Simulators/simulator-type2/docs/source/Diagrams/Norris/Originals/B&W&C.gif

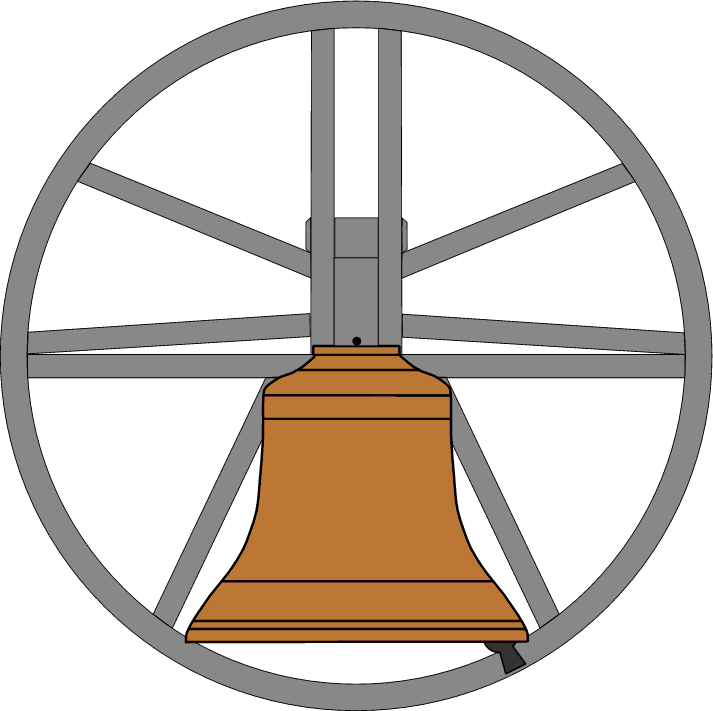
docs/source/Diagrams/Norris/Originals/B&W&C.gif
