Simulators/simulator-type2/docs/source/Diagrams/Norris/Originals/W&R.gif

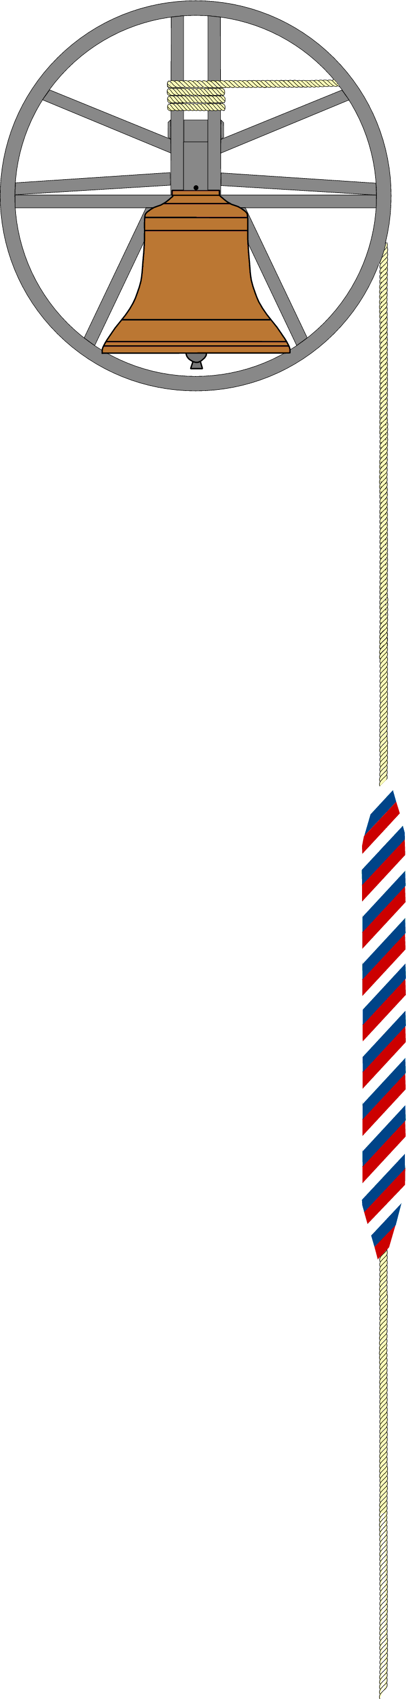
docs/source/Diagrams/Norris/Originals/W&R.gif
