Simulators/simulator-type2/docs/source/Diagrams/Norris/Originals/wheelalone_ORIGINAL.gif

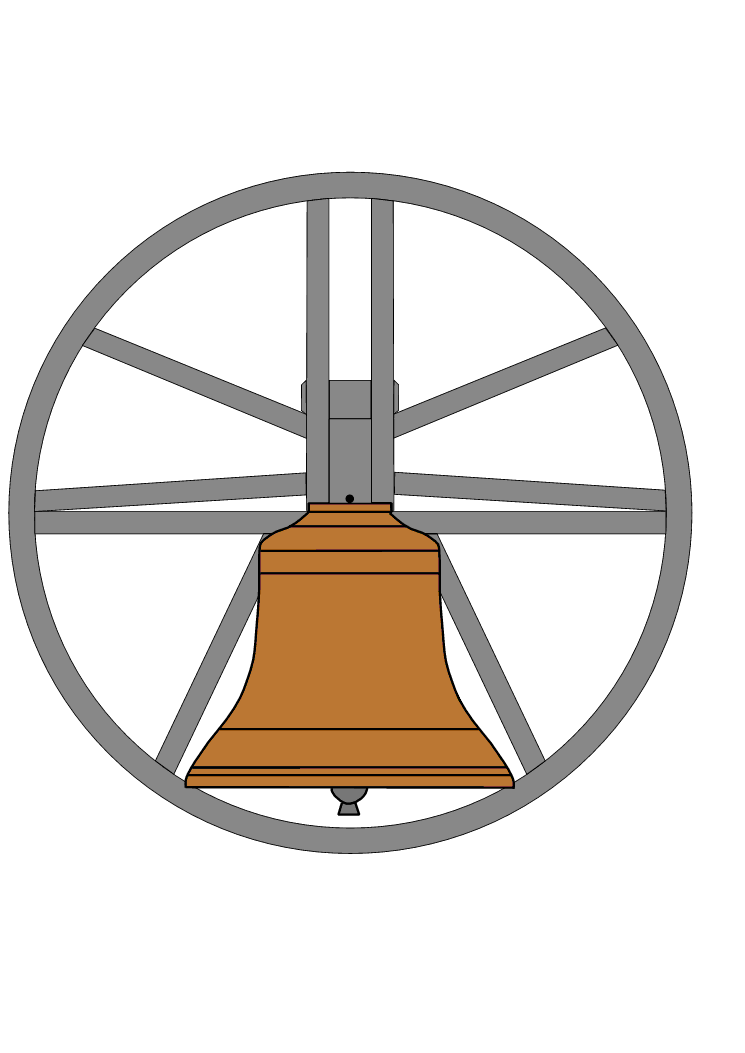
docs/source/Diagrams/Norris/Originals/wheelalone_ORIGINAL.gif
