Simulators/simulator-type2/docs/source/Diagrams/Norris/Remixed/bell_wheel_belldown.gif

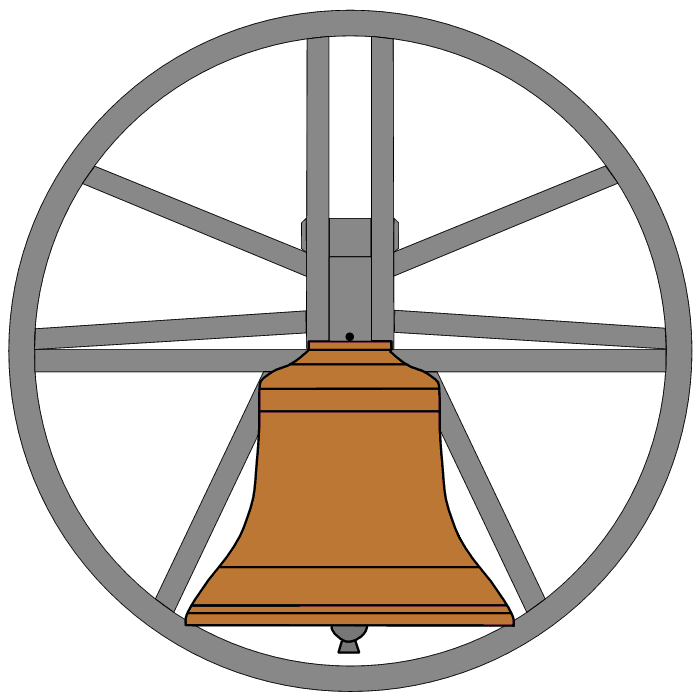
docs/source/Diagrams/Norris/Remixed/bell_wheel_belldown.gif
