Simulators/simulator-type2/docs/source/Diagrams/Norris/Remixed/bell_wheel_clappershift_down_right.gif

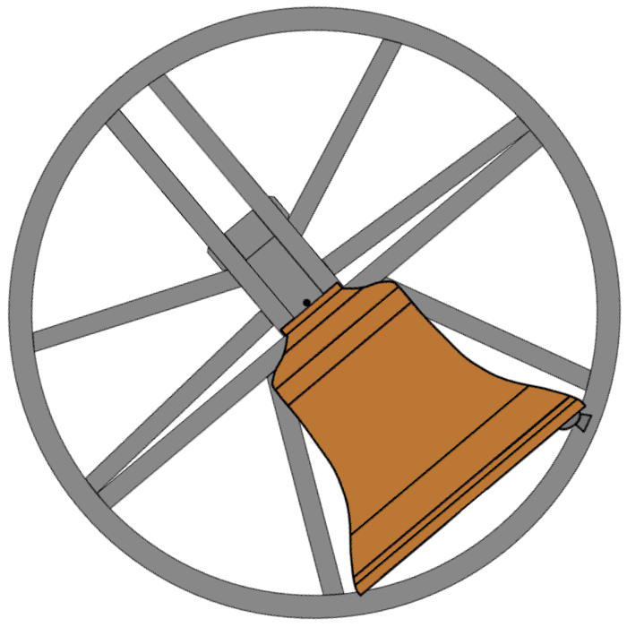
docs/source/Diagrams/Norris/Remixed/bell_wheel_clappershift_down_right.gif
