Simulators/simulator-type2/docs/source/Diagrams/Norris/Remixed/bell_wheel_clappershift_left.gif

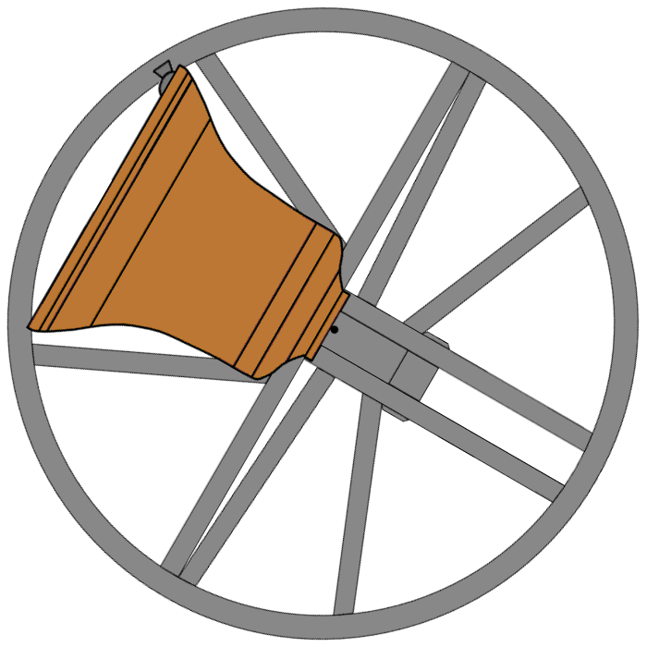
docs/source/Diagrams/Norris/Remixed/bell_wheel_clappershift_left.gif
