Simulators/simulator-type2/docs/source/Diagrams/Norris/Remixed/bell_wheel_clappershift_right.gif

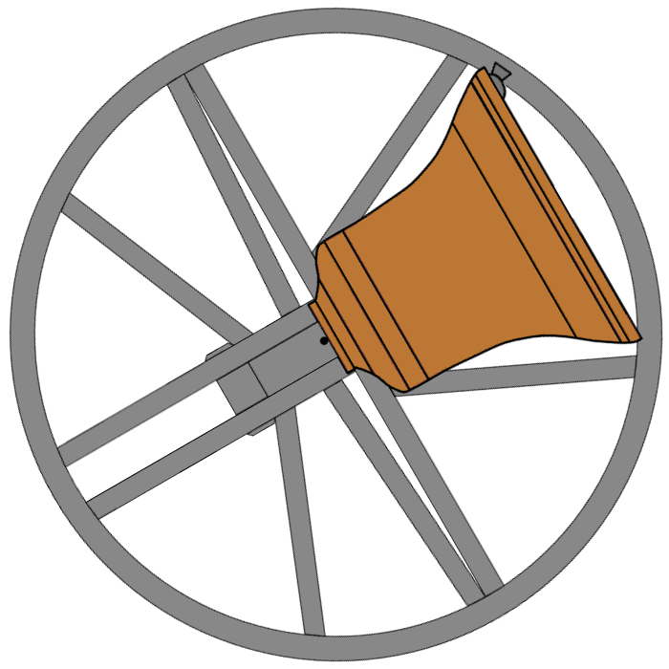
docs/source/Diagrams/Norris/Remixed/bell_wheel_clappershift_right.gif
