Simulators/simulator-type2/docs/source/Diagrams/Norris/Remixed/positions_twin_sensor_down_v0.1.png

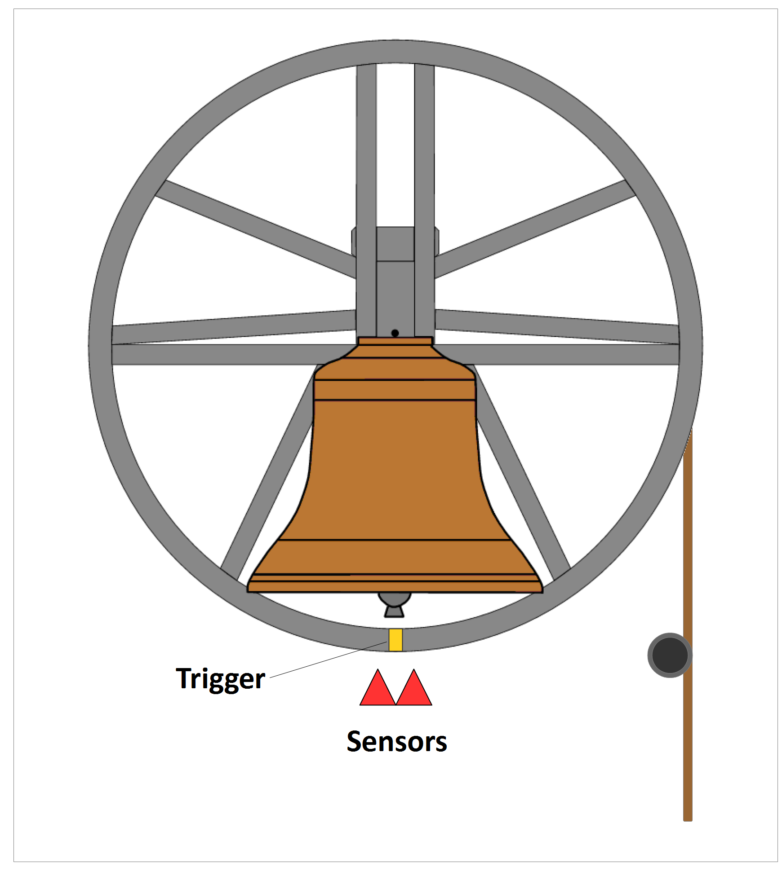
docs/source/Diagrams/Norris/Remixed/positions_twin_sensor_down_v0.1.png
