Simulators/simulator-type2/docs/source/Diagrams/Norris/Remixed/positions_twin_trigger_down_v0.1.png

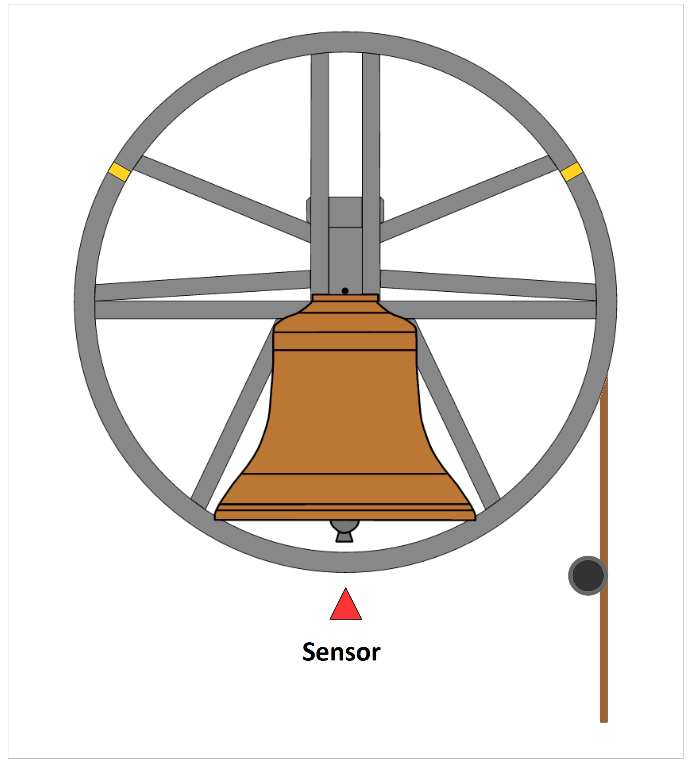
docs/source/Diagrams/Norris/Remixed/positions_twin_trigger_down_v0.1.png
