Simulators/simulator-type2/docs/source/Diagrams/PNG/06 Tech Ref/MAXIM FanOut Rx Diagram v1.0.png

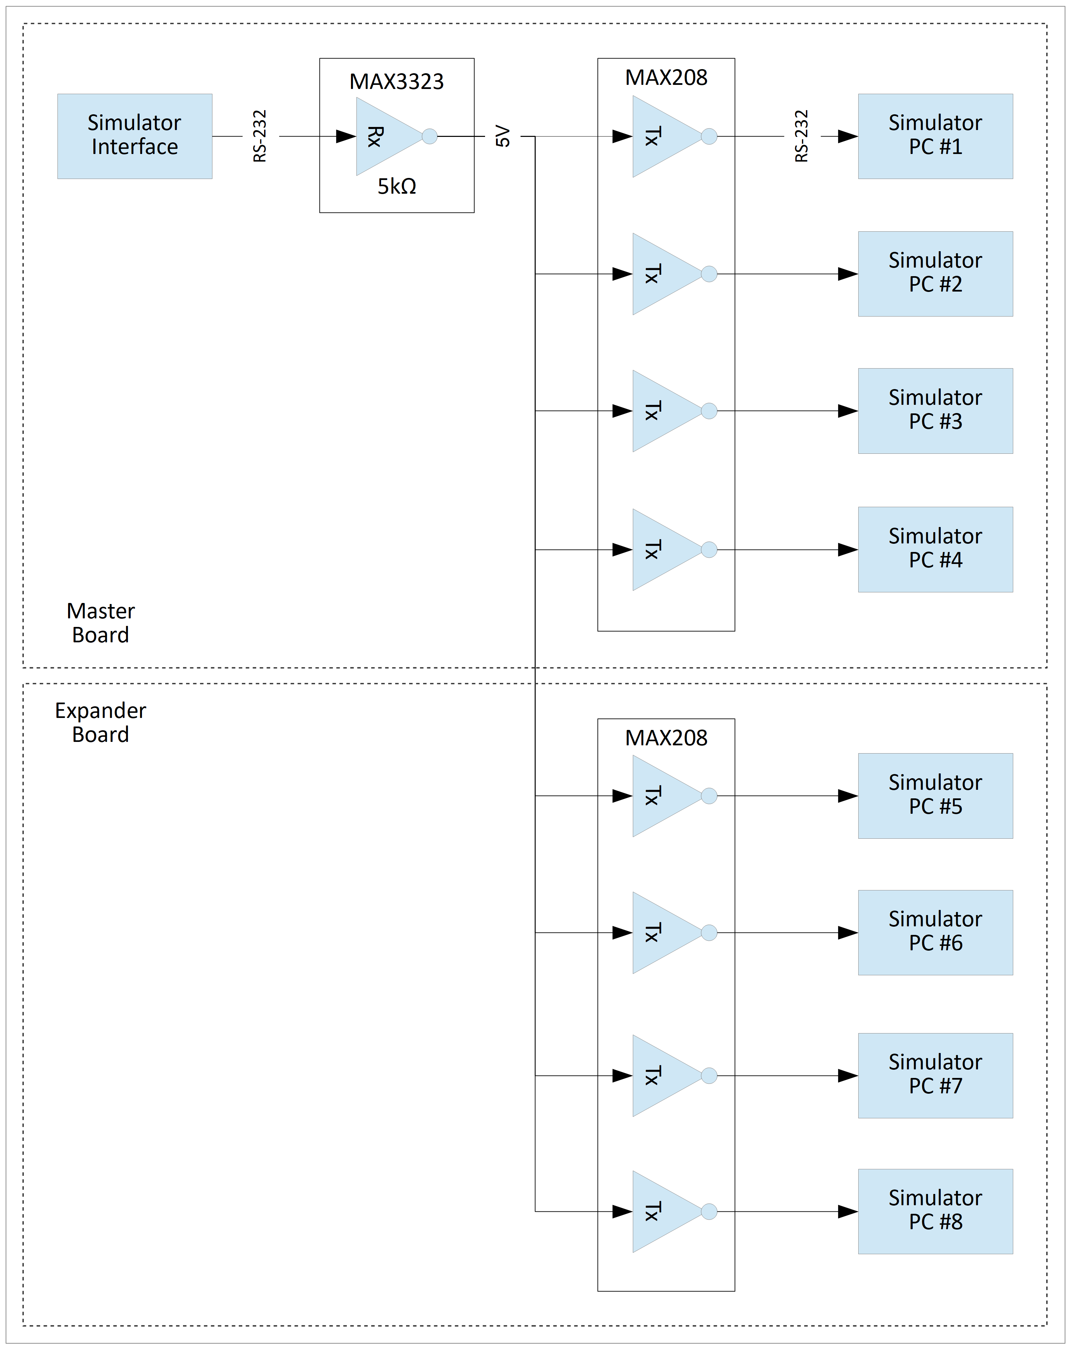
docs/source/Diagrams/PNG/06 Tech Ref/MAXIM FanOut Rx Diagram v1.0.png
