Simulators/simulator-type2/docs/source/Diagrams/PNG/06 Tech Ref/T1-T2 Adapter Cable v1.0.png

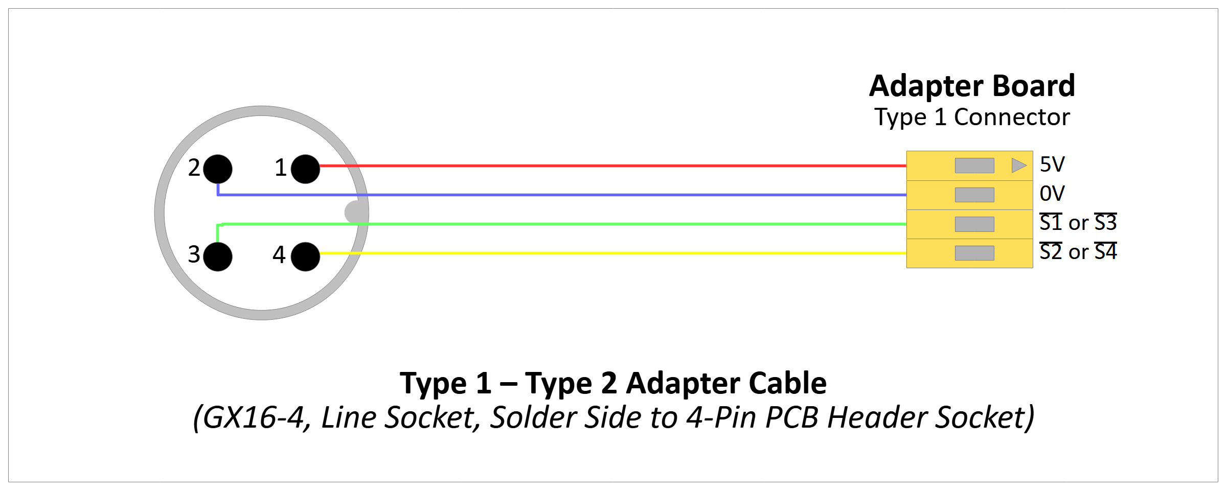
docs/source/Diagrams/PNG/06 Tech Ref/T1-T2 Adapter Cable v1.0.png
