Simulators/simulator-type2/docs/source/Diagrams/PNG/06 Tech Ref/T1-T2 Type 1 Interface Dual Connectors v1.0.png

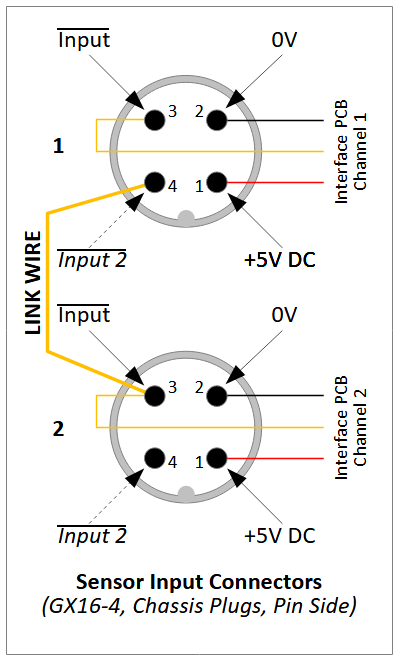
docs/source/Diagrams/PNG/06 Tech Ref/T1-T2 Type 1 Interface Dual Connectors v1.0.png
