Simulators/simulator-type2/docs/source/Diagrams/PNG/06 Tech Ref/T2 Basic Splitter RJ45 Connector v1.0.png

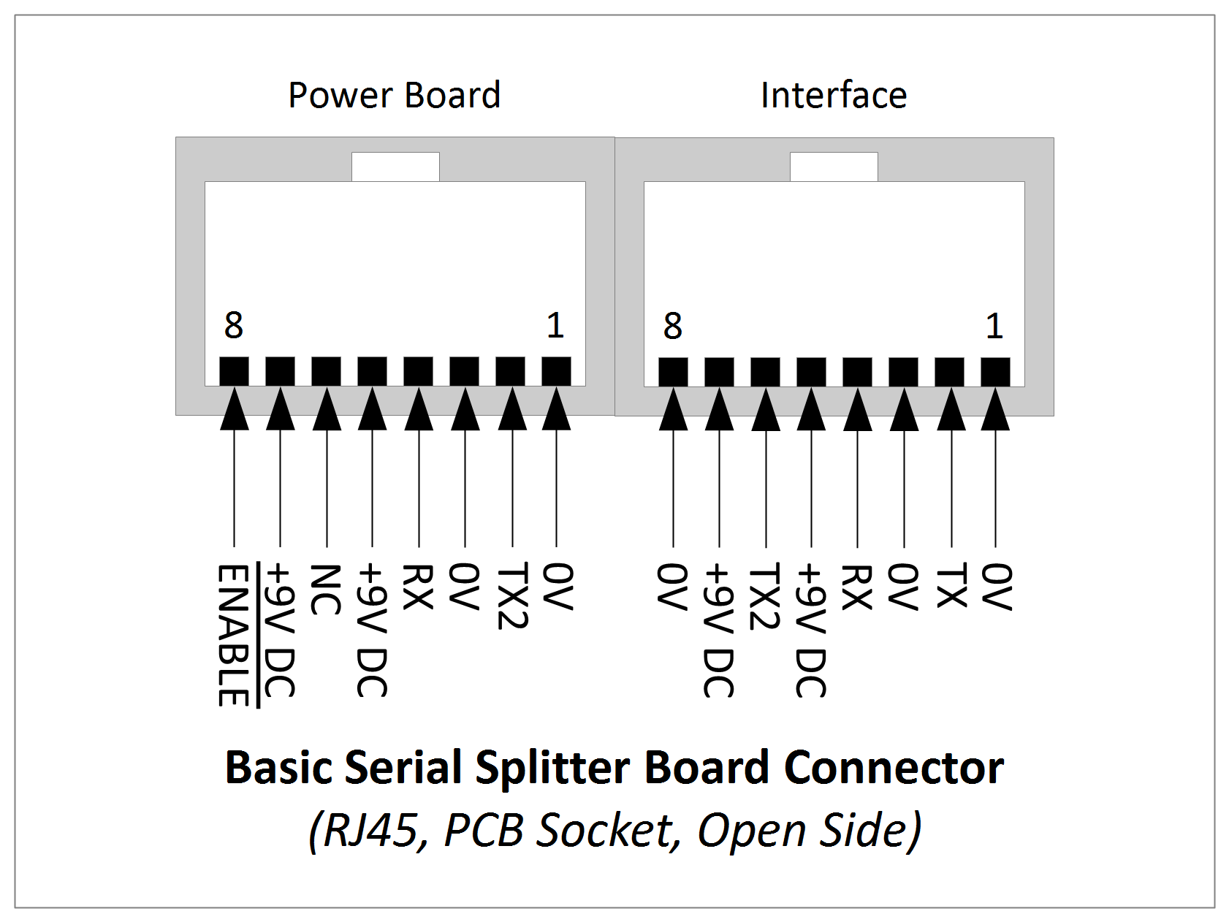
docs/source/Diagrams/PNG/06 Tech Ref/T2 Basic Splitter RJ45 Connector v1.0.png
