Simulators/simulator-type2/docs/source/Diagrams/PNG/06 Tech Ref/T2 Channel Map.png

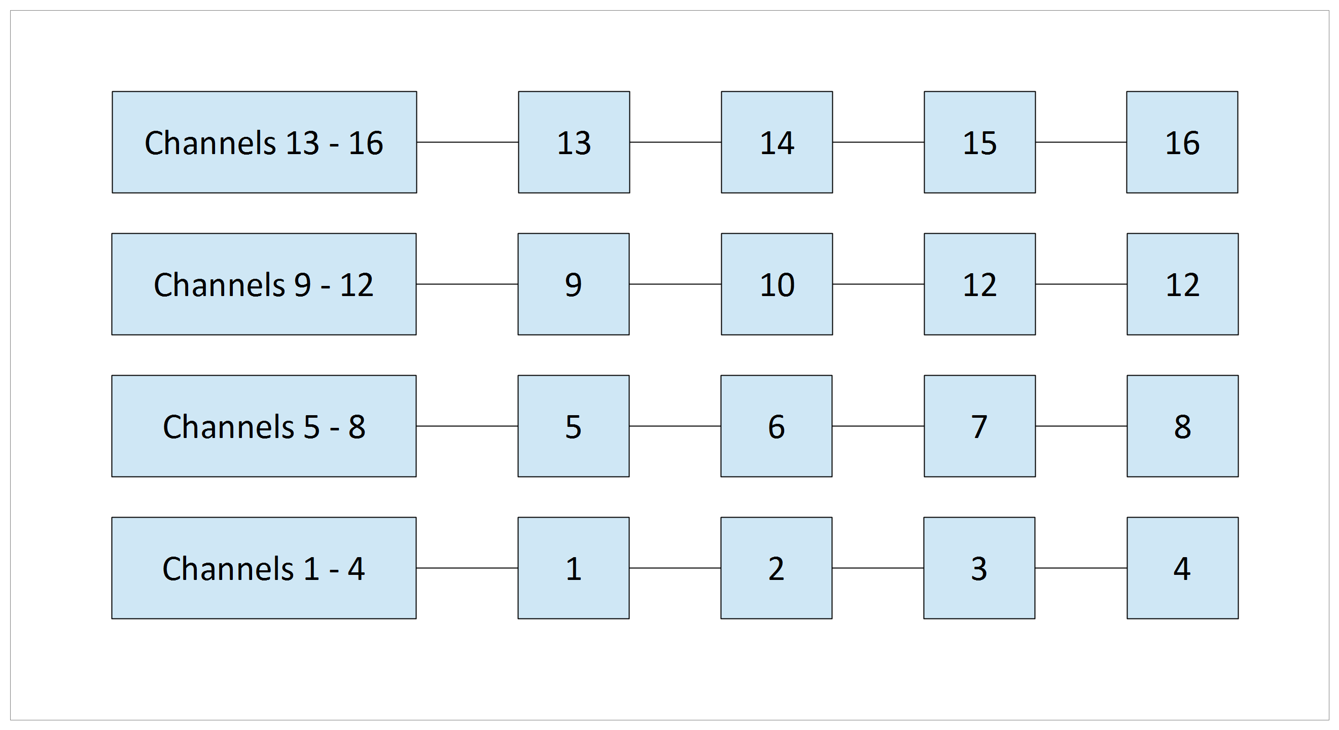
docs/source/Diagrams/PNG/06 Tech Ref/T2 Channel Map.png
