Simulators/simulator-type2/docs/source/Diagrams/PNG/06 Tech Ref/T2 DB9 2nd PC Module v1.0.png

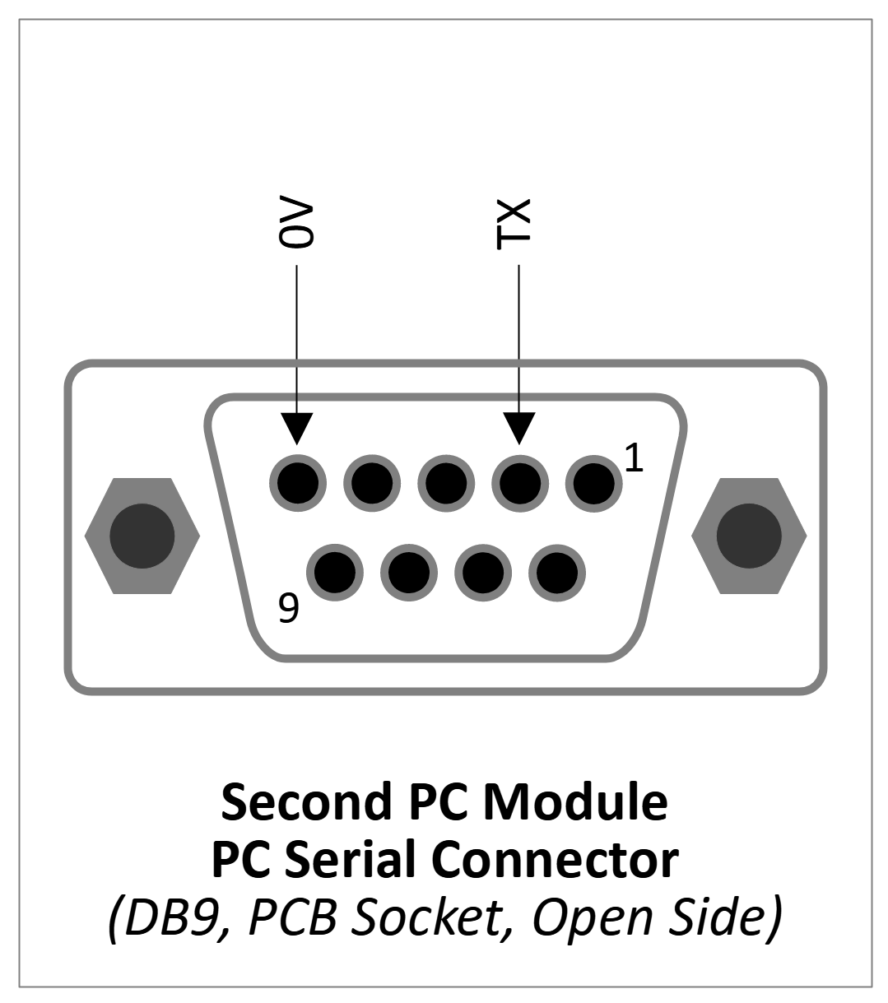
docs/source/Diagrams/PNG/06 Tech Ref/T2 DB9 2nd PC Module v1.0.png
