Simulators/simulator-type2/docs/source/Diagrams/PNG/06 Tech Ref/T2 Double Pulse Diagram v0.1.png

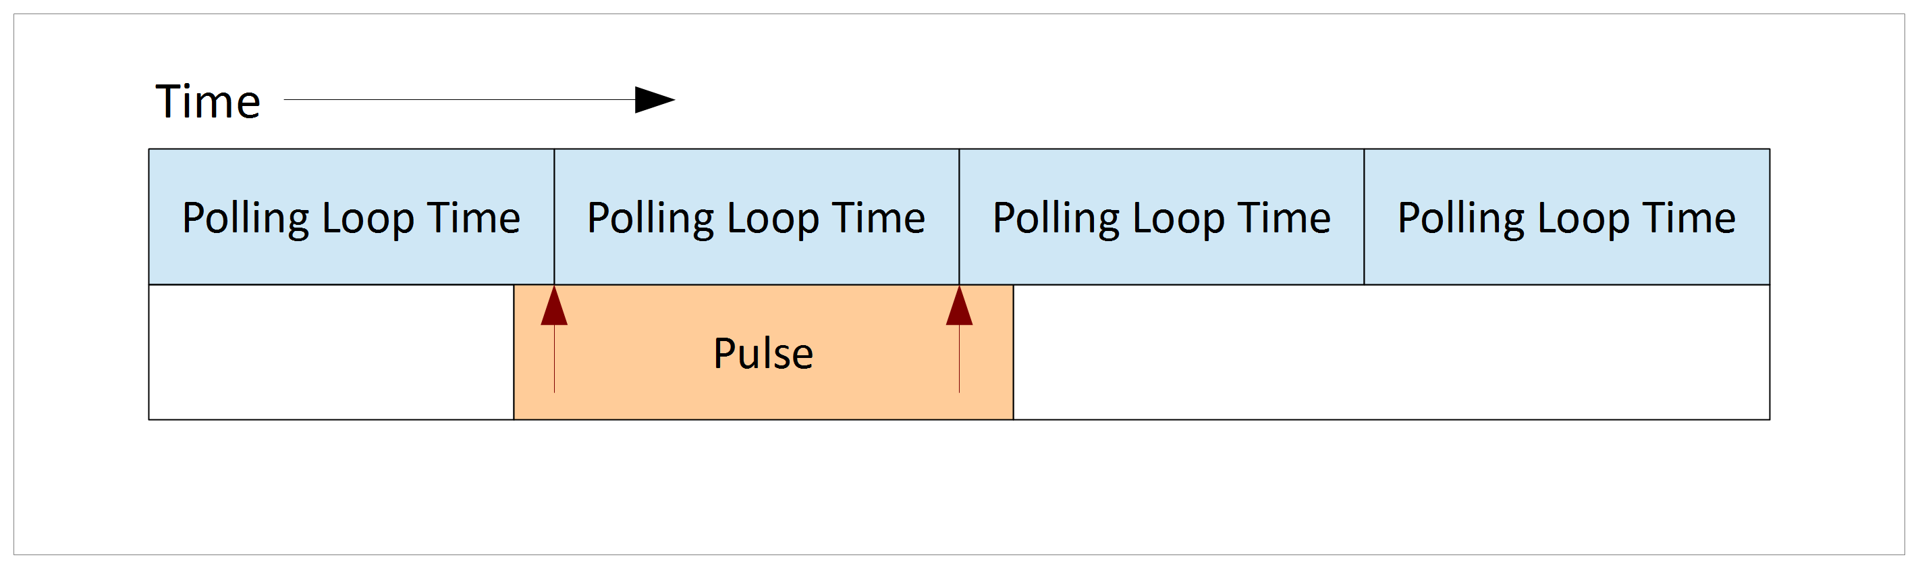
docs/source/Diagrams/PNG/06 Tech Ref/T2 Double Pulse Diagram v0.1.png
