Simulators/simulator-type2/docs/source/Diagrams/PNG/06 Tech Ref/T2 Dual Sensor Backstroke v0.1.png

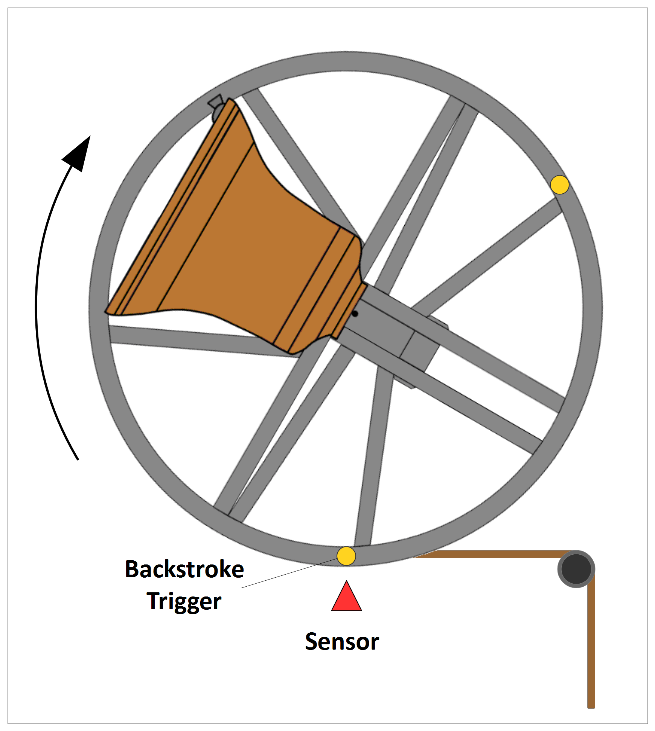
docs/source/Diagrams/PNG/06 Tech Ref/T2 Dual Sensor Backstroke v0.1.png
