Simulators/simulator-type2/docs/source/Diagrams/PNG/06 Tech Ref/T2 Dual Sensor Handstroke v0.1.png

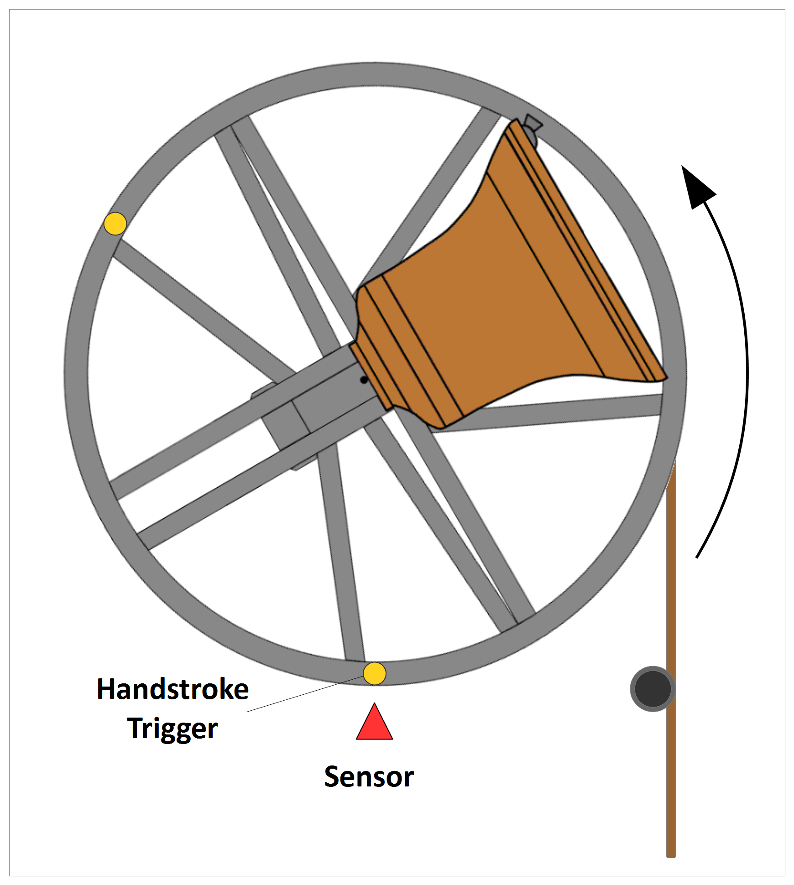
docs/source/Diagrams/PNG/06 Tech Ref/T2 Dual Sensor Handstroke v0.1.png
