Simulators/simulator-type2/docs/source/Diagrams/PNG/06 Tech Ref/T2 Polarity Diode Diagram v1.0.png

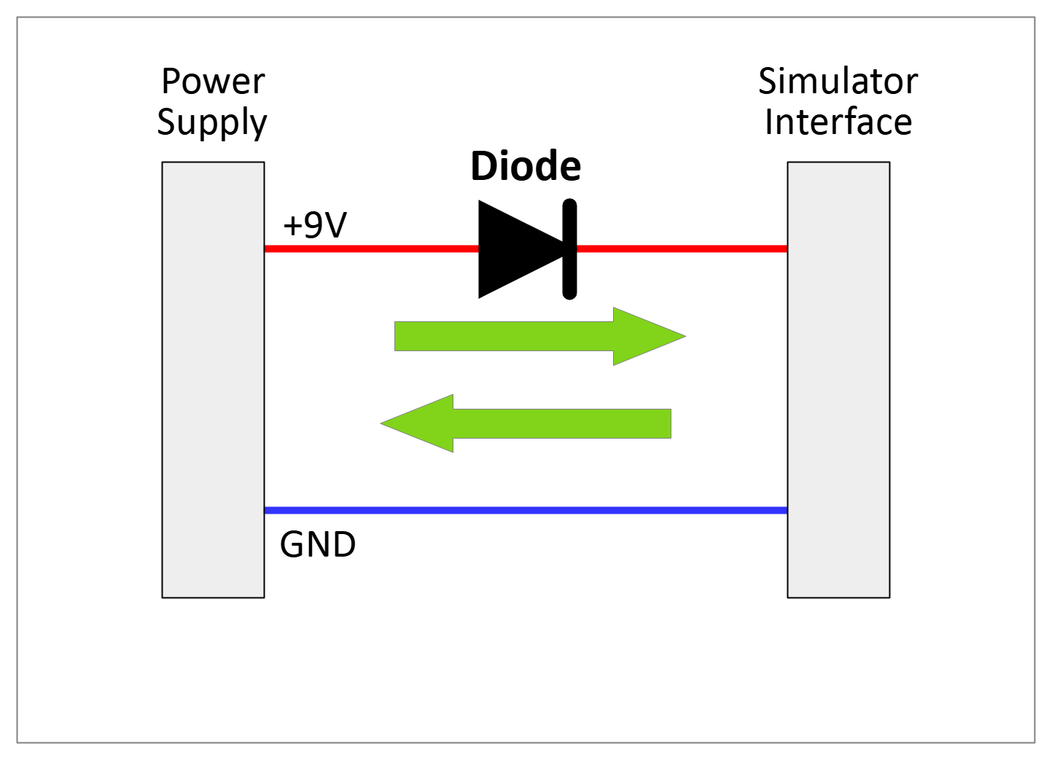
docs/source/Diagrams/PNG/06 Tech Ref/T2 Polarity Diode Diagram v1.0.png
