Simulators/simulator-type2/docs/source/Diagrams/PNG/07 Multi-PC/T2 Basic Splitter Daisy Chain v1.0.png

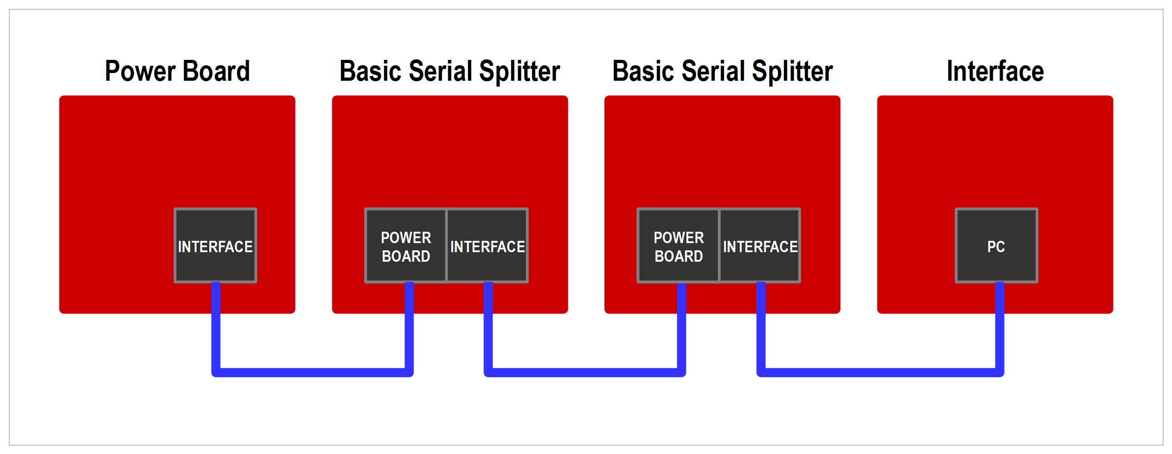
docs/source/Diagrams/PNG/07 Multi-PC/T2 Basic Splitter Daisy Chain v1.0.png
