Simulators/simulator-type2/docs/source/Diagrams/PNG/07 Multi-PC/T2 Basic Splitter Voltages.png

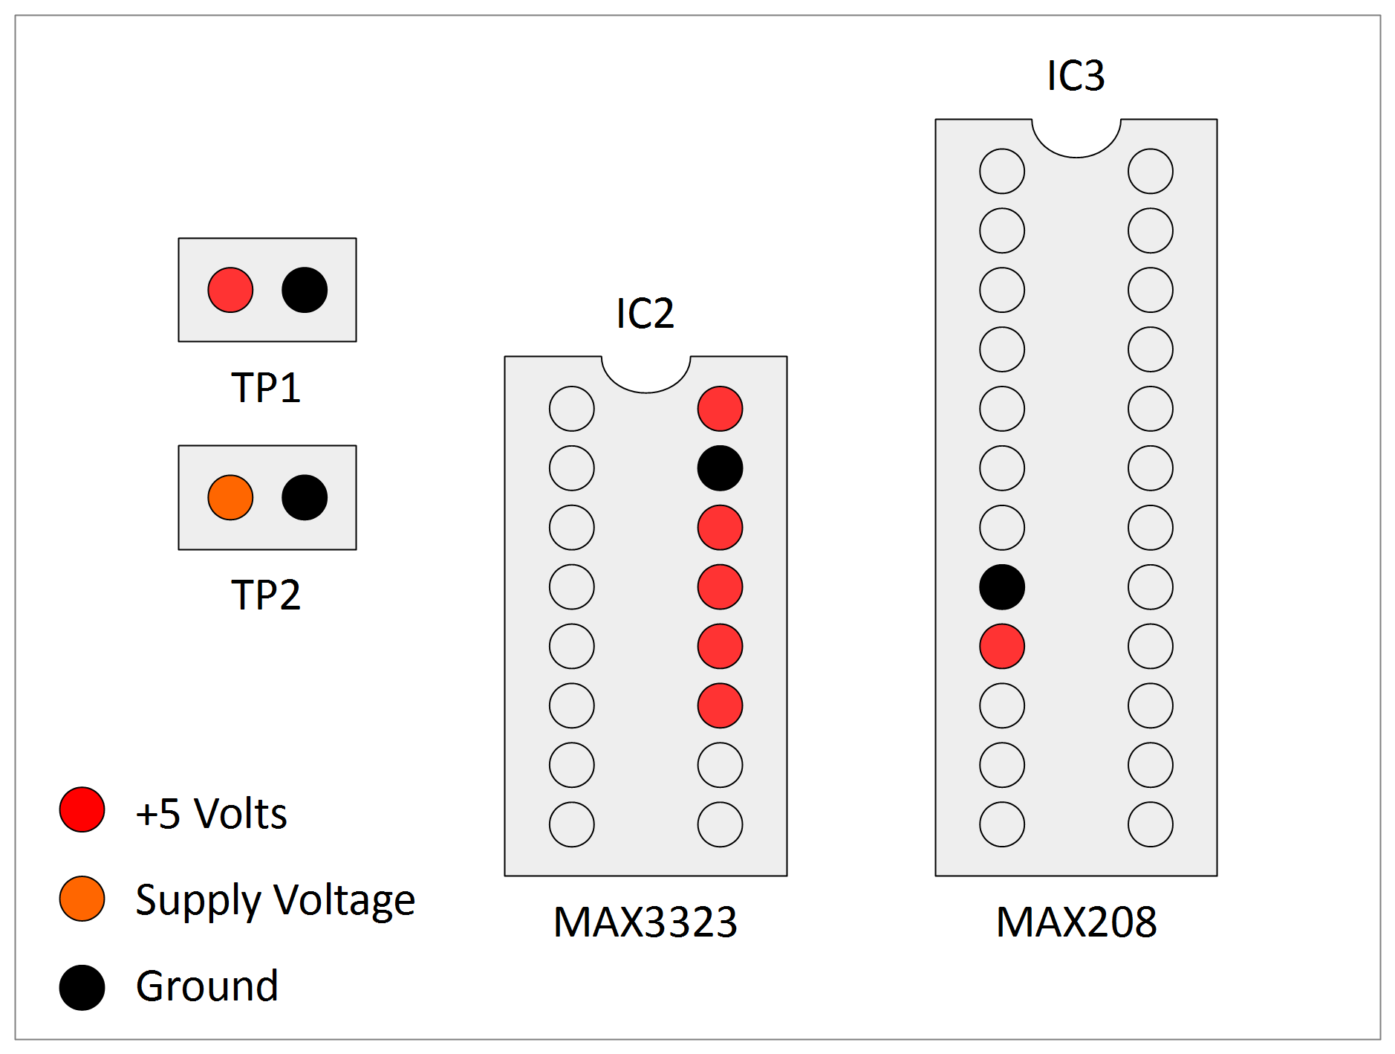
docs/source/Diagrams/PNG/07 Multi-PC/T2 Basic Splitter Voltages.png
