Simulators/simulator-type2/docs/source/Diagrams/PNG/07 Multi-PC/T2 Second PC Daisy Chain v1.0.png

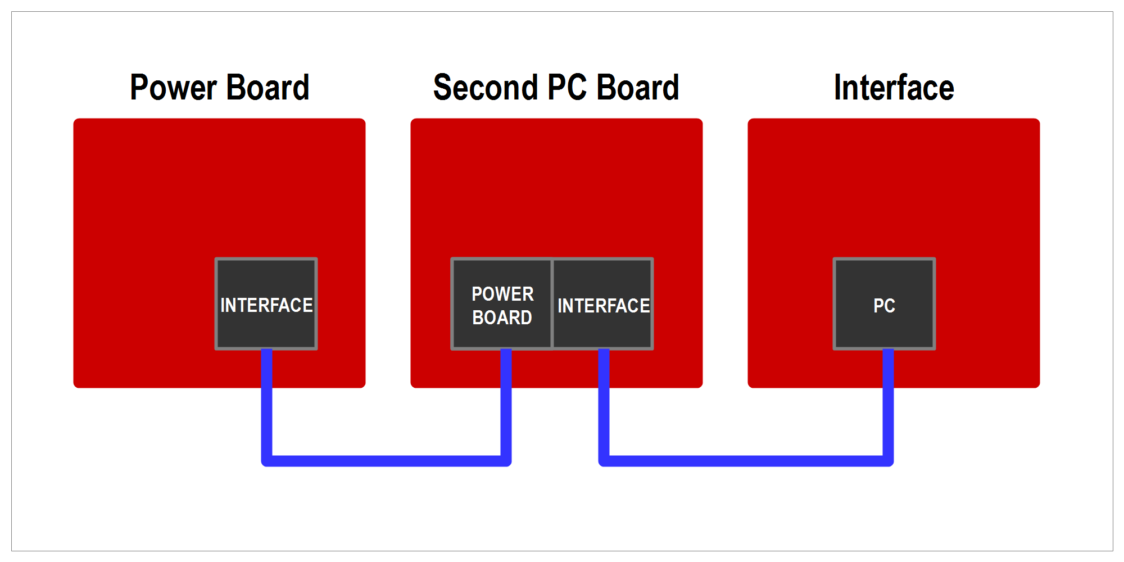
docs/source/Diagrams/PNG/07 Multi-PC/T2 Second PC Daisy Chain v1.0.png
