Simulators/simulator-type2/docs/source/Diagrams/PNG/DocMaps/T2 DocMap 3 Config Abel v2.png

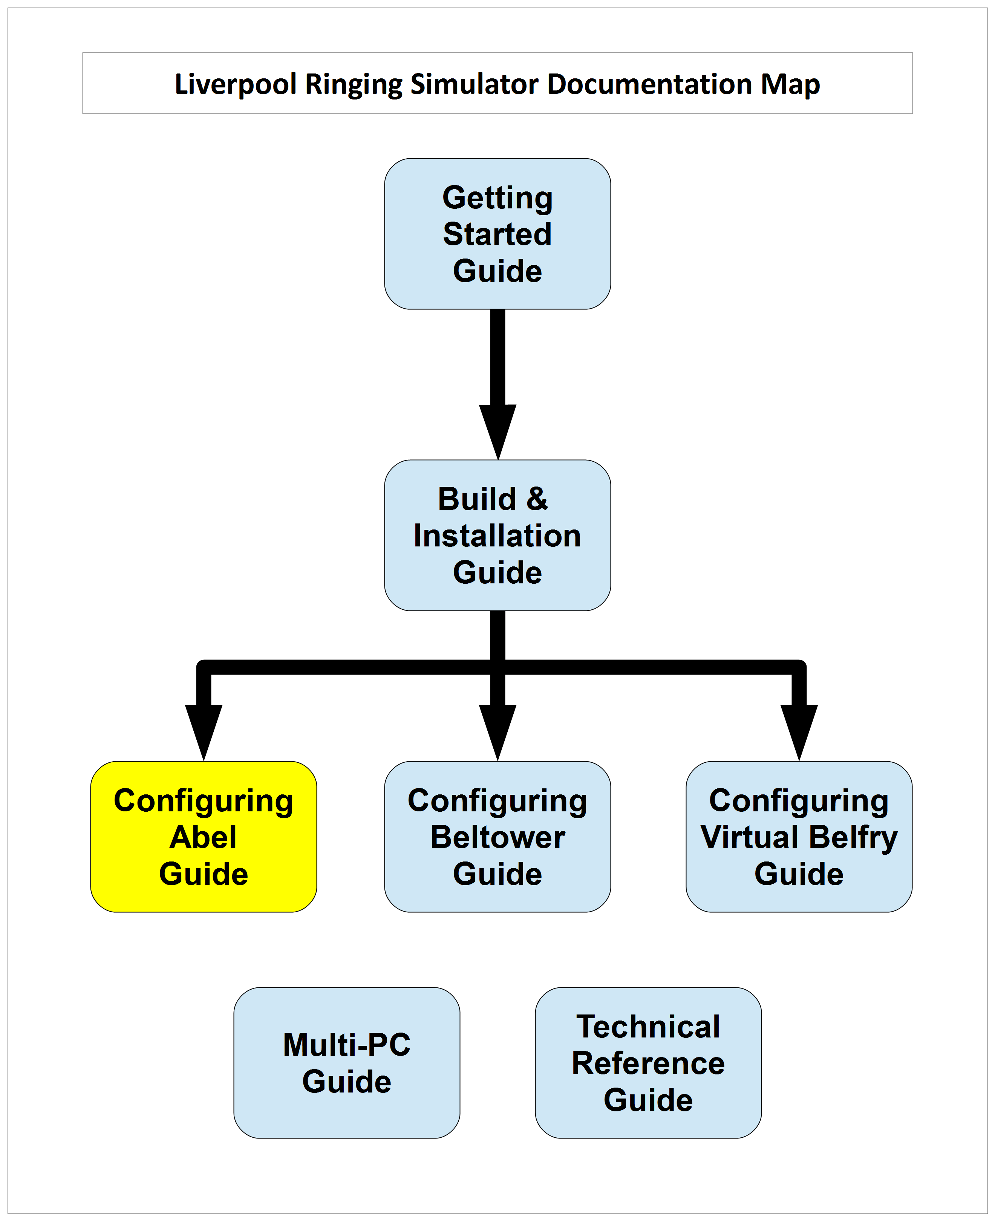
docs/source/Diagrams/PNG/DocMaps/T2 DocMap 3 Config Abel v2.png
