Simulators/simulator-type2/docs/source/Diagrams/PNG/DocMaps/T2 DocMap 4 Config Beltower v2.png

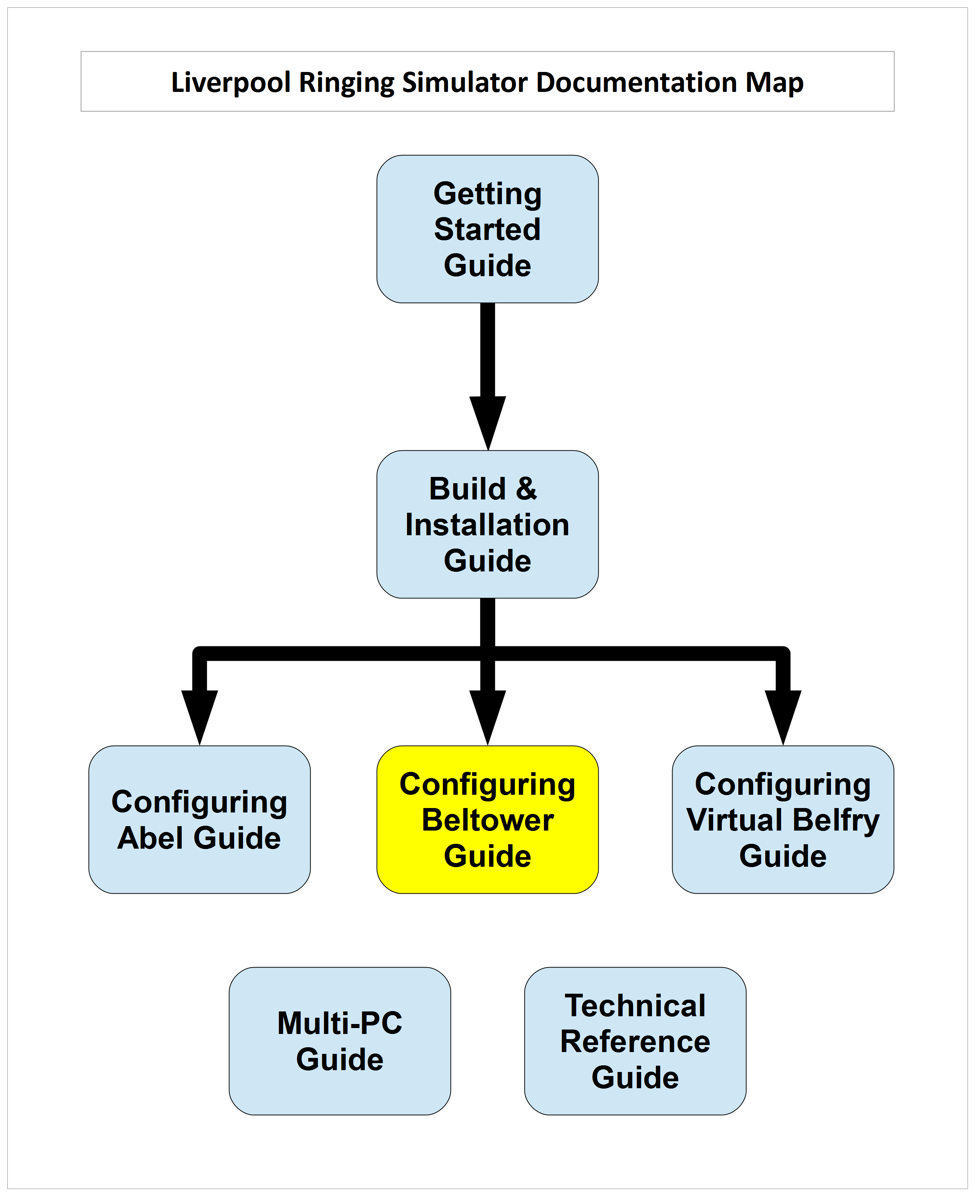
docs/source/Diagrams/PNG/DocMaps/T2 DocMap 4 Config Beltower v2.png
