Simulators/simulator-type2/docs/source/Diagrams/Vecteezy/PC Ports Vecteezy 9Pin.png

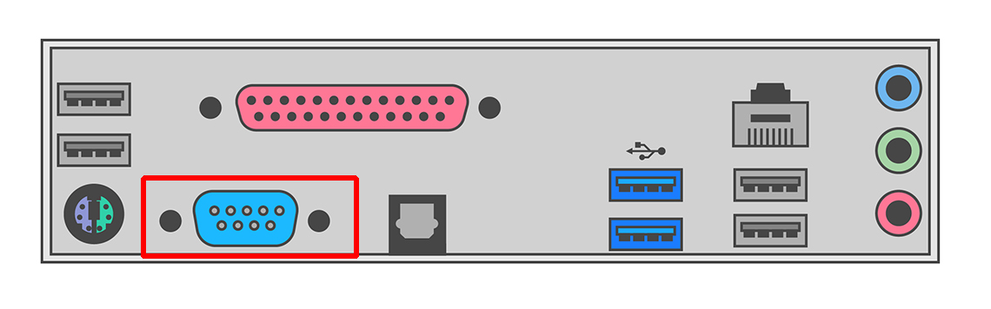
docs/source/Diagrams/Vecteezy/PC Ports Vecteezy 9Pin.png
