Simulators/simulator-type2/docs/source/Diagrams/Vecteezy/PC Ports Vecteezy USB.png

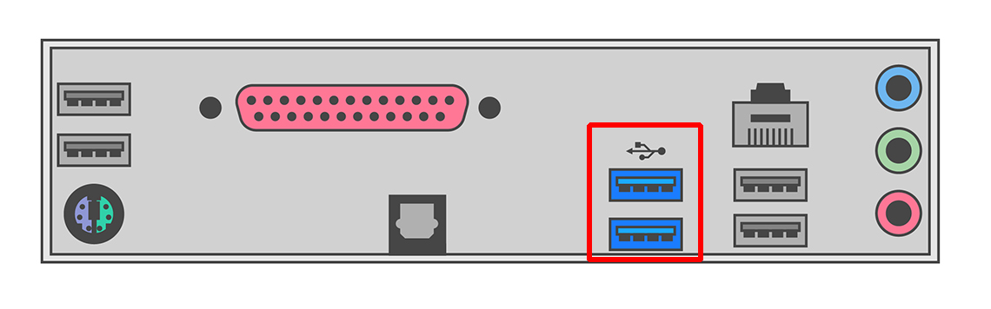
docs/source/Diagrams/Vecteezy/PC Ports Vecteezy USB.png
