Simulators/simulator-type2/docs/source/Diagrams/Vecteezy/USB Port Mother Board Free Vector.jpg

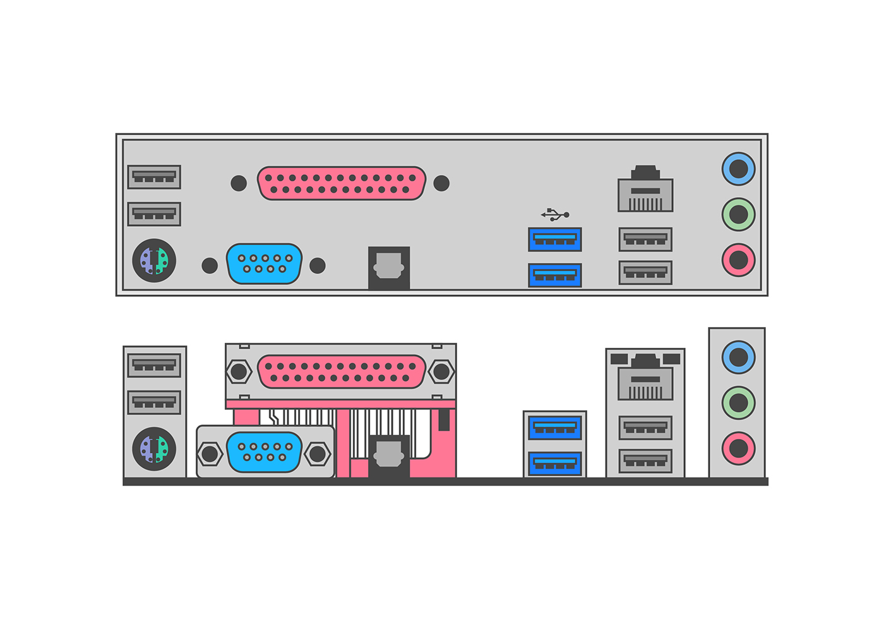
docs/source/Diagrams/Vecteezy/USB Port Mother Board Free Vector.jpg
