Simulators/simulator-type2/docs/source/Images/CRO/DS2302A_20171216-192610.png

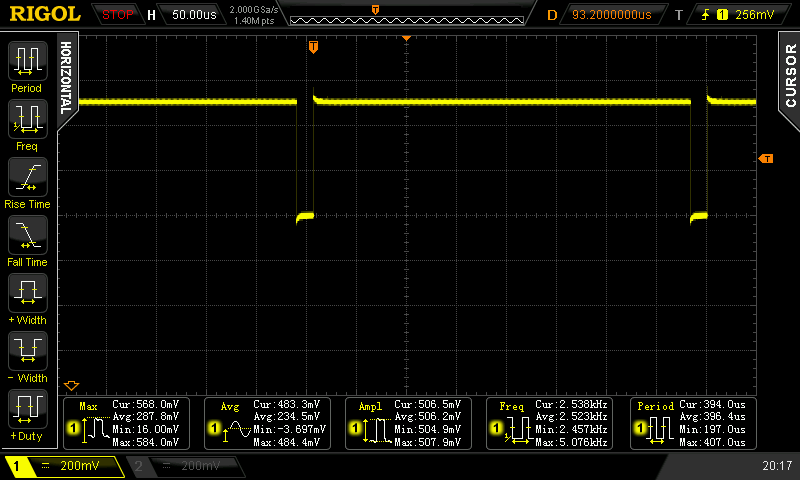
docs/source/Images/CRO/DS2302A_20171216-192610.png
