Simulators/simulator-type2/docs/source/Images/CRO/DS2302A_20180502-181701.png

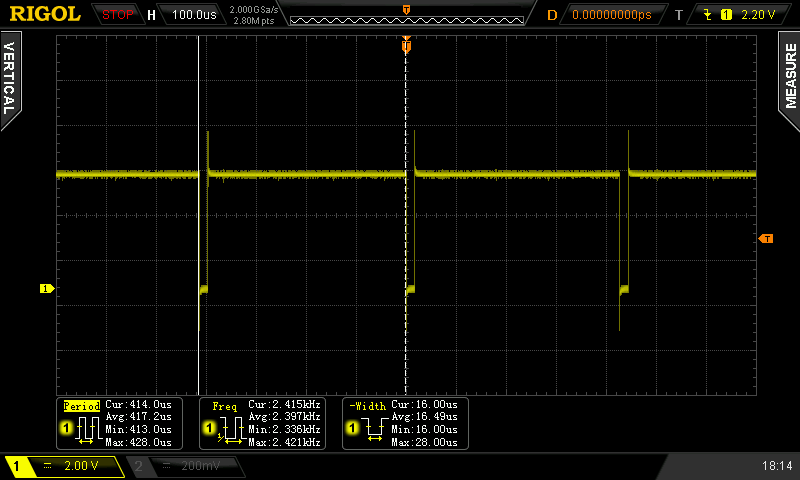
docs/source/Images/CRO/DS2302A_20180502-181701.png
