Simulators/simulator-type2/docs/source/Images/CRO/Latency Scope Annotated.png

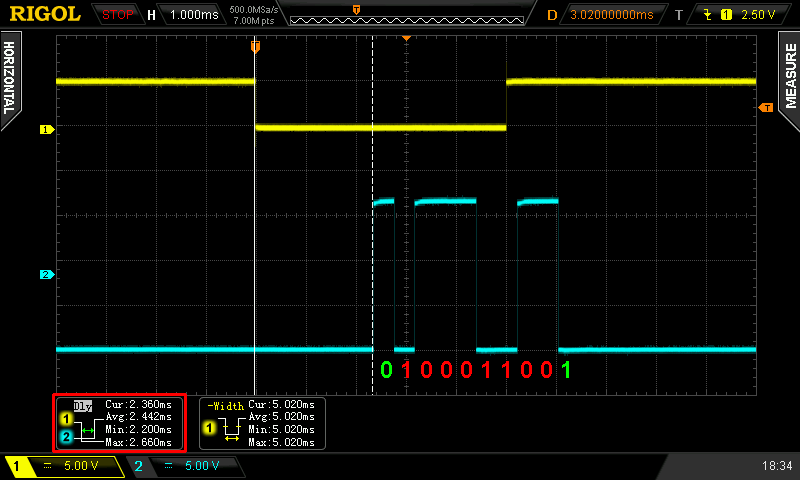
docs/source/Images/CRO/Latency Scope Annotated.png
