Simulators/simulator-type2/docs/source/Images/CRO/sigrok_debounce_timer.PNG

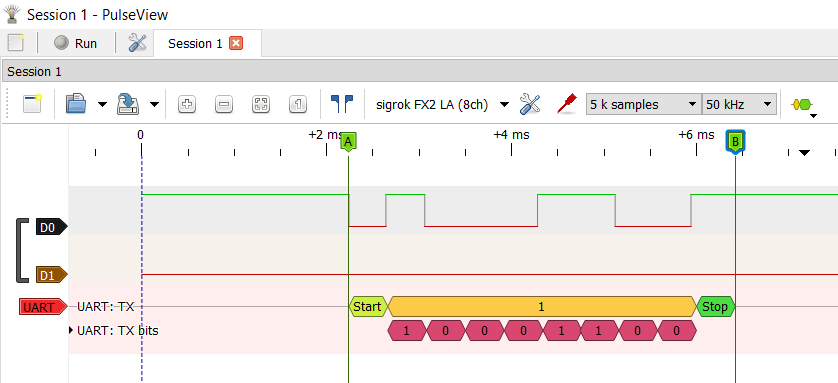
docs/source/Images/CRO/sigrok_debounce_timer.PNG
