Simulators/simulator-type2/docs/source/Images/Hardware/Basic Splitter/Img_0053.jpeg

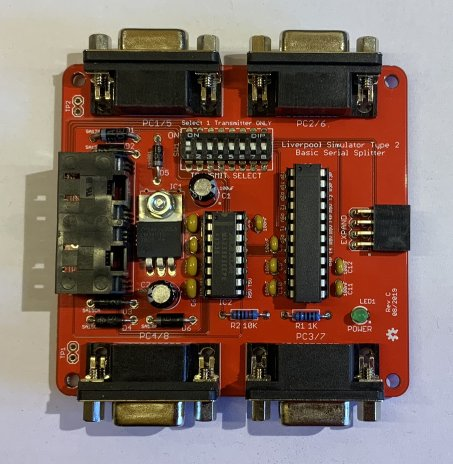
docs/source/Images/Hardware/Basic Splitter/Img_0053.jpeg
