Simulators/simulator-type2/docs/source/Images/Hardware/Basic Splitter/Img_0054.jpeg

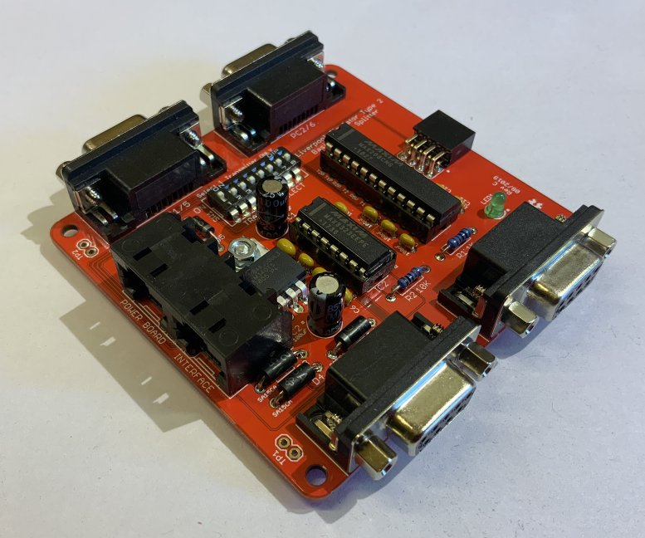
docs/source/Images/Hardware/Basic Splitter/Img_0054.jpeg
