Simulators/simulator-type2/docs/source/Images/Hardware/Basic Splitter/Img_0664.jpg

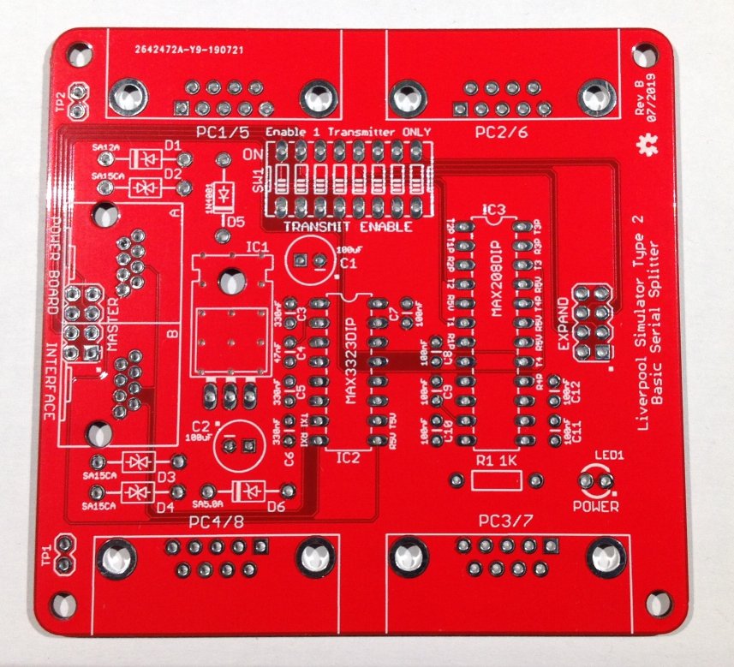
docs/source/Images/Hardware/Basic Splitter/Img_0664.jpg
