Simulators/simulator-type2/docs/source/Images/Hardware/Basic Splitter/Img_0665.jpg

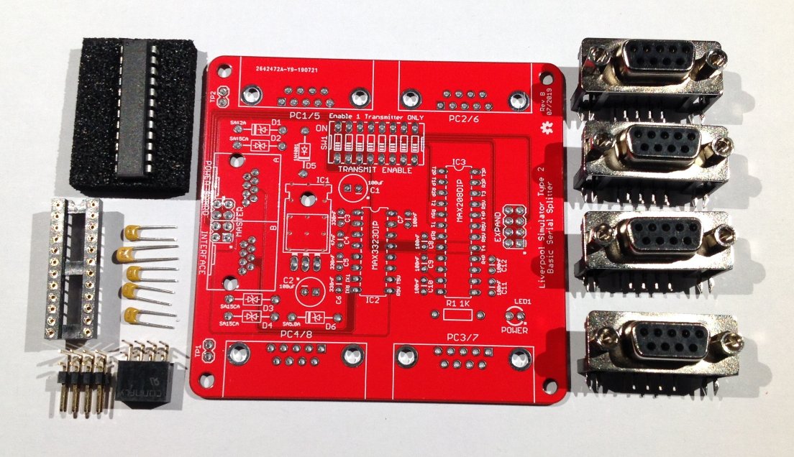
docs/source/Images/Hardware/Basic Splitter/Img_0665.jpg
