Simulators/simulator-type2/docs/source/Images/Hardware/Enclosures/Img_0061.jpeg

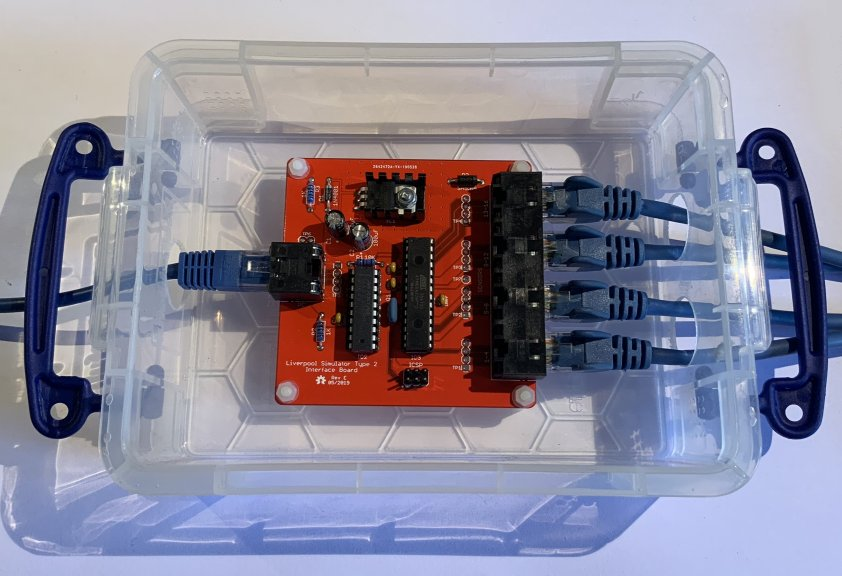
docs/source/Images/Hardware/Enclosures/Img_0061.jpeg
