Simulators/simulator-type2/docs/source/Images/Hardware/Enclosures/Img_0062.jpeg

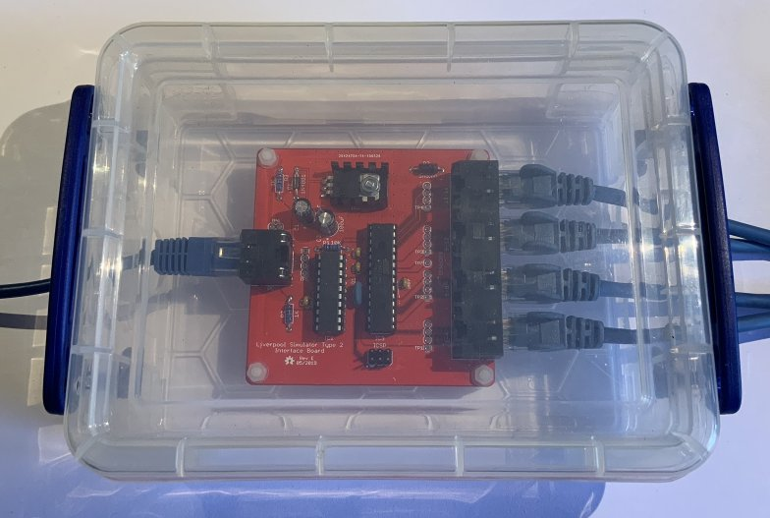
docs/source/Images/Hardware/Enclosures/Img_0062.jpeg
