Simulators/simulator-type2/docs/source/Images/Hardware/Enclosures/Img_0446.jpg

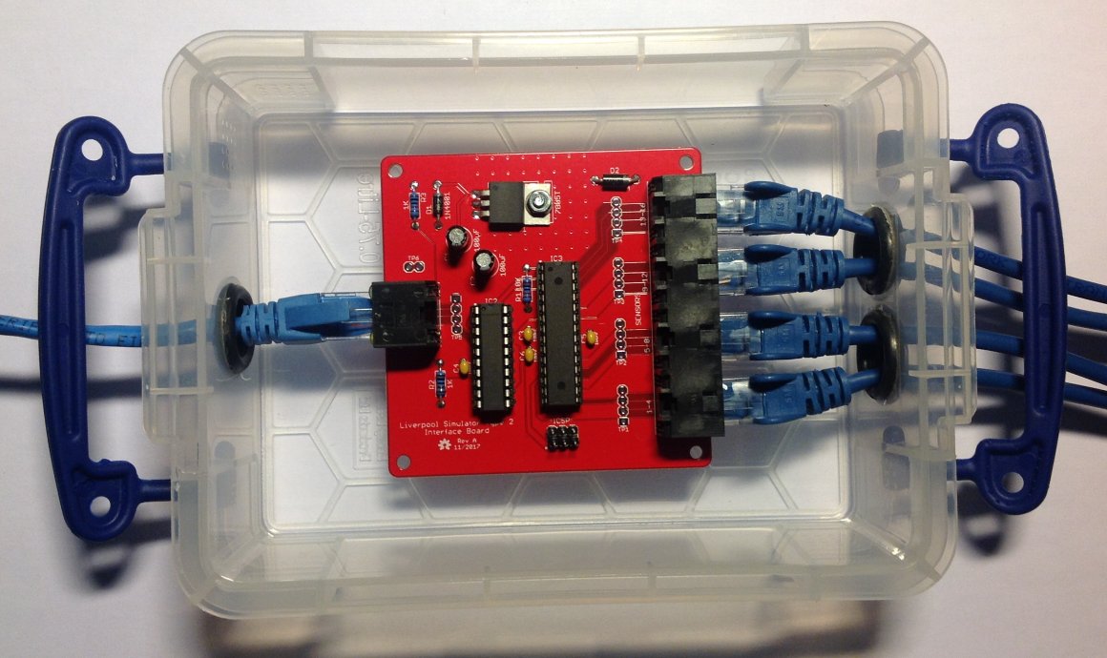
docs/source/Images/Hardware/Enclosures/Img_0446.jpg
