Simulators/simulator-type2/docs/source/Images/Hardware/Enclosures/Img_0460.jpg

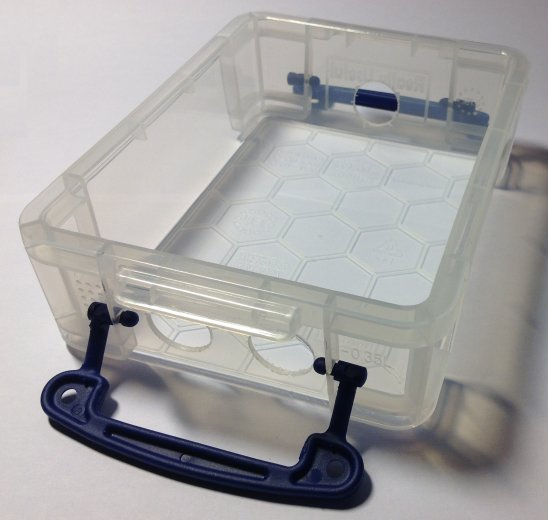
docs/source/Images/Hardware/Enclosures/Img_0460.jpg
