Simulators/simulator-type2/docs/source/Images/Hardware/Enclosures/Img_1166.jpg

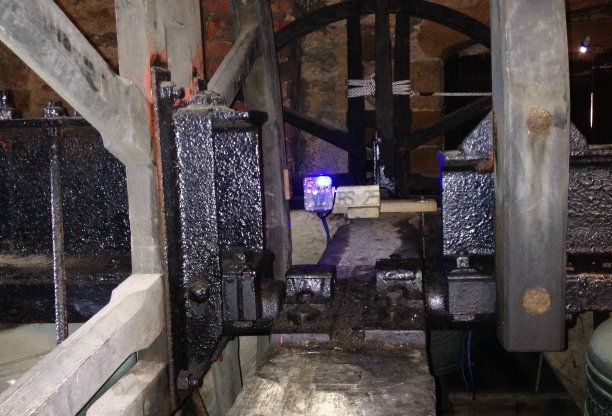
docs/source/Images/Hardware/Enclosures/Img_1166.jpg
