Simulators/simulator-type2/docs/source/Images/Hardware/Enclosures/Img_1172.jpg

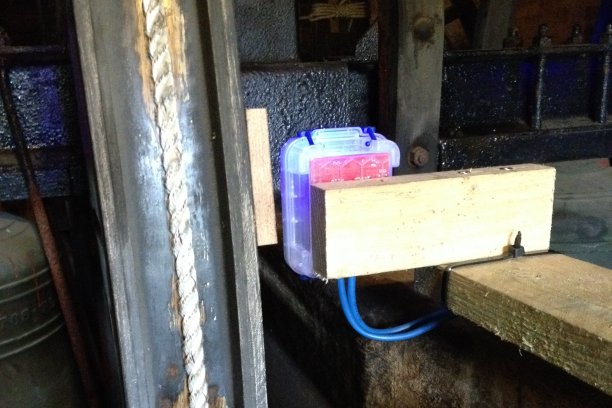
docs/source/Images/Hardware/Enclosures/Img_1172.jpg
