Simulators/simulator-type2/docs/source/Images/Hardware/Generic Sensor/Img_0442.jpg

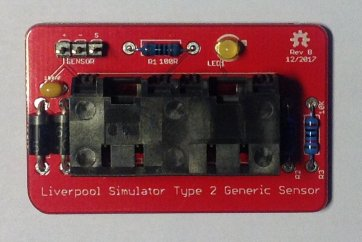
docs/source/Images/Hardware/Generic Sensor/Img_0442.jpg
