Simulators/simulator-type2/docs/source/Images/Hardware/Interface/Img_0173.jpg

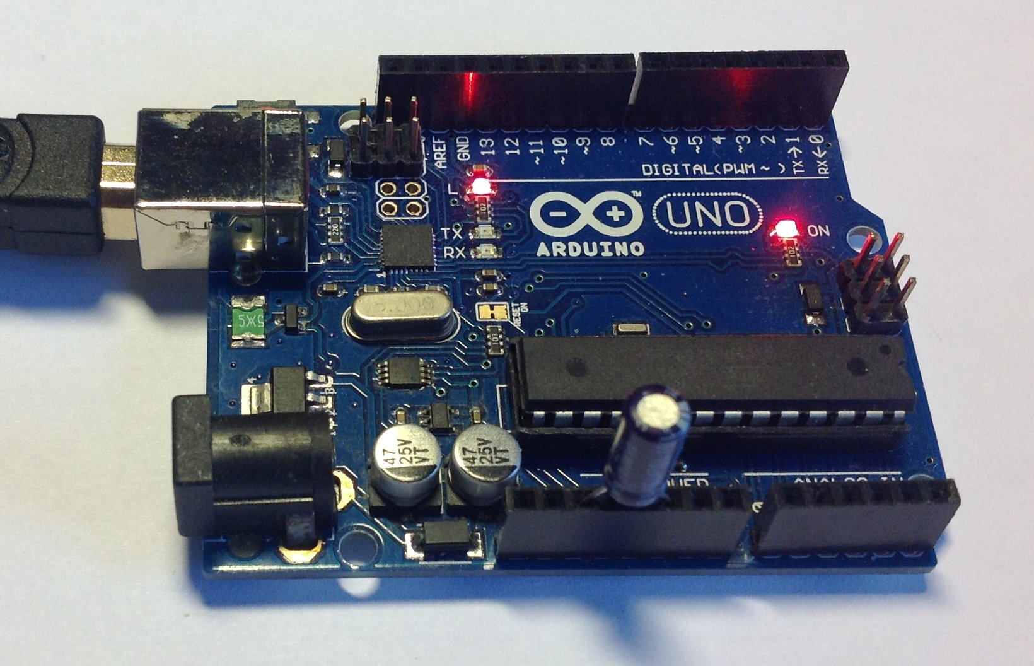
docs/source/Images/Hardware/Interface/Img_0173.jpg
