Simulators/simulator-type2/docs/source/Images/Hardware/Interface/Img_0431.jpg

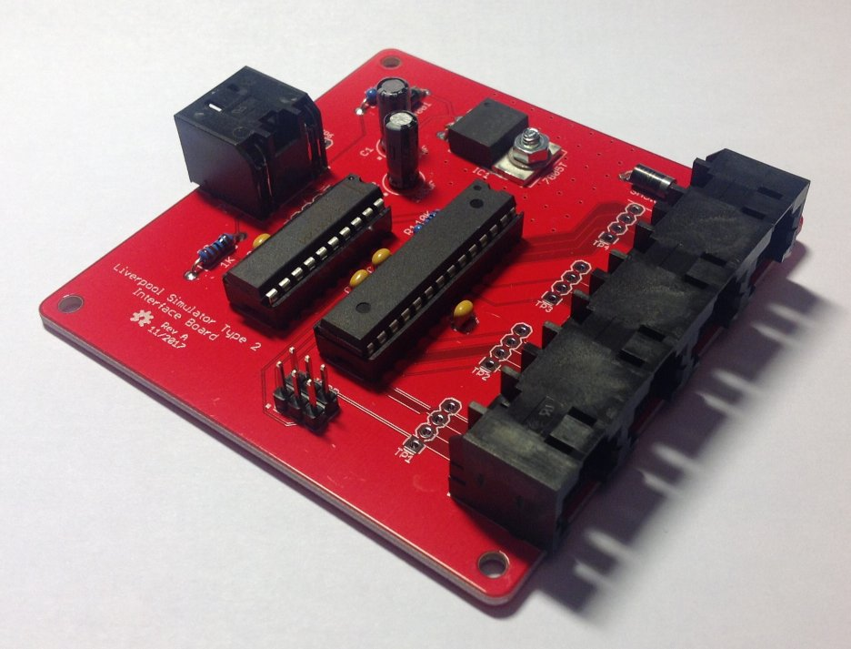
docs/source/Images/Hardware/Interface/Img_0431.jpg
