Simulators/simulator-type2/docs/source/Images/Hardware/Interface/Img_0561.jpg

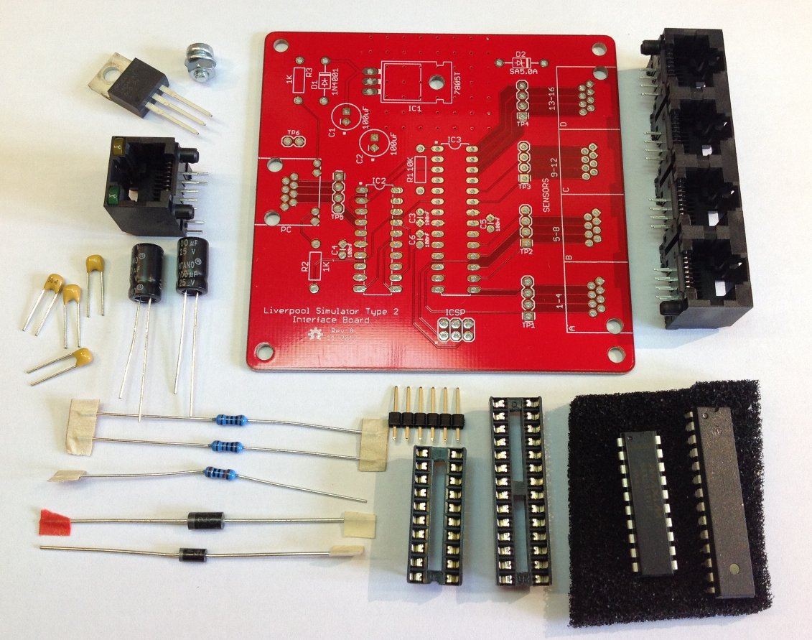
docs/source/Images/Hardware/Interface/Img_0561.jpg
