Simulators/simulator-type2/docs/source/Images/Hardware/Interface/Img_0577.jpg

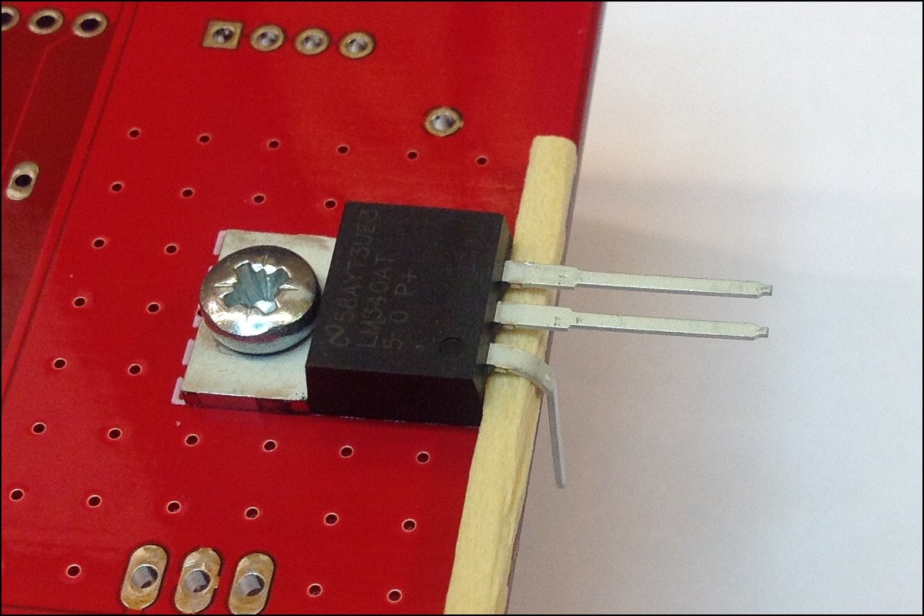
docs/source/Images/Hardware/Interface/Img_0577.jpg
