Simulators/simulator-type2/docs/source/Images/Hardware/Interface/Img_0578.jpg

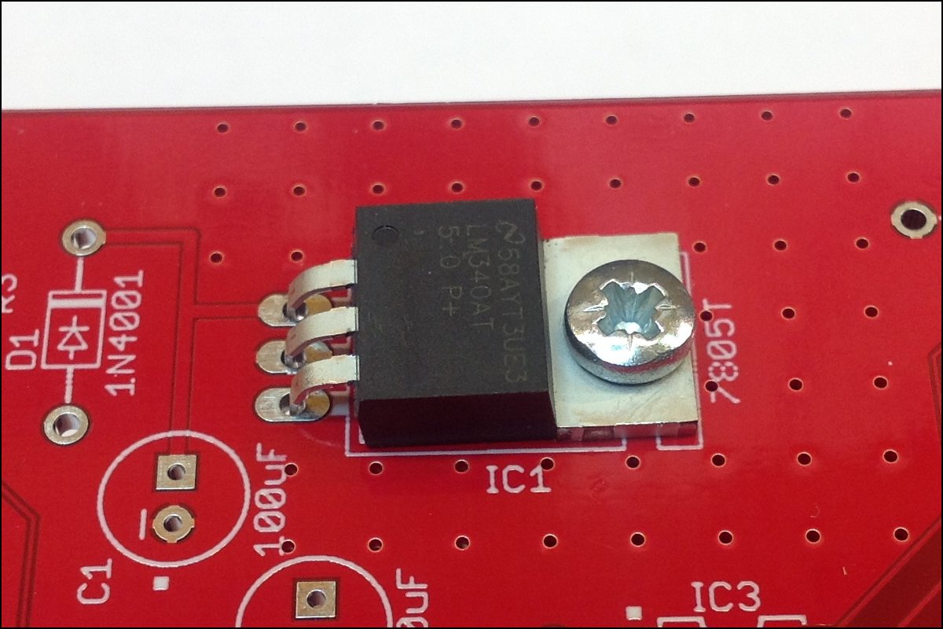
docs/source/Images/Hardware/Interface/Img_0578.jpg
