Simulators/simulator-type2/docs/source/Images/Hardware/Interface/Img_0580.jpg

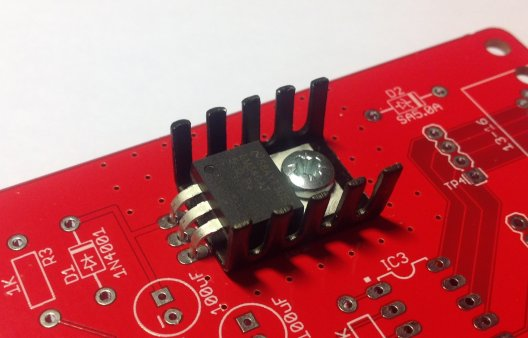
docs/source/Images/Hardware/Interface/Img_0580.jpg
