Simulators/simulator-type2/docs/source/Images/Hardware/Interface/Img_0594.jpg

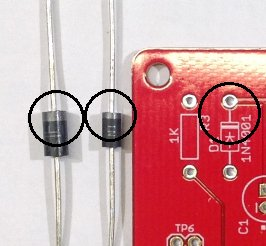
docs/source/Images/Hardware/Interface/Img_0594.jpg
