Simulators/simulator-type2/docs/source/Images/Hardware/Interface/IMG_0623.JPG

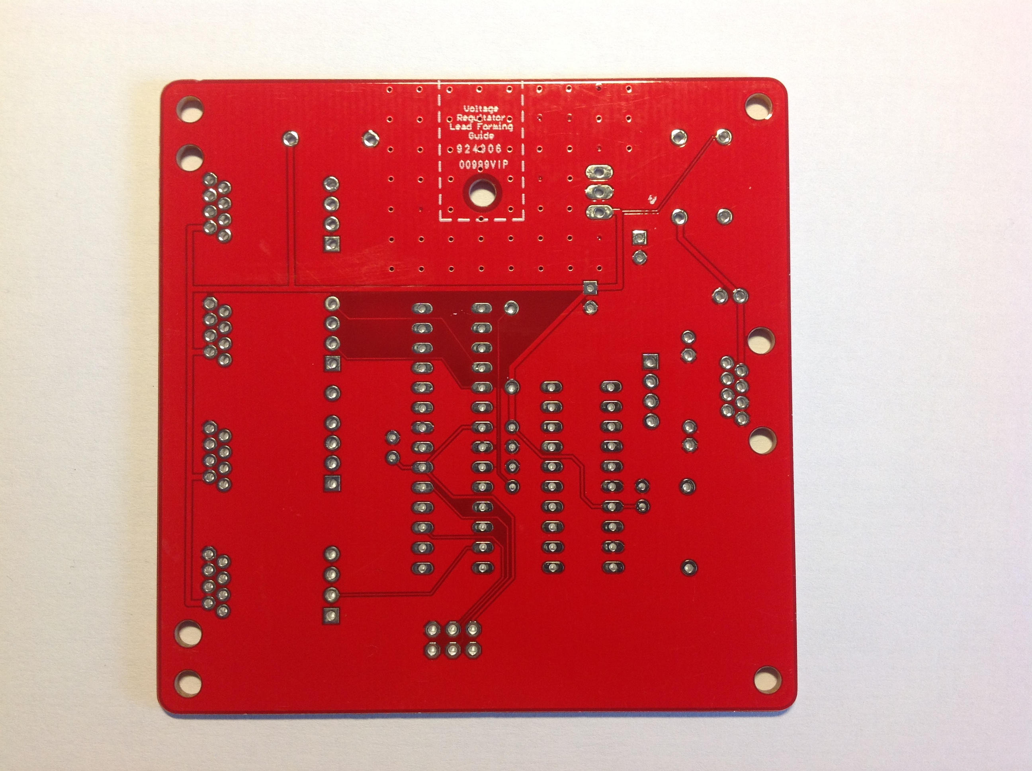
docs/source/Images/Hardware/Interface/IMG_0623.JPG
