Simulators/simulator-type2/docs/source/Images/Hardware/Interface/RevE_Board.jpg

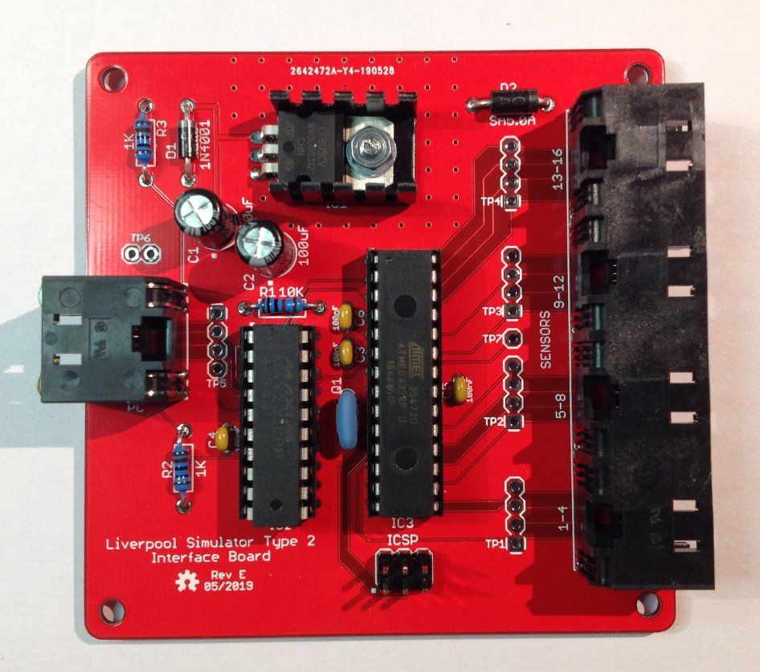
docs/source/Images/Hardware/Interface/RevE_Board.jpg
