Simulators/simulator-type2/docs/source/Images/Hardware/Interface/RevE_Board_angle.jpg

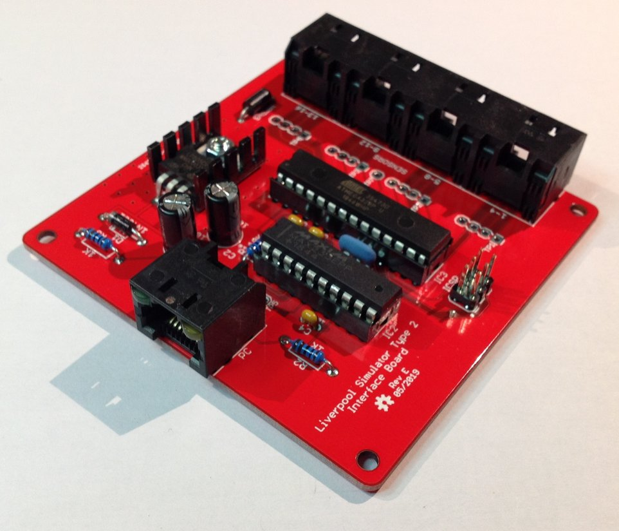
docs/source/Images/Hardware/Interface/RevE_Board_angle.jpg
