Simulators/simulator-type2/docs/source/Images/Hardware/MR Sensor/B101A620-43C4-4632-AFDD-0E2FFDCBED01.jpg

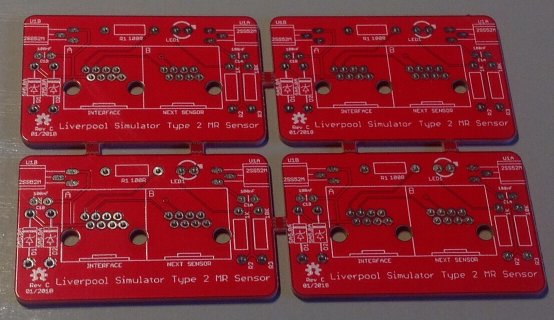
docs/source/Images/Hardware/MR Sensor/B101A620-43C4-4632-AFDD-0E2FFDCBED01.jpg
