Simulators/simulator-type2/docs/source/Images/Hardware/MR Sensor/Img_0437.jpg

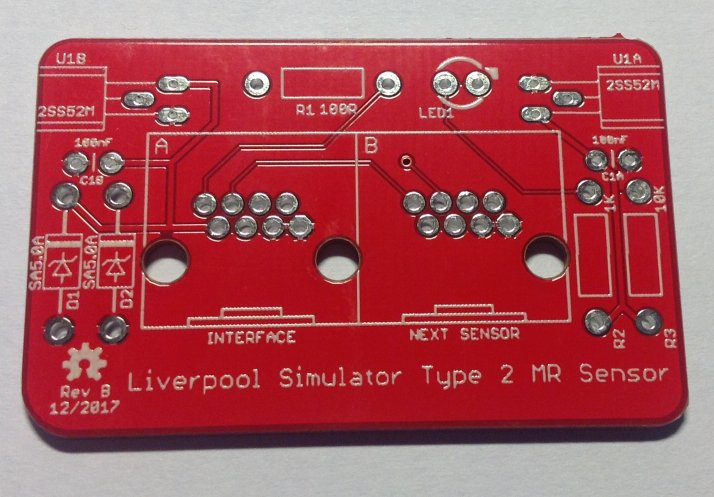
docs/source/Images/Hardware/MR Sensor/Img_0437.jpg
