Simulators/simulator-type2/docs/source/Images/Hardware/MR Sensor/Img_0439.jpg

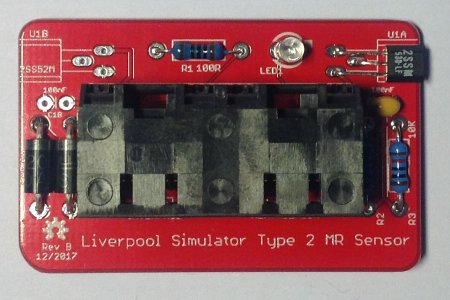
docs/source/Images/Hardware/MR Sensor/Img_0439.jpg
