Simulators/simulator-type2/docs/source/Images/Hardware/MR Sensor/IMG_0568.jpg

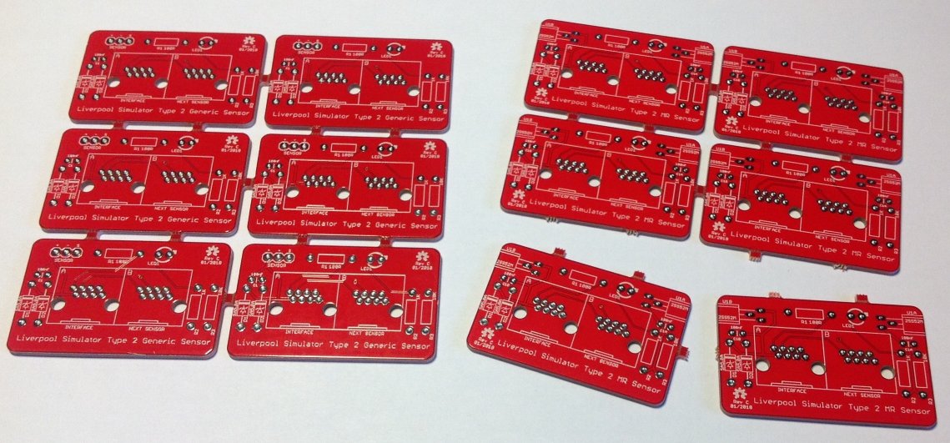
docs/source/Images/Hardware/MR Sensor/IMG_0568.jpg
