Simulators/simulator-type2/docs/source/Images/Hardware/MR Sensor/IMG_2073.jpeg

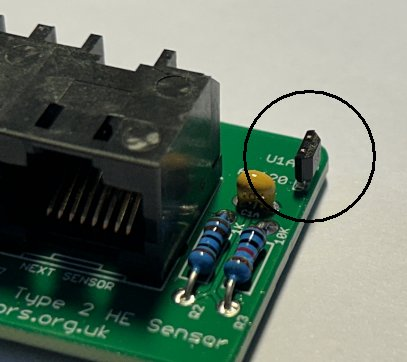
docs/source/Images/Hardware/MR Sensor/IMG_2073.jpeg
