Simulators/simulator-type2/docs/source/Images/Hardware/MR Sensor/Img_2161.jpg

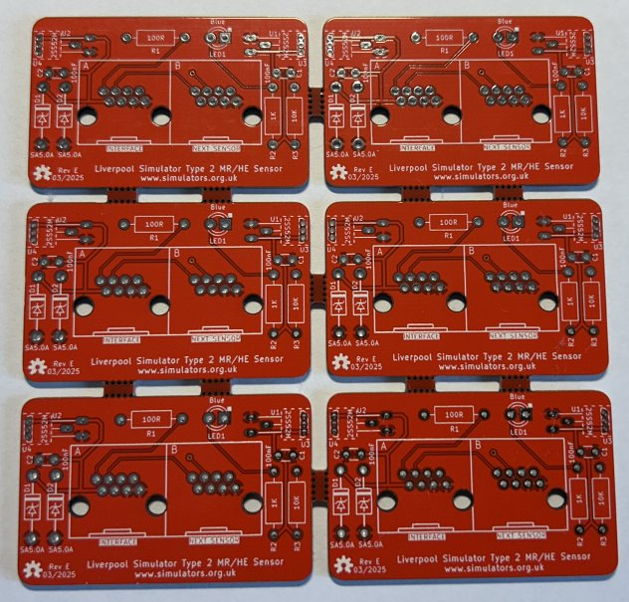
docs/source/Images/Hardware/MR Sensor/Img_2161.jpg
