Simulators/simulator-type2/docs/source/Images/Hardware/MR Sensor/Img_2164.jpg

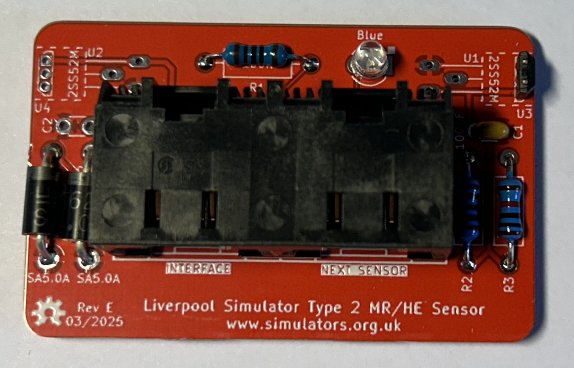
docs/source/Images/Hardware/MR Sensor/Img_2164.jpg
