Simulators/simulator-type2/docs/source/Images/Hardware/Power/Img_0654.jpg

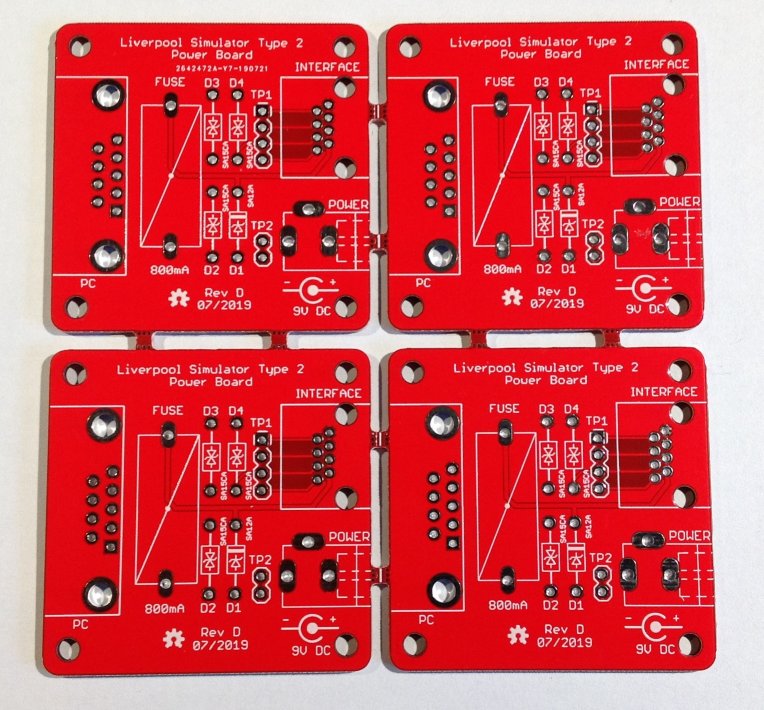
docs/source/Images/Hardware/Power/Img_0654.jpg
