Simulators/simulator-type2/docs/source/Images/Hardware/Prototype 2/Img_0404.jpg

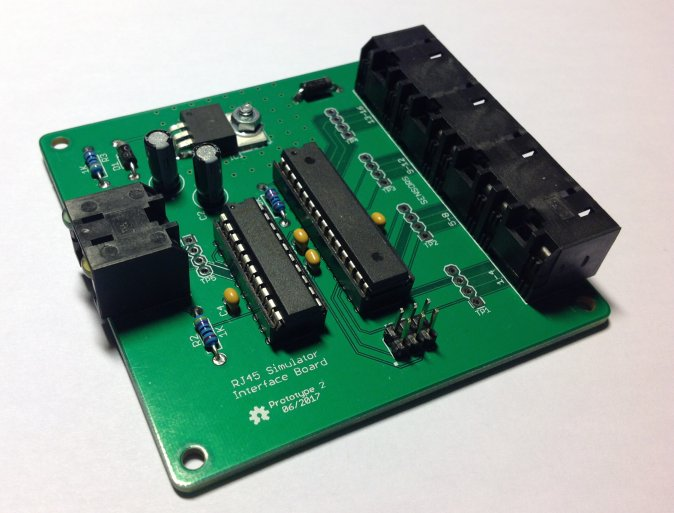
docs/source/Images/Hardware/Prototype 2/Img_0404.jpg
