Simulators/simulator-type2/docs/source/Images/Hardware/Prototype 2/LH_RH.jpg

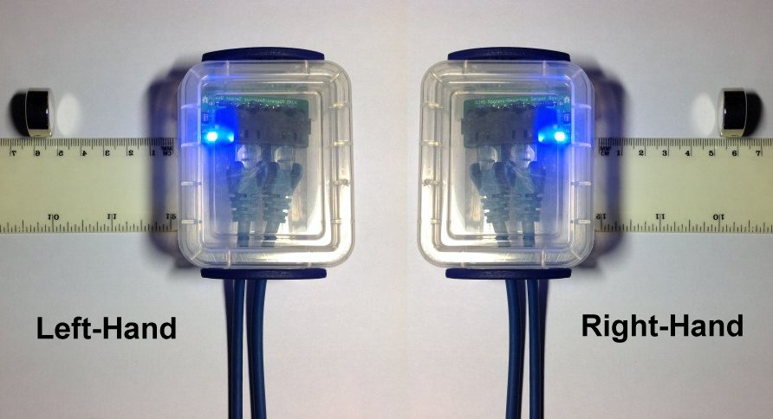
docs/source/Images/Hardware/Prototype 2/LH_RH.jpg
