Simulators/simulator-type2/docs/source/Images/Hardware/Second PC/Img_0621.jpg

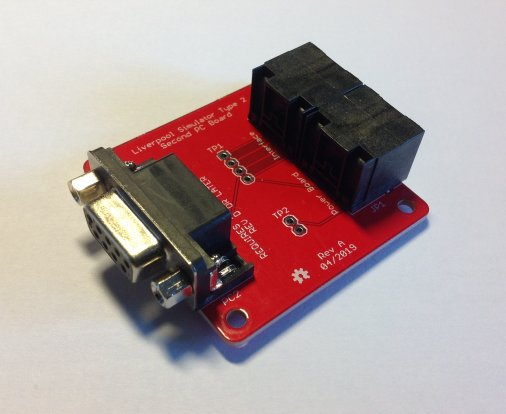
docs/source/Images/Hardware/Second PC/Img_0621.jpg
