Simulators/simulator-type2/docs/source/Images/Hardware/Second PC/Img_0655.jpg

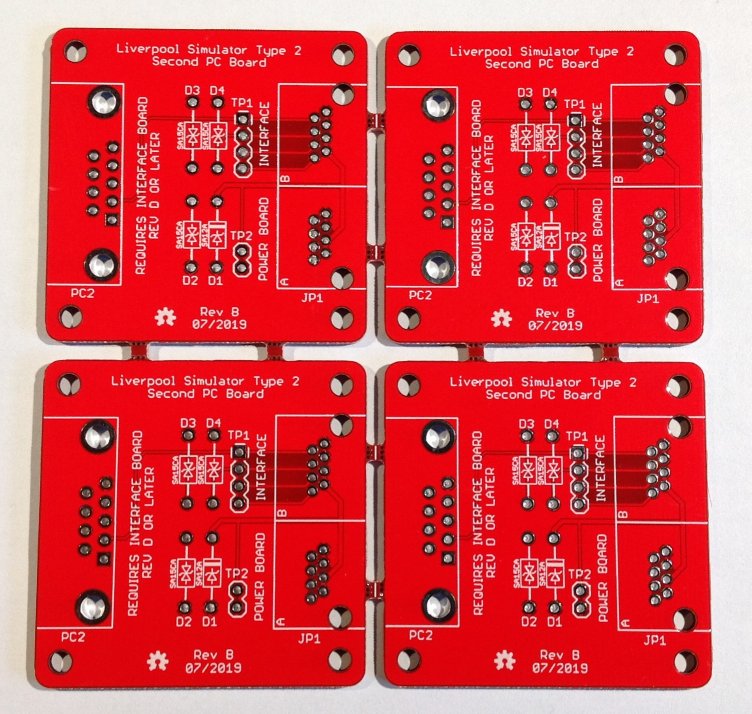
docs/source/Images/Hardware/Second PC/Img_0655.jpg
