Simulators/simulator-type2/docs/source/Images/Hardware/Second PC/IMG_0656.JPG

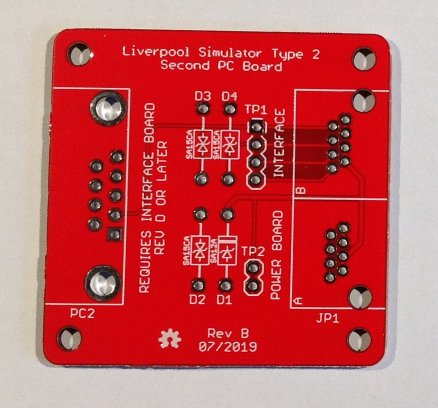
docs/source/Images/Hardware/Second PC/IMG_0656.JPG
