Simulators/simulator-type2/docs/source/Images/Hardware/T1-T2 Adapter/Img_0768.jpeg

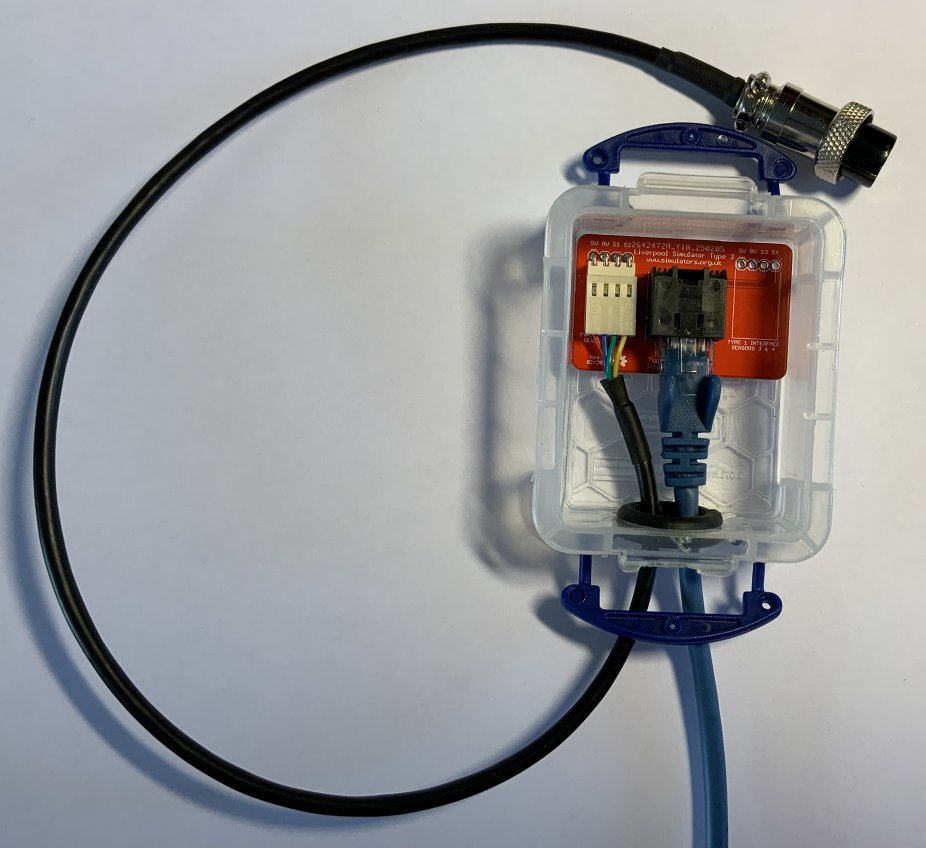
docs/source/Images/Hardware/T1-T2 Adapter/Img_0768.jpeg
