Simulators/simulator-type2/docs/source/Images/Hardware/T1-T2 Adapter/IMG_0769.JPEG

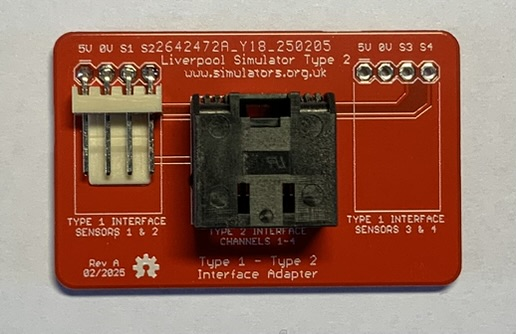
docs/source/Images/Hardware/T1-T2 Adapter/IMG_0769.JPEG
