Simulators/simulator-type2/docs/source/Images/PCBs/Basic Splitter/SimulatorT2BasicSerialSplitterRevD_Expander_Schematic.png

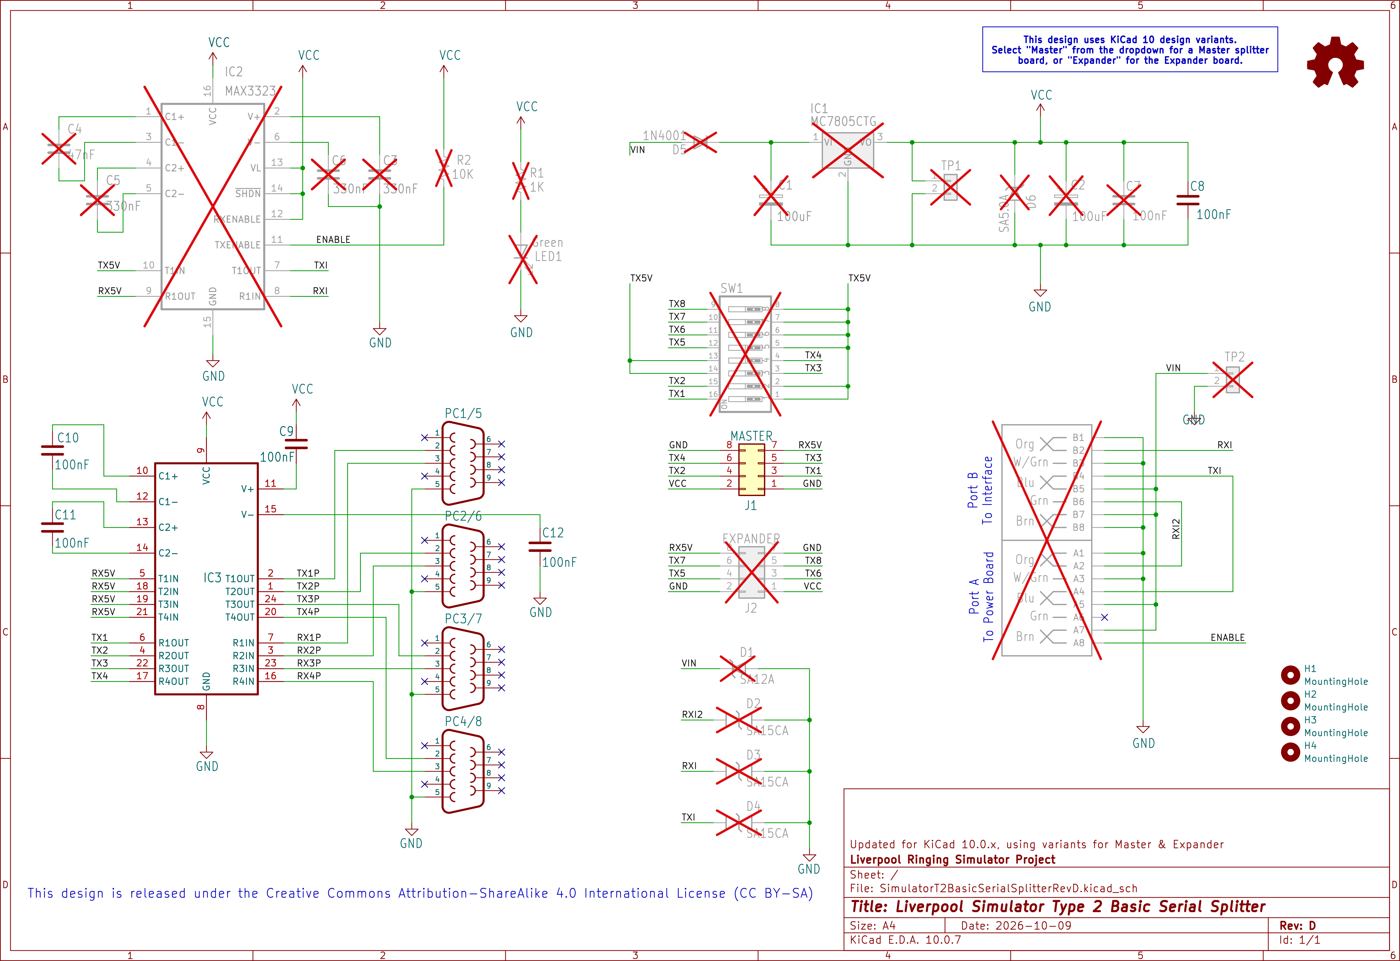
docs/source/Images/PCBs/Basic Splitter/SimulatorT2BasicSerialSplitterRevD_Expander_Schematic.png
