Simulators/simulator-type2/docs/source/Images/PCBs/Generic Sensor/SimulatorT2GenericSensorRevD-Edge_Cuts.png

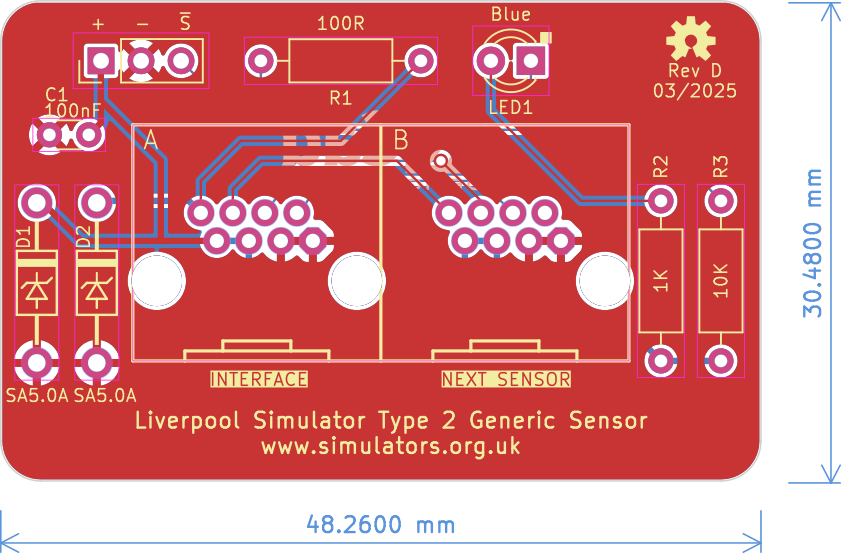
docs/source/Images/PCBs/Generic Sensor/SimulatorT2GenericSensorRevD-Edge_Cuts.png
