Simulators/simulator-type2/docs/source/Images/PCBs/Generic Sensor/SimulatorT2GenericSensorRevD_Schematic.png

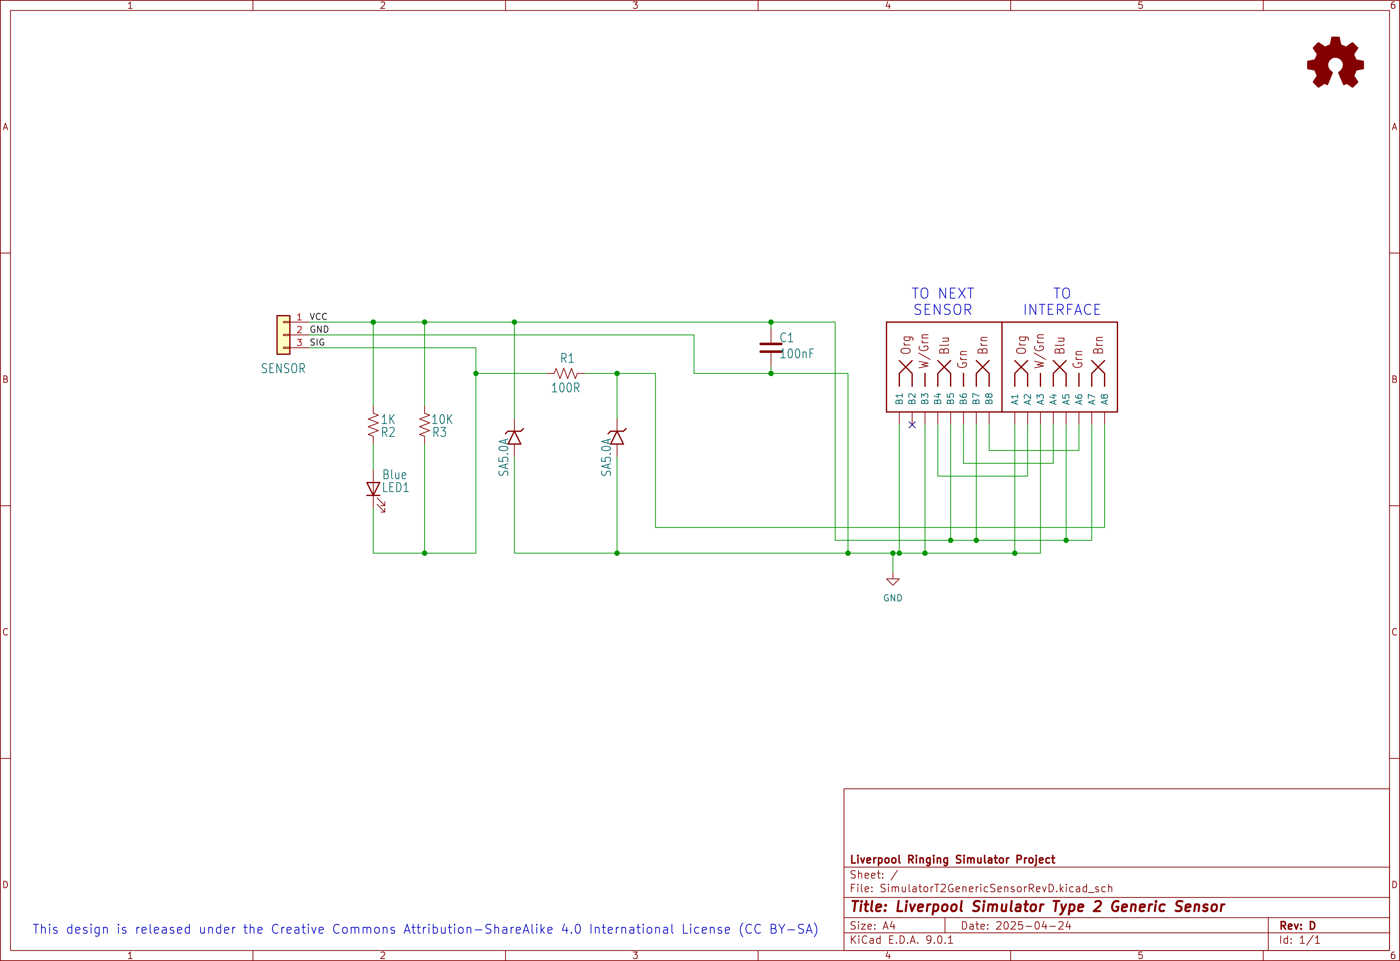
docs/source/Images/PCBs/Generic Sensor/SimulatorT2GenericSensorRevD_Schematic.png
