Simulators/simulator-type2/docs/source/Images/PCBs/Interface/SimulatorT2InterfaceRevF-Edge_Cuts.png

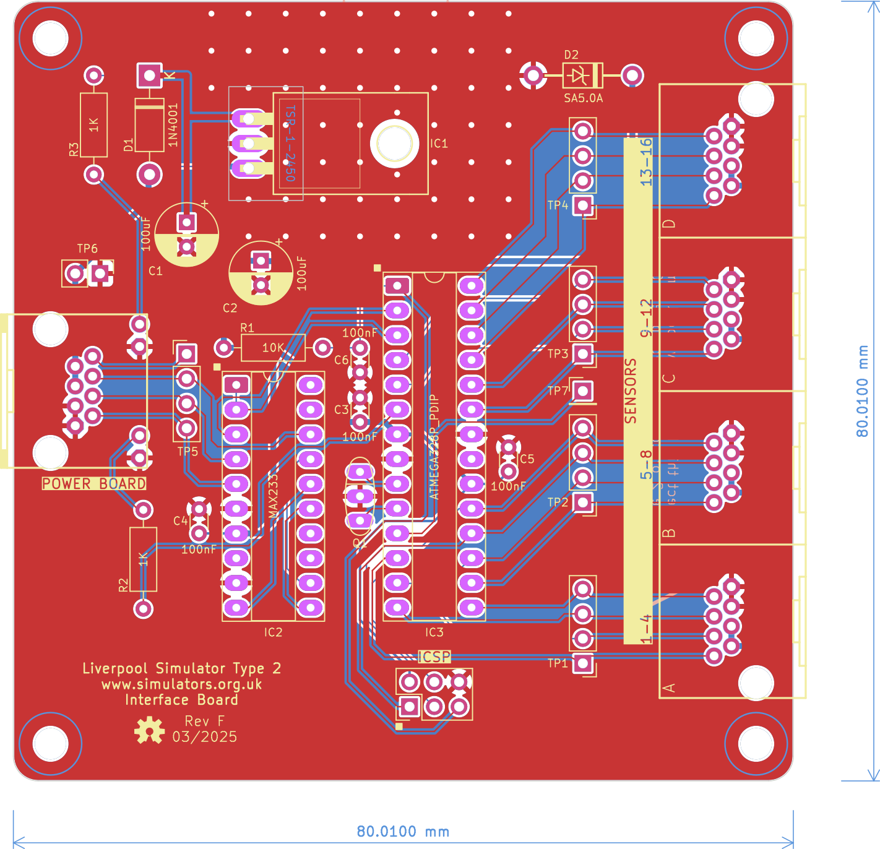
docs/source/Images/PCBs/Interface/SimulatorT2InterfaceRevF-Edge_Cuts.png
