Simulators/simulator-type2/docs/source/Images/PCBs/Interface/SimulatorT2InterfaceRevF_Schematic.png

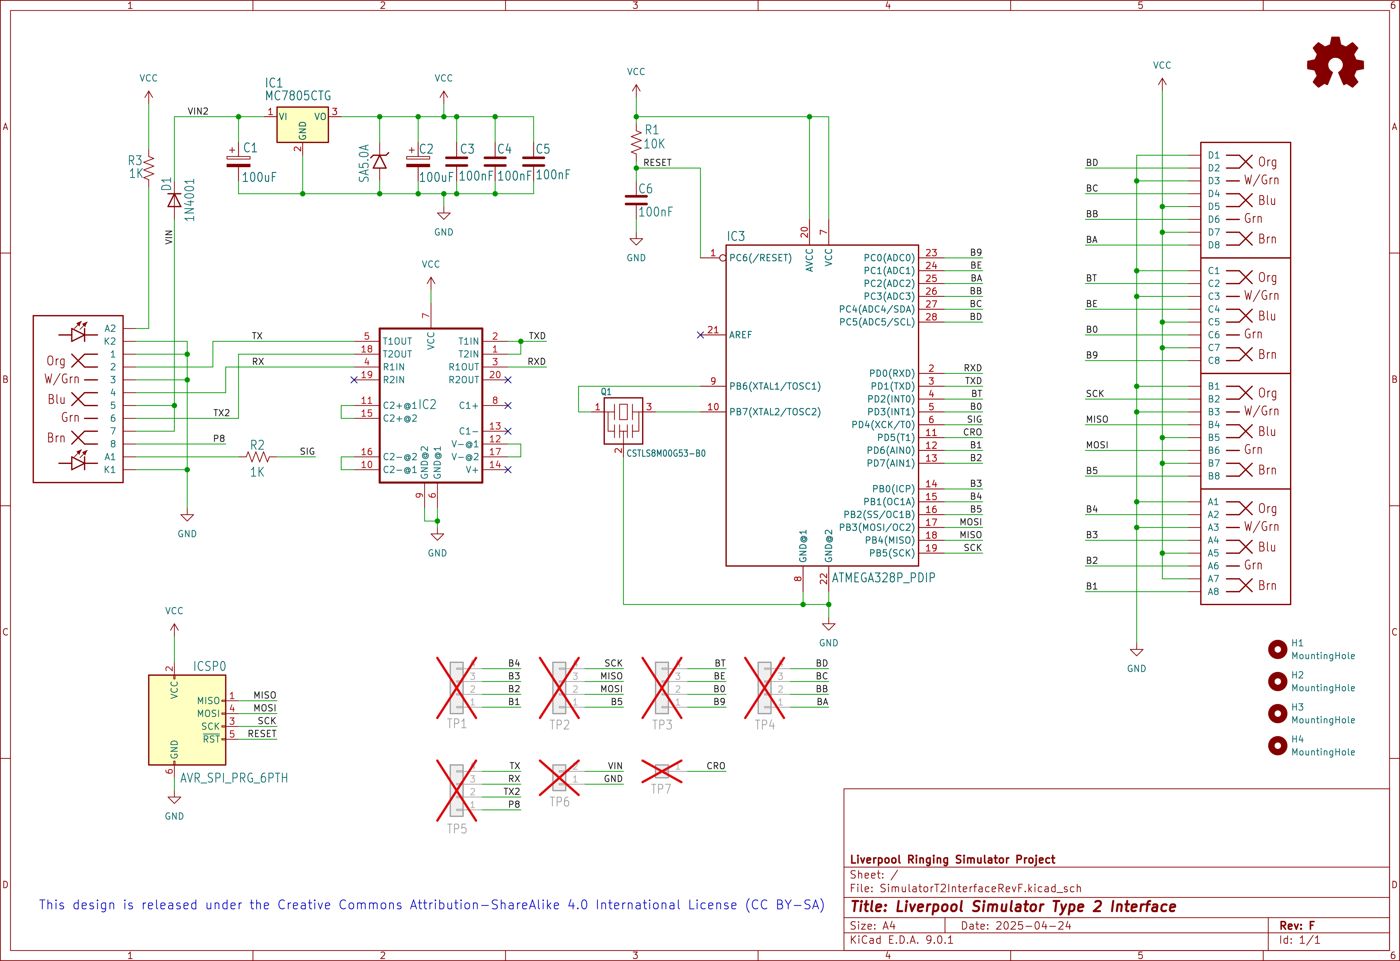
docs/source/Images/PCBs/Interface/SimulatorT2InterfaceRevF_Schematic.png
