Simulators/simulator-type2/docs/source/Images/PCBs/MR Sensor/SimulatorT2MRSensorRevE-Edge_Cuts.png

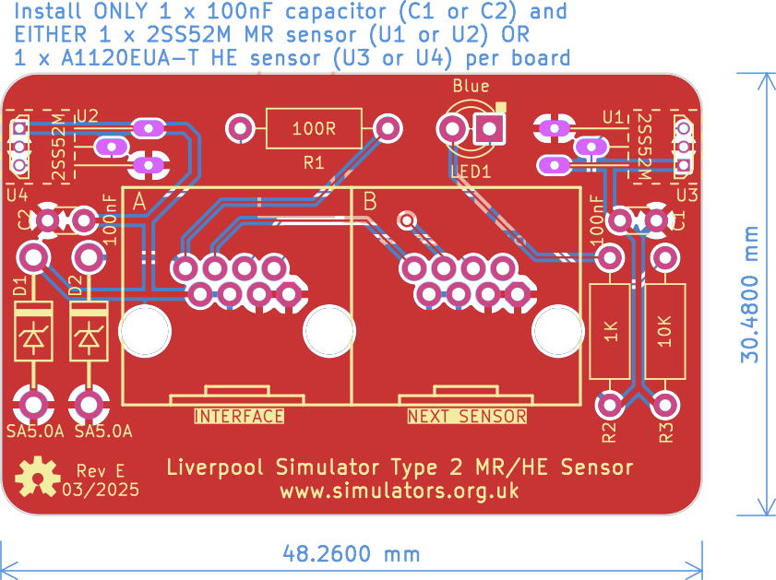
docs/source/Images/PCBs/MR Sensor/SimulatorT2MRSensorRevE-Edge_Cuts.png
