Simulators/simulator-type2/docs/source/Images/PCBs/MR Sensor/SimulatorT2MRSensorRevE_Schematic.png

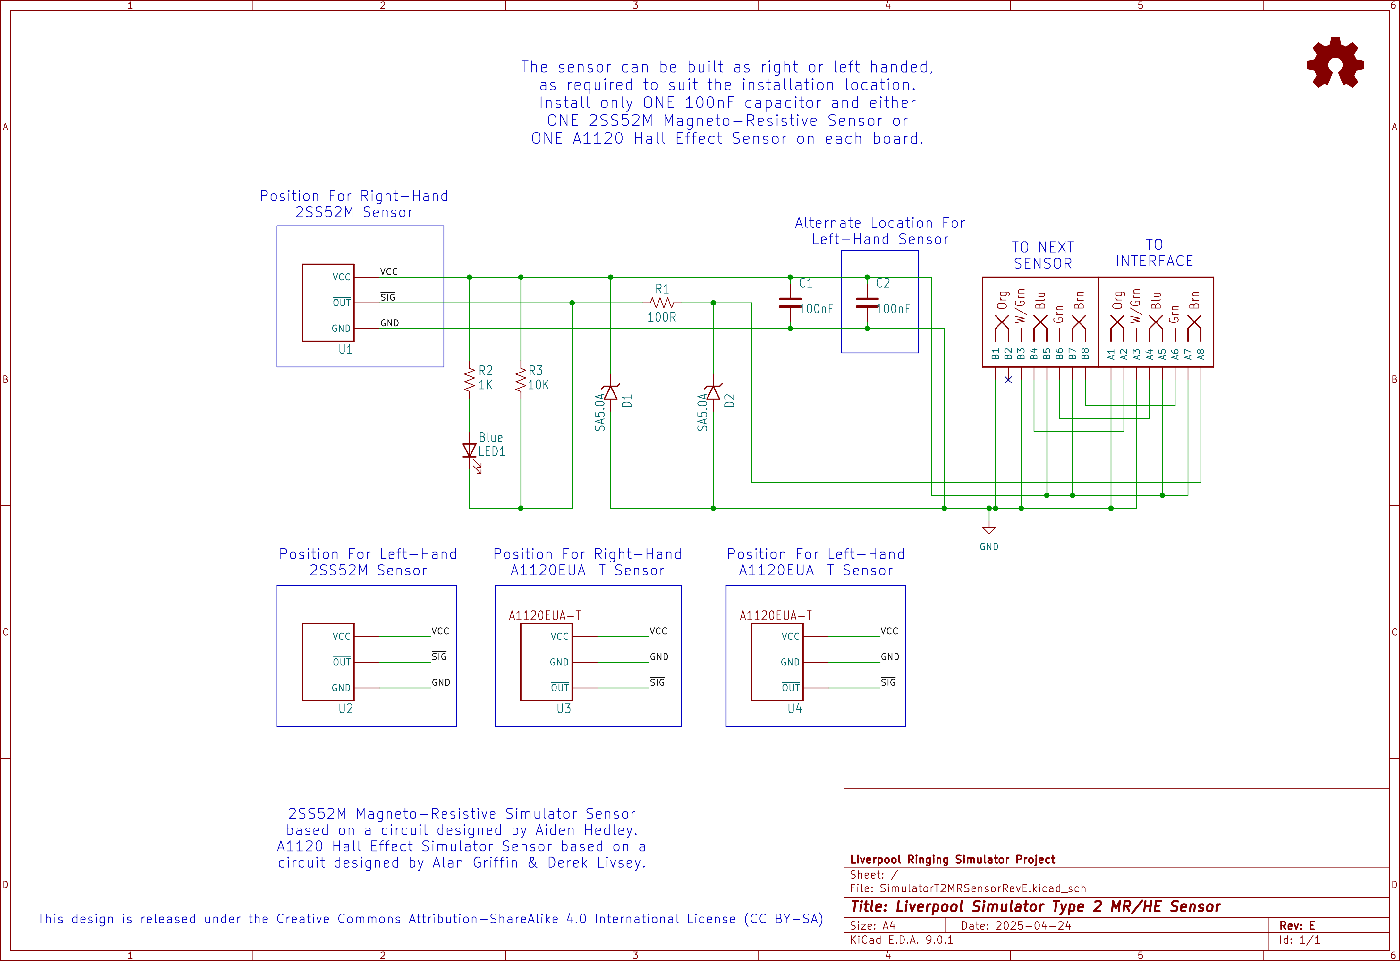
docs/source/Images/PCBs/MR Sensor/SimulatorT2MRSensorRevE_Schematic.png
