Simulators/simulator-type2/docs/source/Images/PCBs/Power/SimulatorT2PowerRevE-Edge_Cuts.png

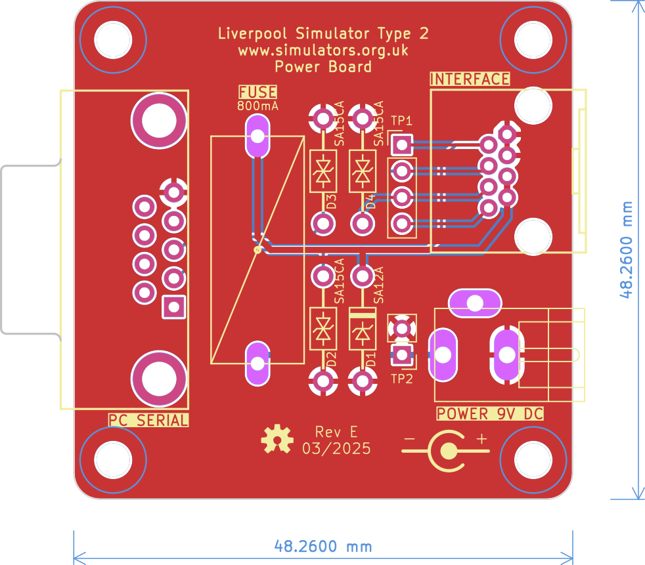
docs/source/Images/PCBs/Power/SimulatorT2PowerRevE-Edge_Cuts.png
