Simulators/simulator-type2/docs/source/Images/PCBs/Power/SimulatorT2PowerRevE_Schematic.png

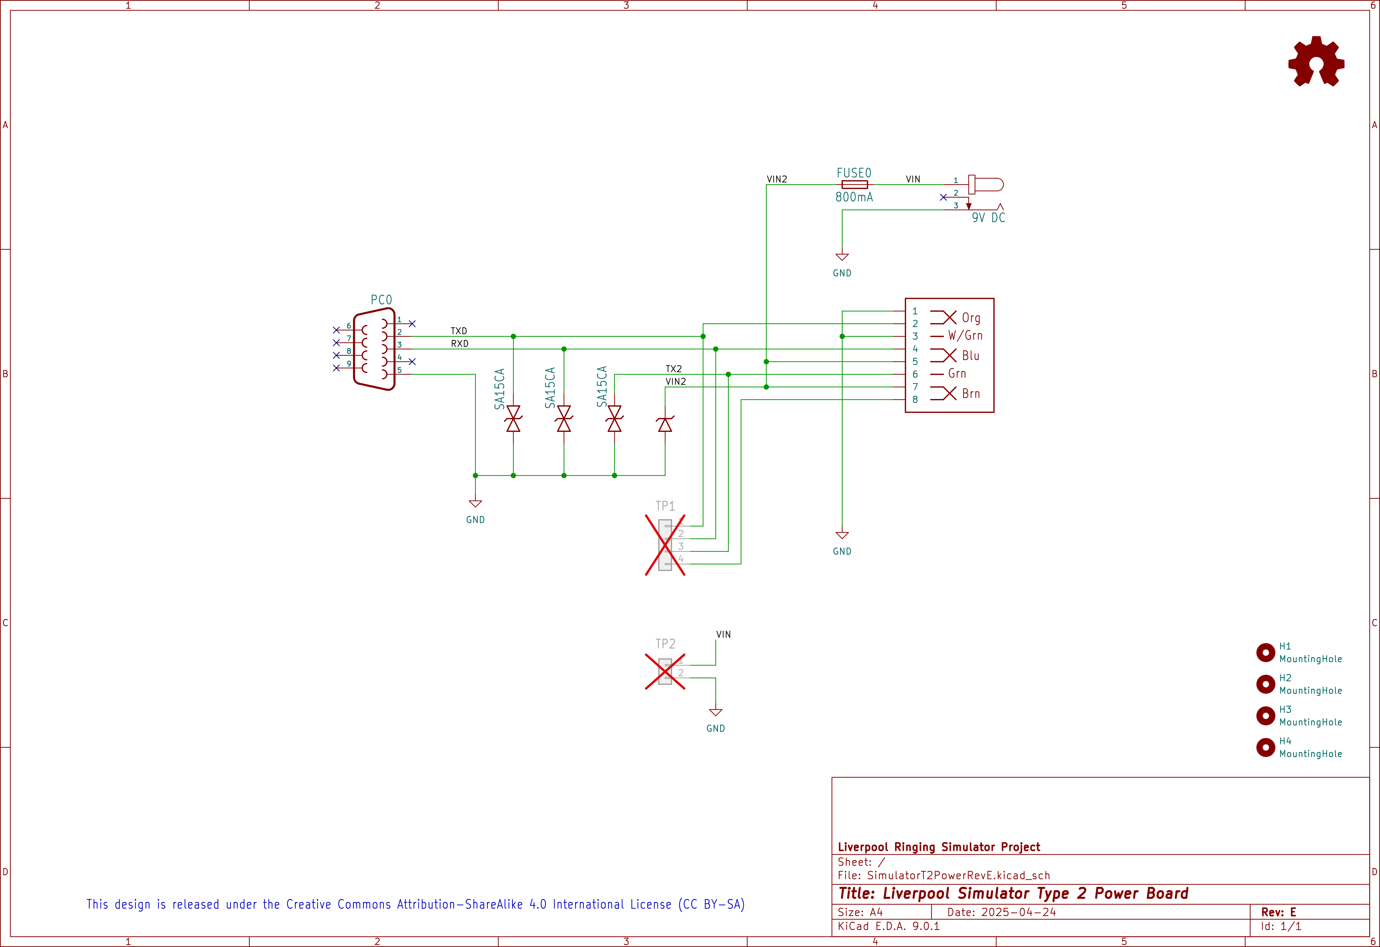
docs/source/Images/PCBs/Power/SimulatorT2PowerRevE_Schematic.png
