Simulators/simulator-type2/docs/source/Images/PCBs/Second PC/SimulatorT2SecondPCRevC-Edge_Cuts.png

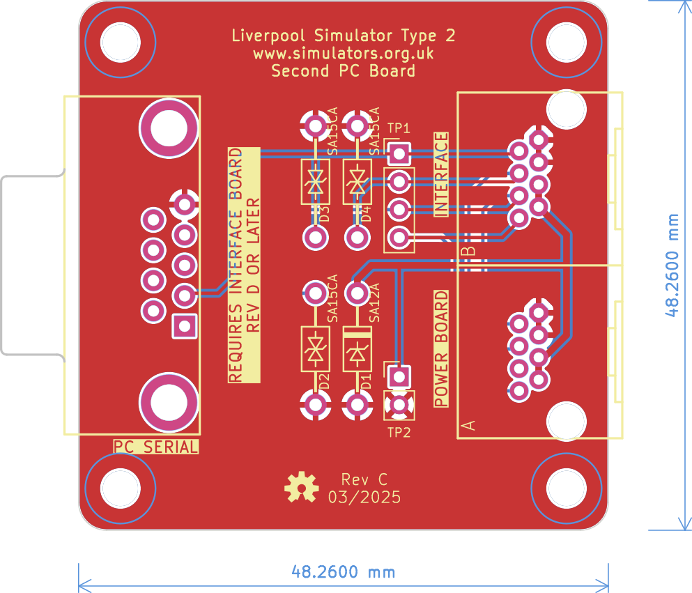
docs/source/Images/PCBs/Second PC/SimulatorT2SecondPCRevC-Edge_Cuts.png
