Simulators/simulator-type2/docs/source/Images/PCBs/Second PC/SimulatorT2SecondPCRevC_Schematic.png

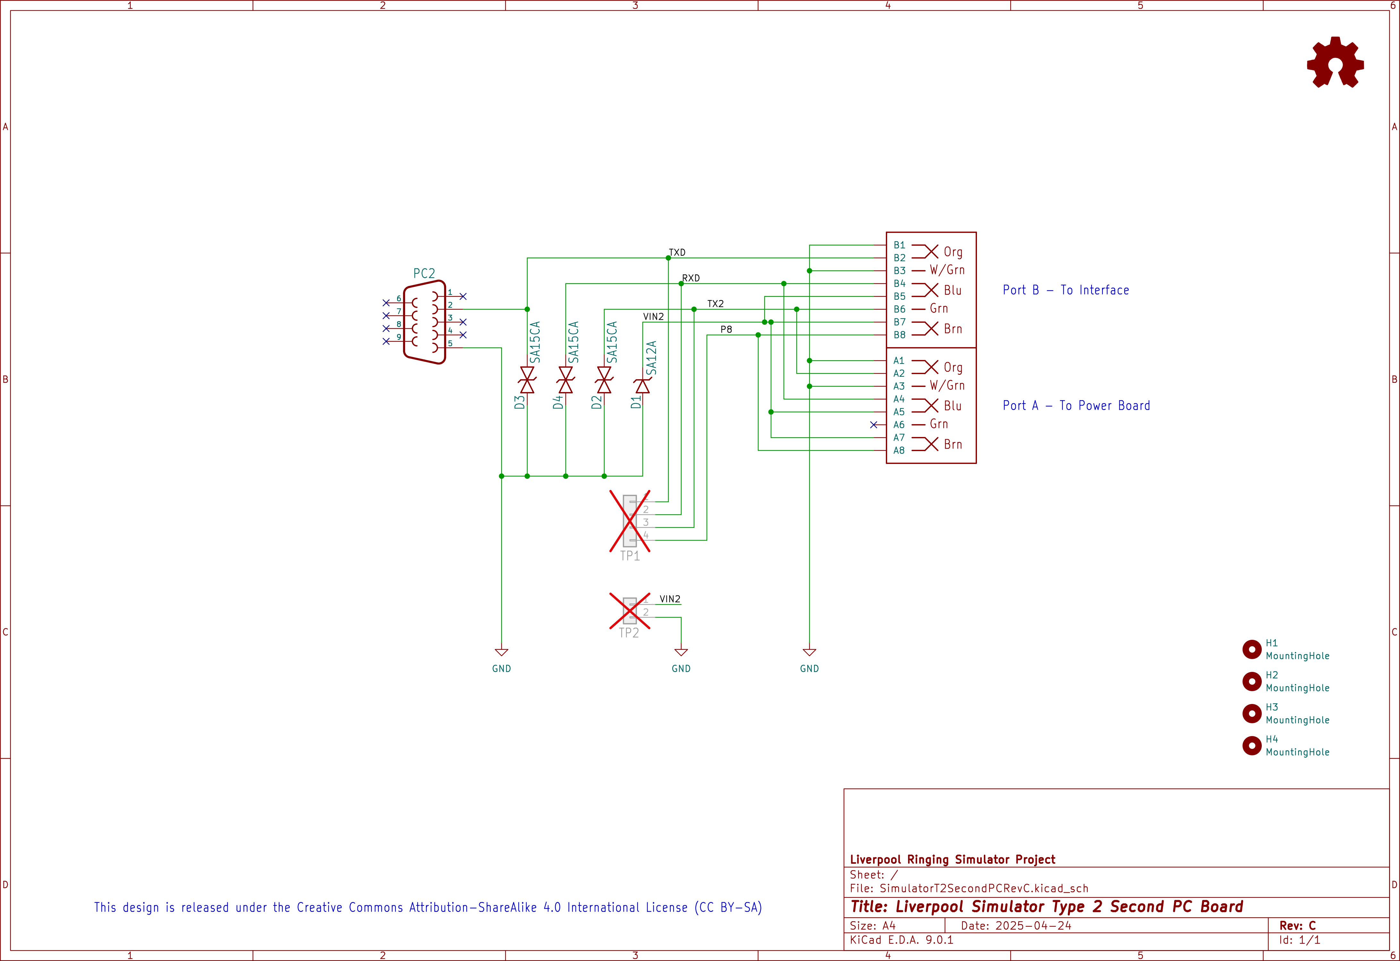
docs/source/Images/PCBs/Second PC/SimulatorT2SecondPCRevC_Schematic.png
