Simulators/simulator-type2/docs/source/Images/PCBs/T1-T2 Adapter/SimulatorT1T2AdapterRevC_Schematic.png

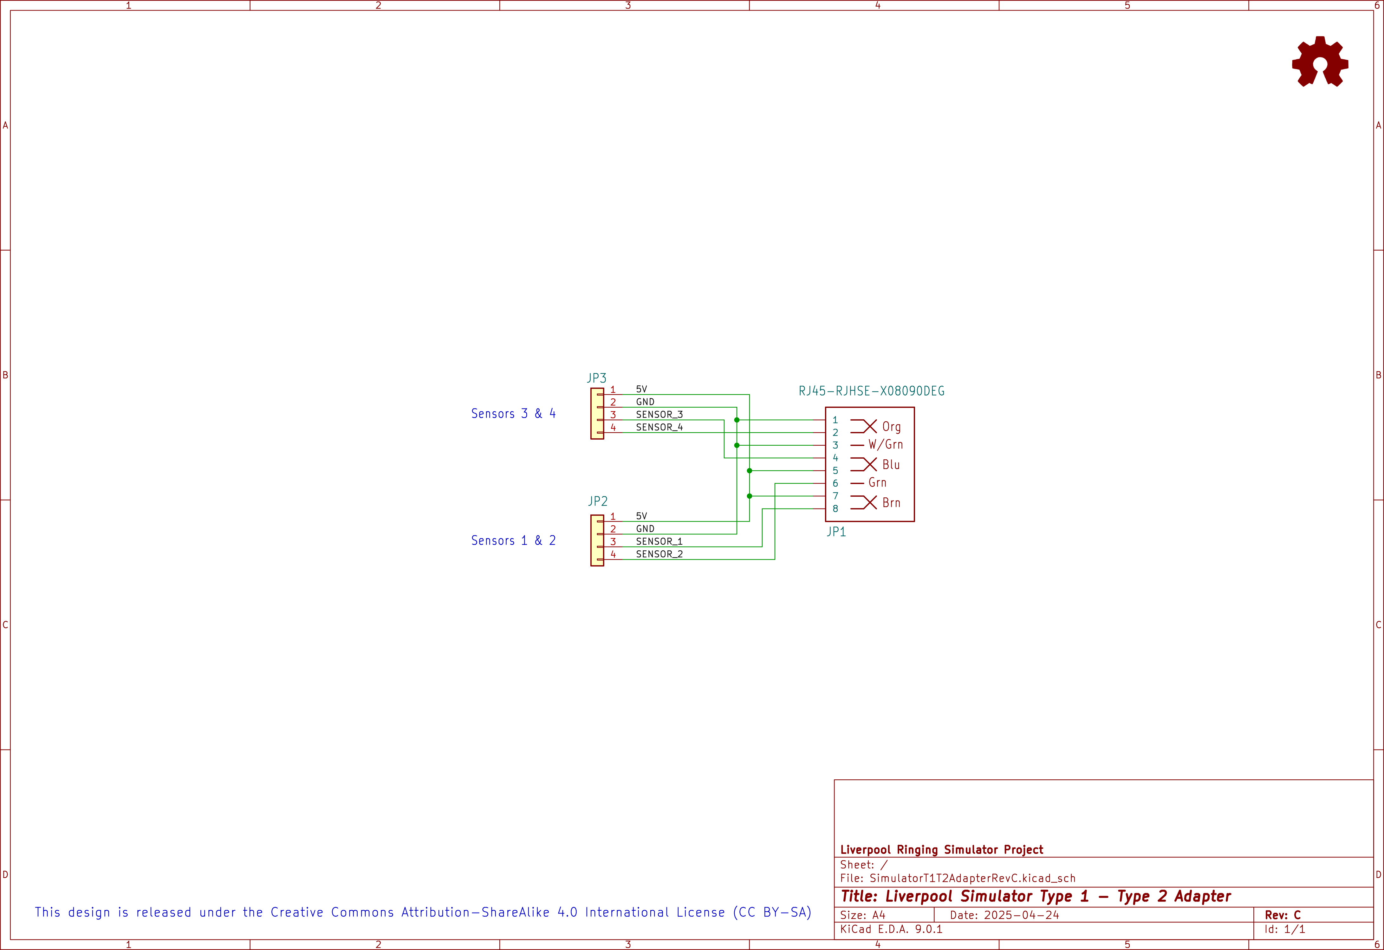
docs/source/Images/PCBs/T1-T2 Adapter/SimulatorT1T2AdapterRevC_Schematic.png
