Simulators/simulator-type2/docs/source/Screenshots/Abel 10.3.2/Abel 14b.png

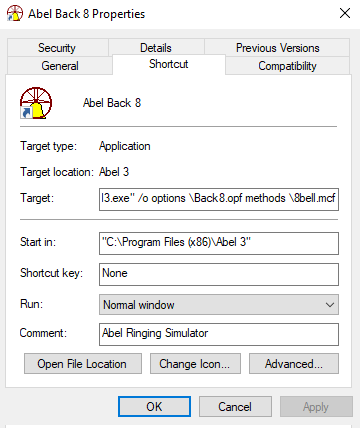
docs/source/Screenshots/Abel 10.3.2/Abel 14b.png
