Simulators/simulator-type2/docs/source/Screenshots/Arduino 1.6.12/09 - T2SimBoardSelect.png

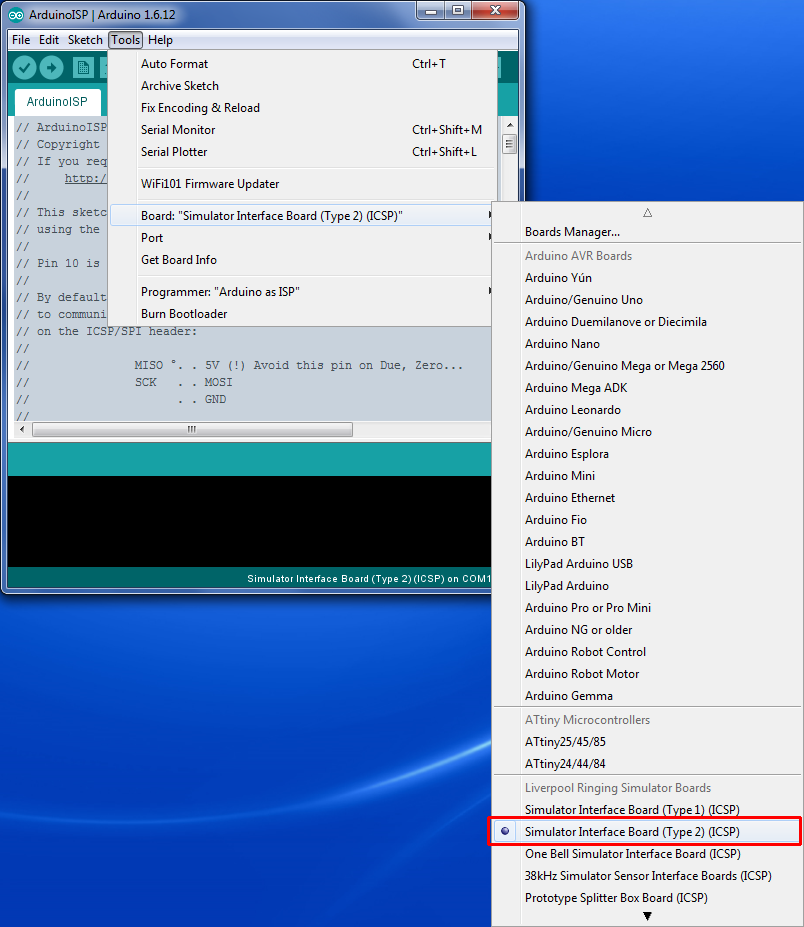
docs/source/Screenshots/Arduino 1.6.12/09 - T2SimBoardSelect.png
