Simulators/simulator-type2/docs/source/Screenshots/Arduino 1.6.12/T2UploadComplete.png

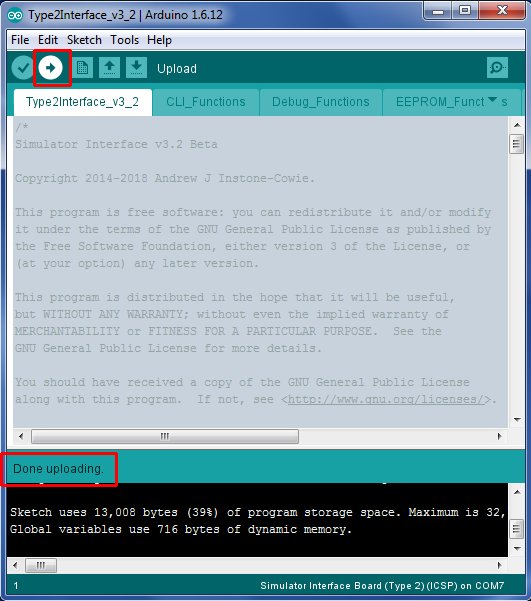
docs/source/Screenshots/Arduino 1.6.12/T2UploadComplete.png
