Simulators/simulator-type2/docs/source/Screenshots/Beltower 2017/BT9.png

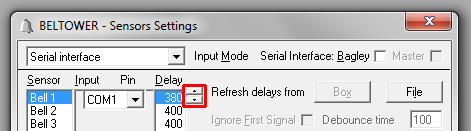
docs/source/Screenshots/Beltower 2017/BT9.png
