Simulators/simulator-type2/docs/source/Screenshots/Beltower 2017/BT10.png

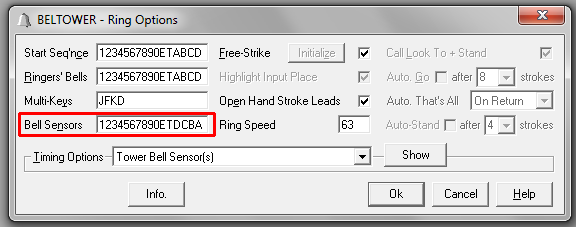
docs/source/Screenshots/Beltower 2017/BT10.png
