Simulators/simulator-type2/docs/source/Screenshots/Beltower 2017/BT 3.png

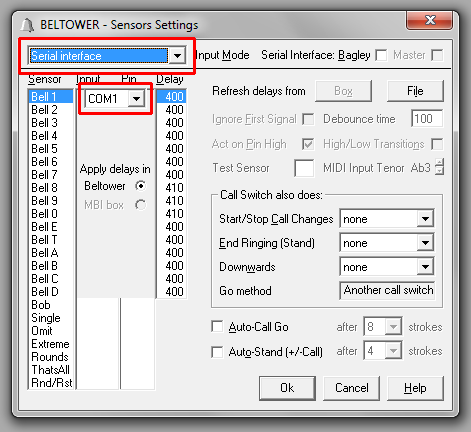
docs/source/Screenshots/Beltower 2017/BT 3.png
