Simulators/simulator-type2/docs/source/Screenshots/Beltower 2017/BT 5.png

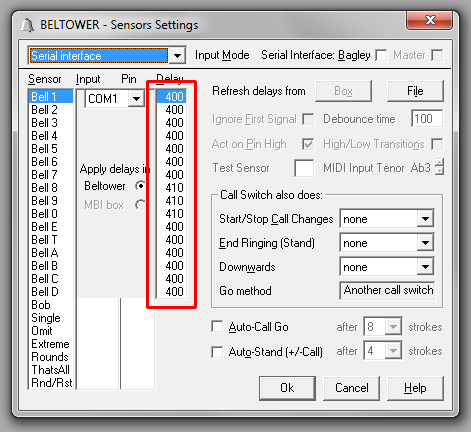
docs/source/Screenshots/Beltower 2017/BT 5.png
