Simulators/simulator-type2/docs/source/Screenshots/Firmware 3.3/2 - Putty Config21.png

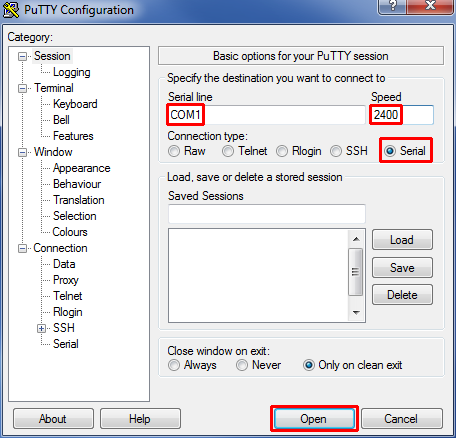
docs/source/Screenshots/Firmware 3.3/2 - Putty Config21.png
