Simulators/simulator-type2/docs/source/Screenshots/Firmware 3.3/4 - Help Screen21.png

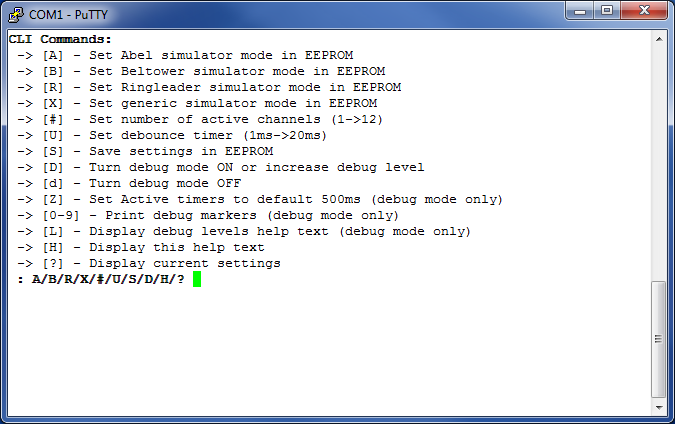
docs/source/Screenshots/Firmware 3.3/4 - Help Screen21.png
