Simulators/simulator-type2/docs/source/Screenshots/Firmware 3.3/6 - Active Channels21.png

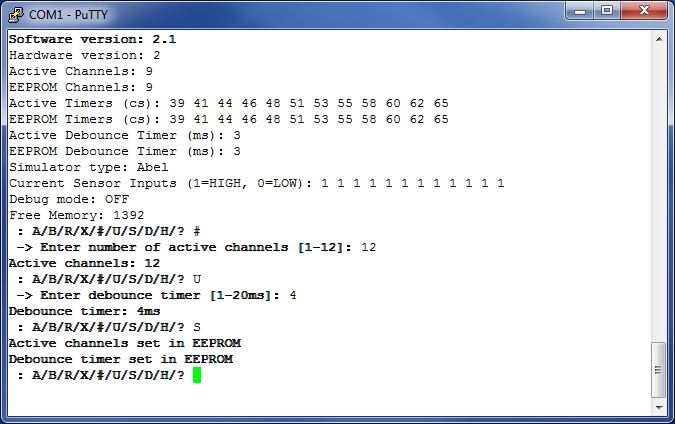
docs/source/Screenshots/Firmware 3.3/6 - Active Channels21.png
