Simulators/simulator-type2/docs/source/Screenshots/Firmware 3.3/10 - Arduino Tools21.png

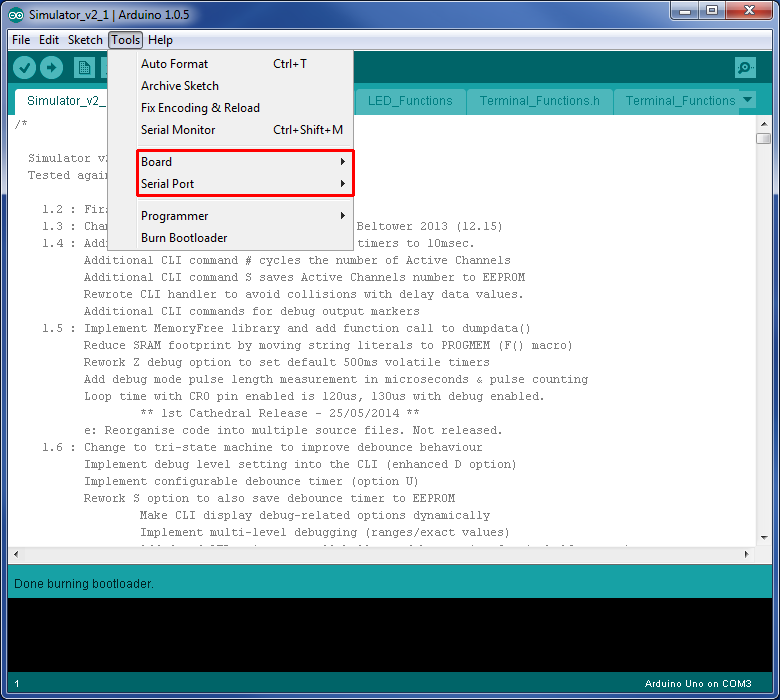
docs/source/Screenshots/Firmware 3.3/10 - Arduino Tools21.png
