Simulators/simulator-type2/docs/source/Screenshots/Firmware 3.3/11 - Arduino Upload Complete21.png

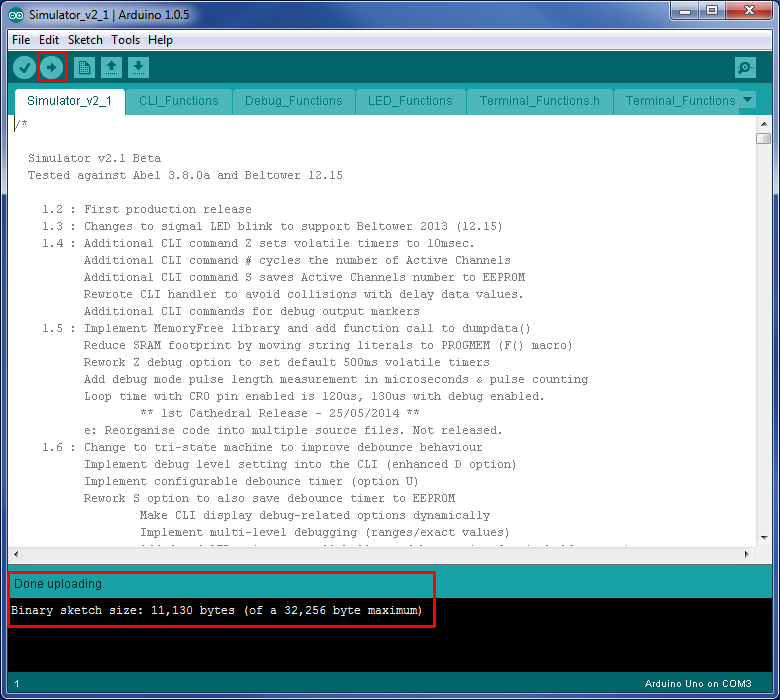
docs/source/Screenshots/Firmware 3.3/11 - Arduino Upload Complete21.png
