Simulators/simulator-type2/docs/source/Screenshots/Firmware 3.3/12 - External Bells21.png

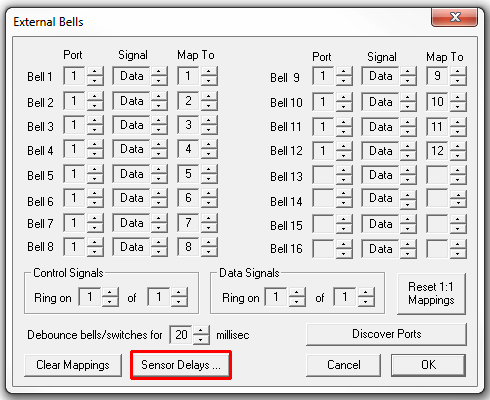
docs/source/Screenshots/Firmware 3.3/12 - External Bells21.png
