Simulators/simulator-type2/docs/source/Screenshots/Firmware 3.3/13 - External Delays21.png

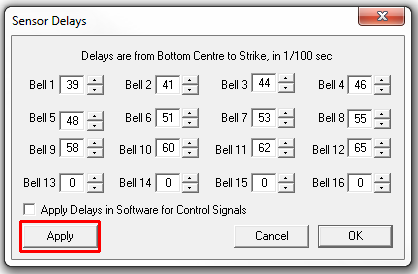
docs/source/Screenshots/Firmware 3.3/13 - External Delays21.png
