Simulators/simulator-type2/docs/source/Screenshots/Firmware 3.3/14 - Beltower Sensors21.png

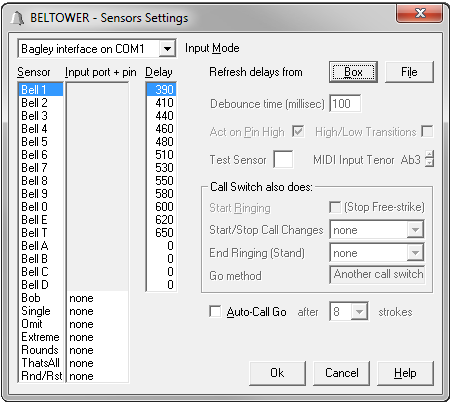
docs/source/Screenshots/Firmware 3.3/14 - Beltower Sensors21.png
