Simulators/simulator-type2/docs/source/Screenshots/Firmware 3.3/15 - Ringing Options 12 21.png

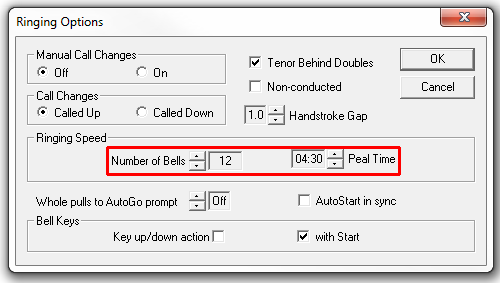
docs/source/Screenshots/Firmware 3.3/15 - Ringing Options 12 21.png
