Simulators/simulator-type2/docs/source/Screenshots/Firmware 3.3/18 - Back 8 Mapping21.png

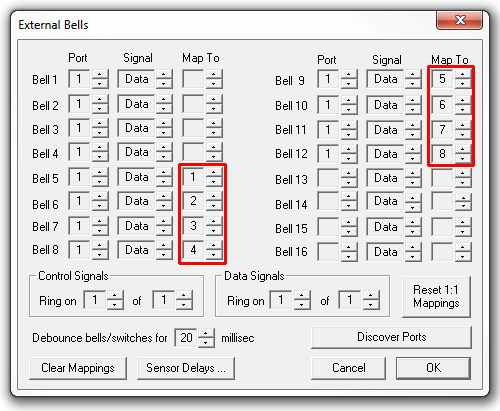
docs/source/Screenshots/Firmware 3.3/18 - Back 8 Mapping21.png
