Simulators/simulator-type2/docs/source/Screenshots/Firmware 3.3/Settings 2.png

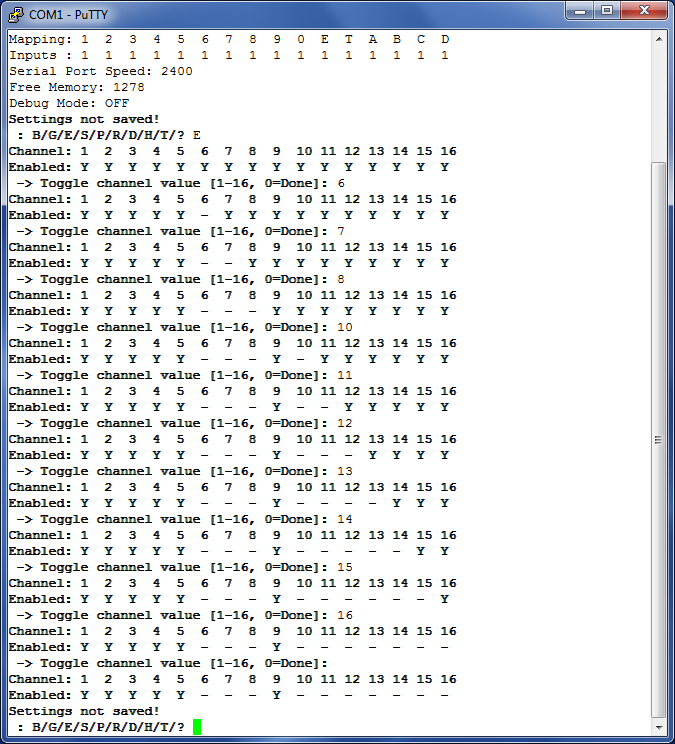
docs/source/Screenshots/Firmware 3.3/Settings 2.png
