Simulators/simulator-type2/docs/source/Screenshots/JLCPCB/JLCPCB1.png

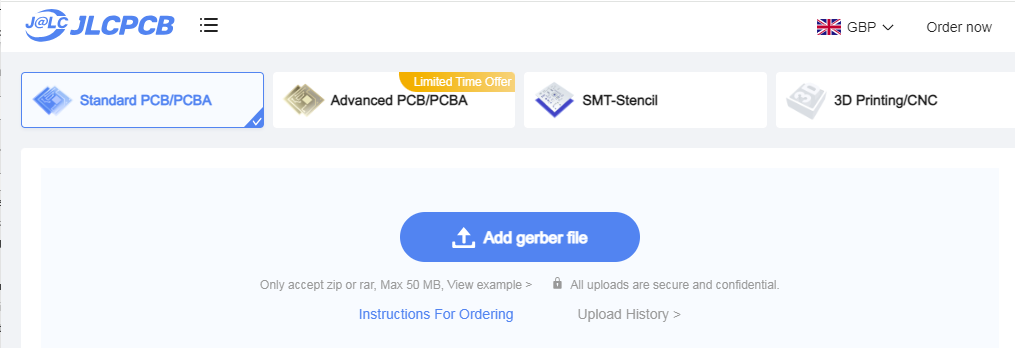
docs/source/Screenshots/JLCPCB/JLCPCB1.png
