Simulators/simulator-type2/docs/source/Screenshots/JLCPCB/JLCPCB2.png

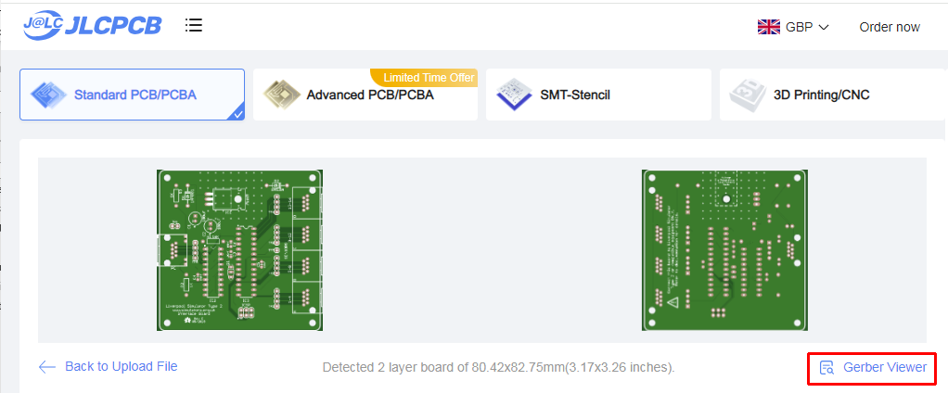
docs/source/Screenshots/JLCPCB/JLCPCB2.png
