Simulators/simulator-type2/docs/source/Screenshots/JLCPCB/JLCPCB3.png

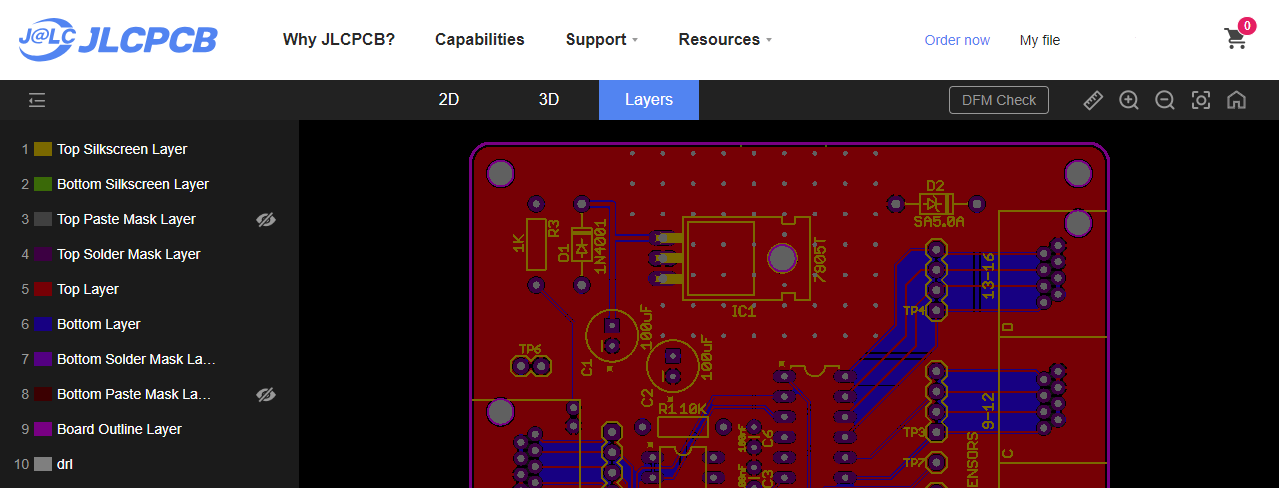
docs/source/Screenshots/JLCPCB/JLCPCB3.png
