Simulators/simulator-type2/docs/source/Screenshots/JLCPCB/JLCPCB4.png

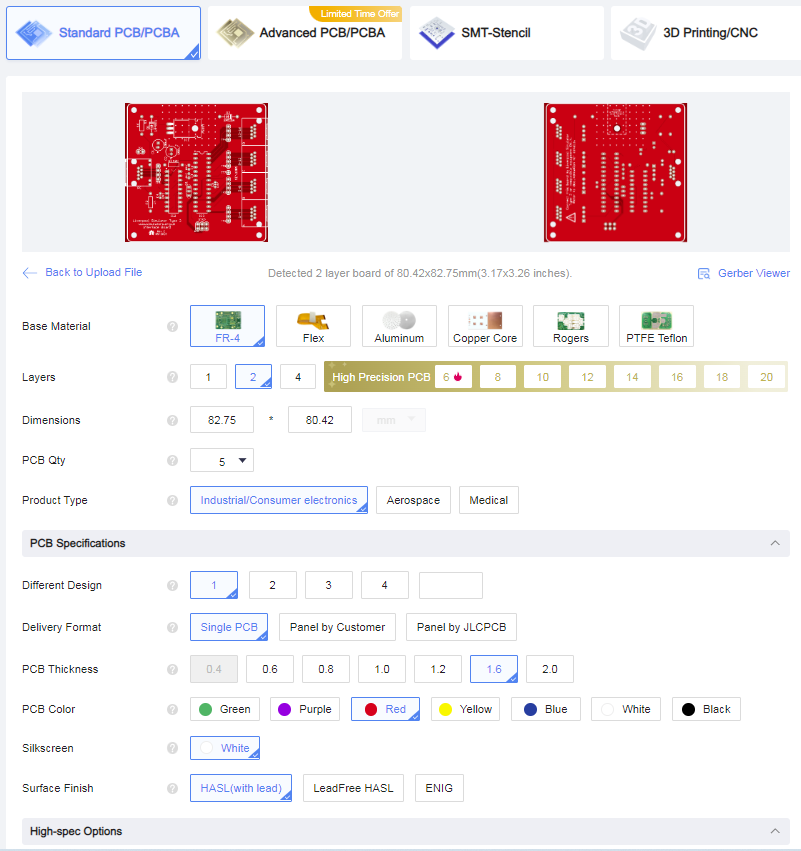
docs/source/Screenshots/JLCPCB/JLCPCB4.png
