Simulators/simulator-type2/docs/source/Screenshots/SeeedStudio/SeeedAddGerber.png

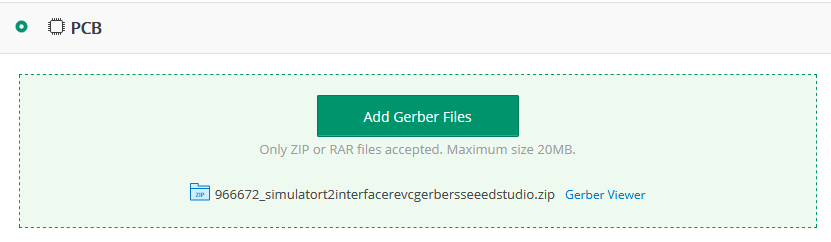
docs/source/Screenshots/SeeedStudio/SeeedAddGerber.png
