Simulators/simulator-type2/docs/source/Screenshots/SeeedStudio/SeeedForm_Annotated.png

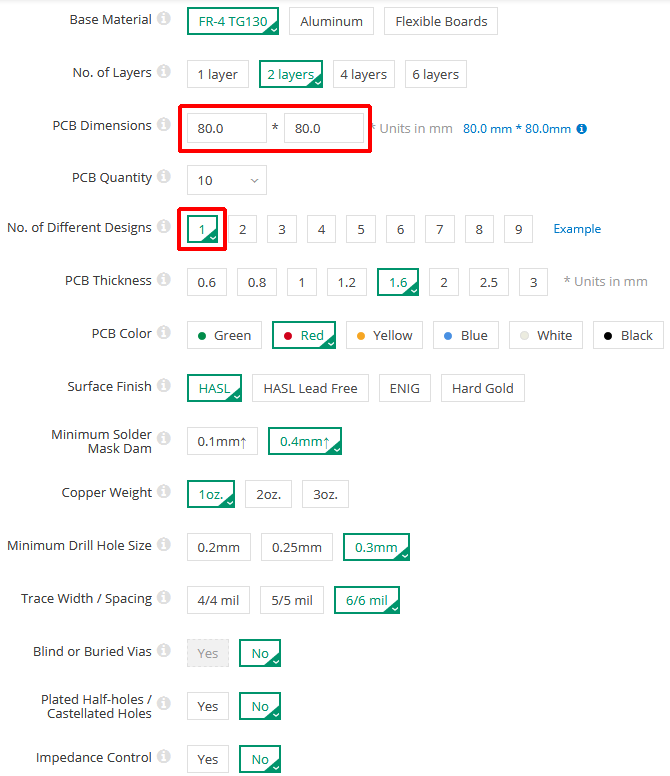
docs/source/Screenshots/SeeedStudio/SeeedForm_Annotated.png
