Simulators/simulator-type2/docs/source/Screenshots/SeeedStudio/SeeedViewGerber.png

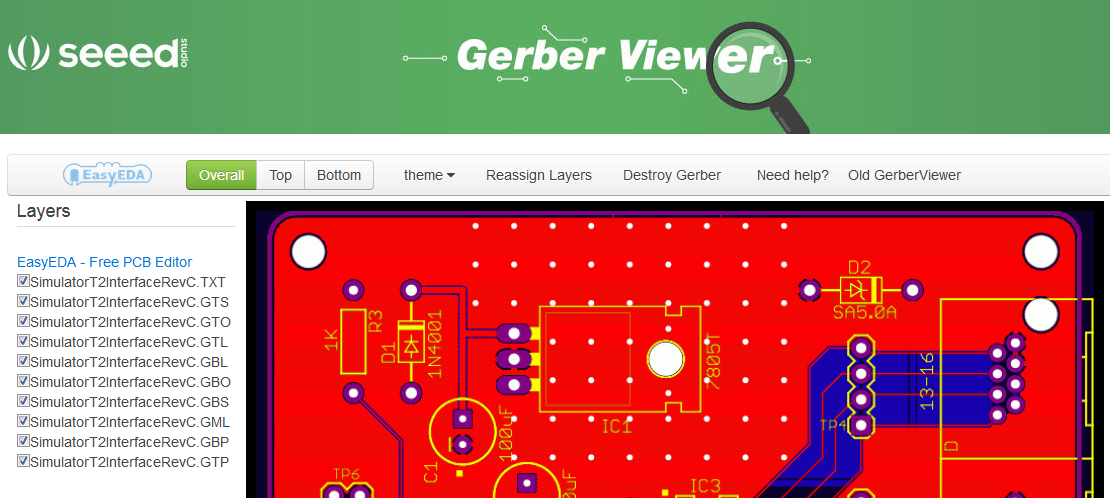
docs/source/Screenshots/SeeedStudio/SeeedViewGerber.png
