Simulators/simulator-type2/docs/source/Screenshots/Virtual Belfry 3.10/VB2.png

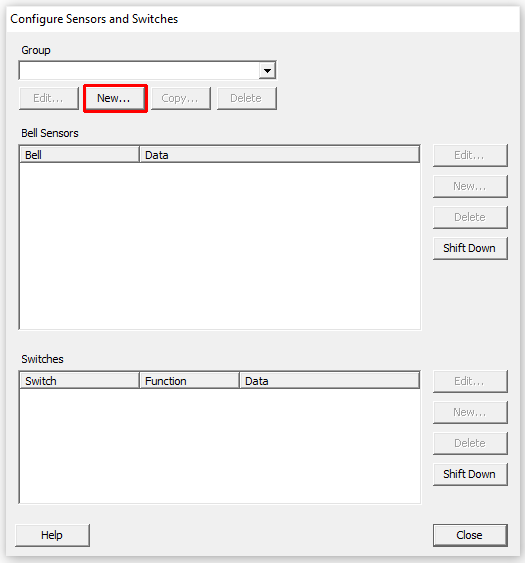
docs/source/Screenshots/Virtual Belfry 3.10/VB2.png
