Simulators/simulator-type2/docs/source/Screenshots/Virtual Belfry 3.10/VB11.png

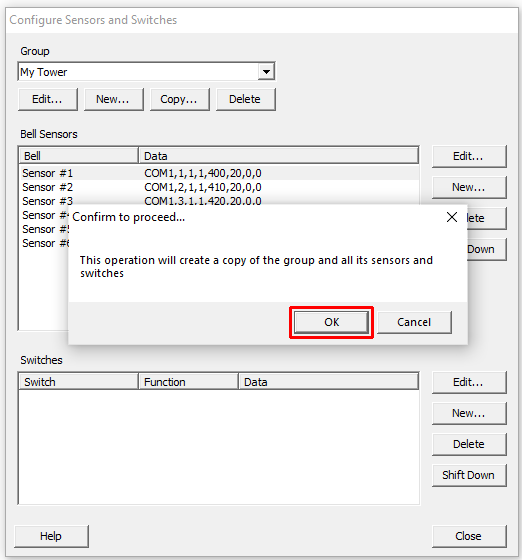
docs/source/Screenshots/Virtual Belfry 3.10/VB11.png
