Simulators/simulator-type2/docs/source/Images/Hardware/Interface/RevE_Parts.jpg

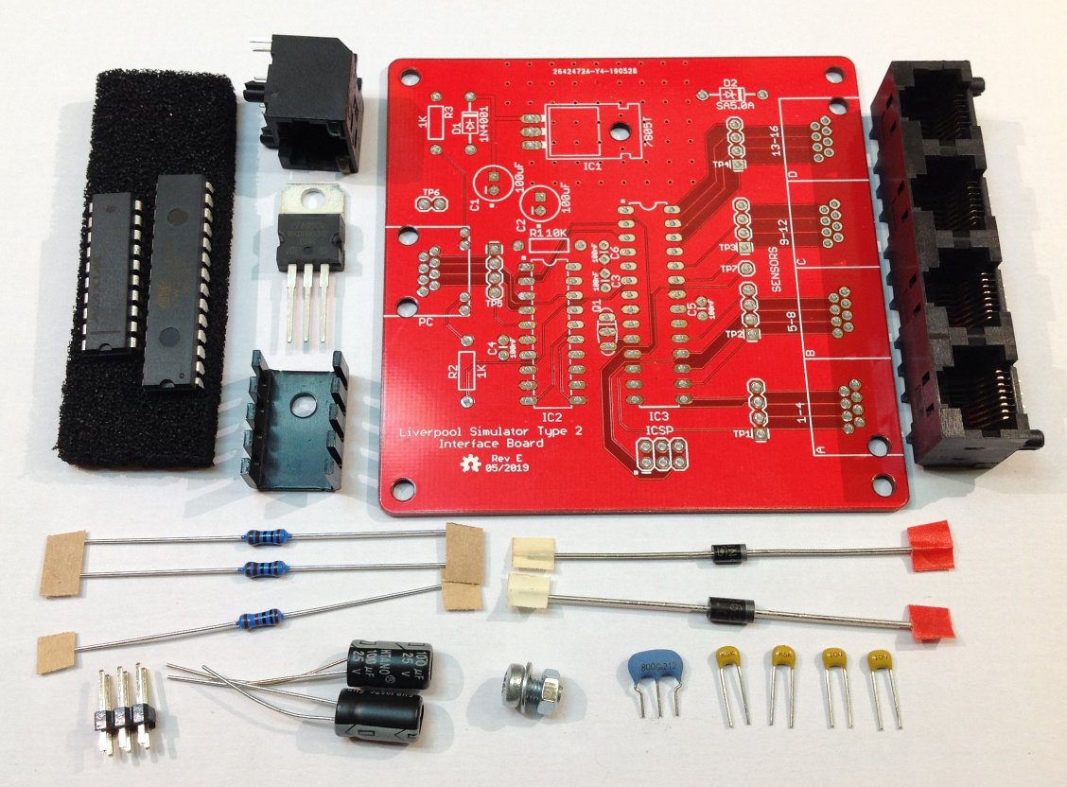
docs/source/Images/Hardware/Interface/RevE_Parts.jpg
