Simulators/simulator-type2/docs/Magnet Positioning Guide v1.0.pdf

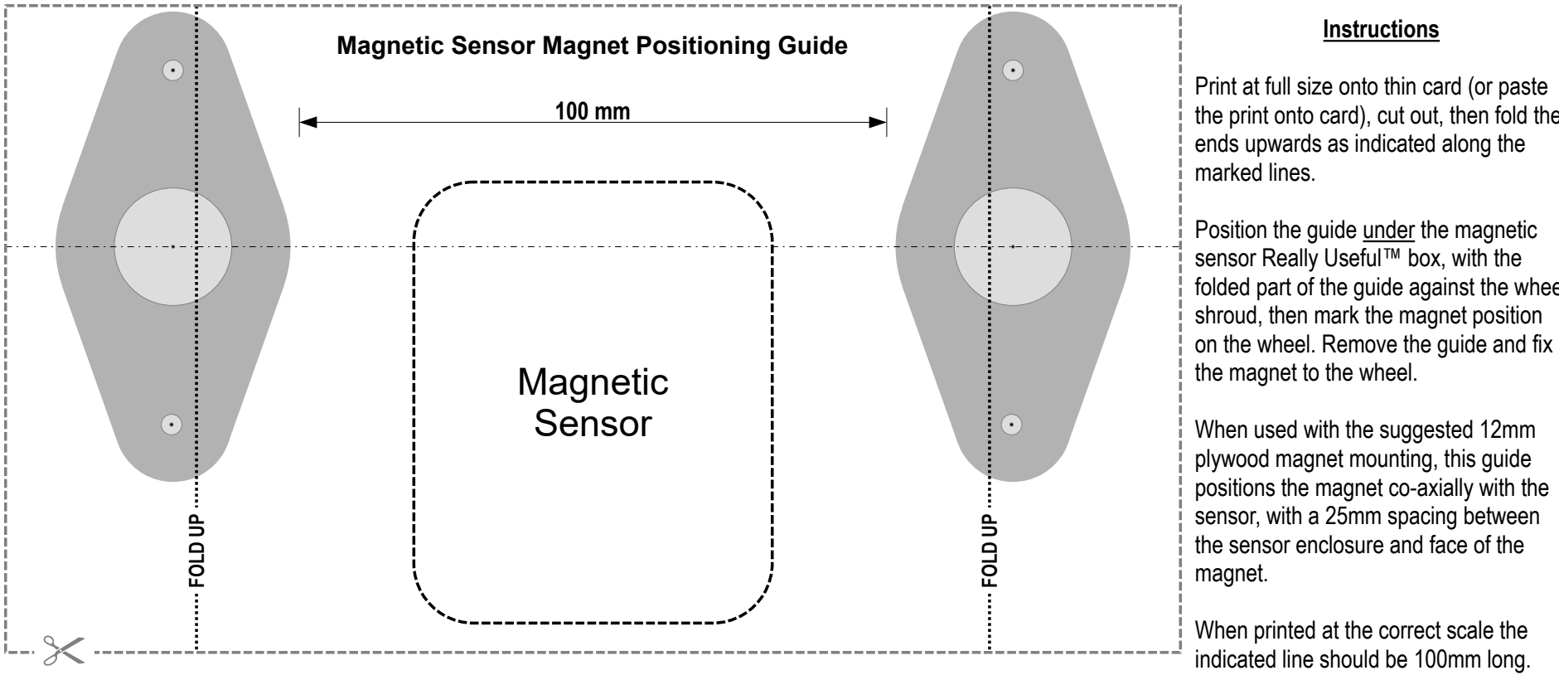
[picture p340: figure]
Magnetic Sensor; FOLD; Magnetic Sensor Magnet Positioning Guide; Instructions; ends upwards as indicated along the marked lines.; Position the guide under the magnetic sensor Really Useful™ box, with the; shroud, then mark the magnet position on the wheel. Remove the guide and fix the magnet to the wheel.; When used with the suggested 12mm plywood magnet mounting, this guide; sensor, with a 25mm spacing between the sensor enclosure and face of the magnet.; When printed at the correct scale the indicated line should be 100mm long.

v1.0

Print at full size onto thin card (or paste the print onto card), cut out, then fold the

folded part of the guide against the wheel

positions the magnet co-axially with the
