Simulators/simulator-type2/docs/source/Diagrams/PNG/02 Build Install/T2 Bell Frame Example.png

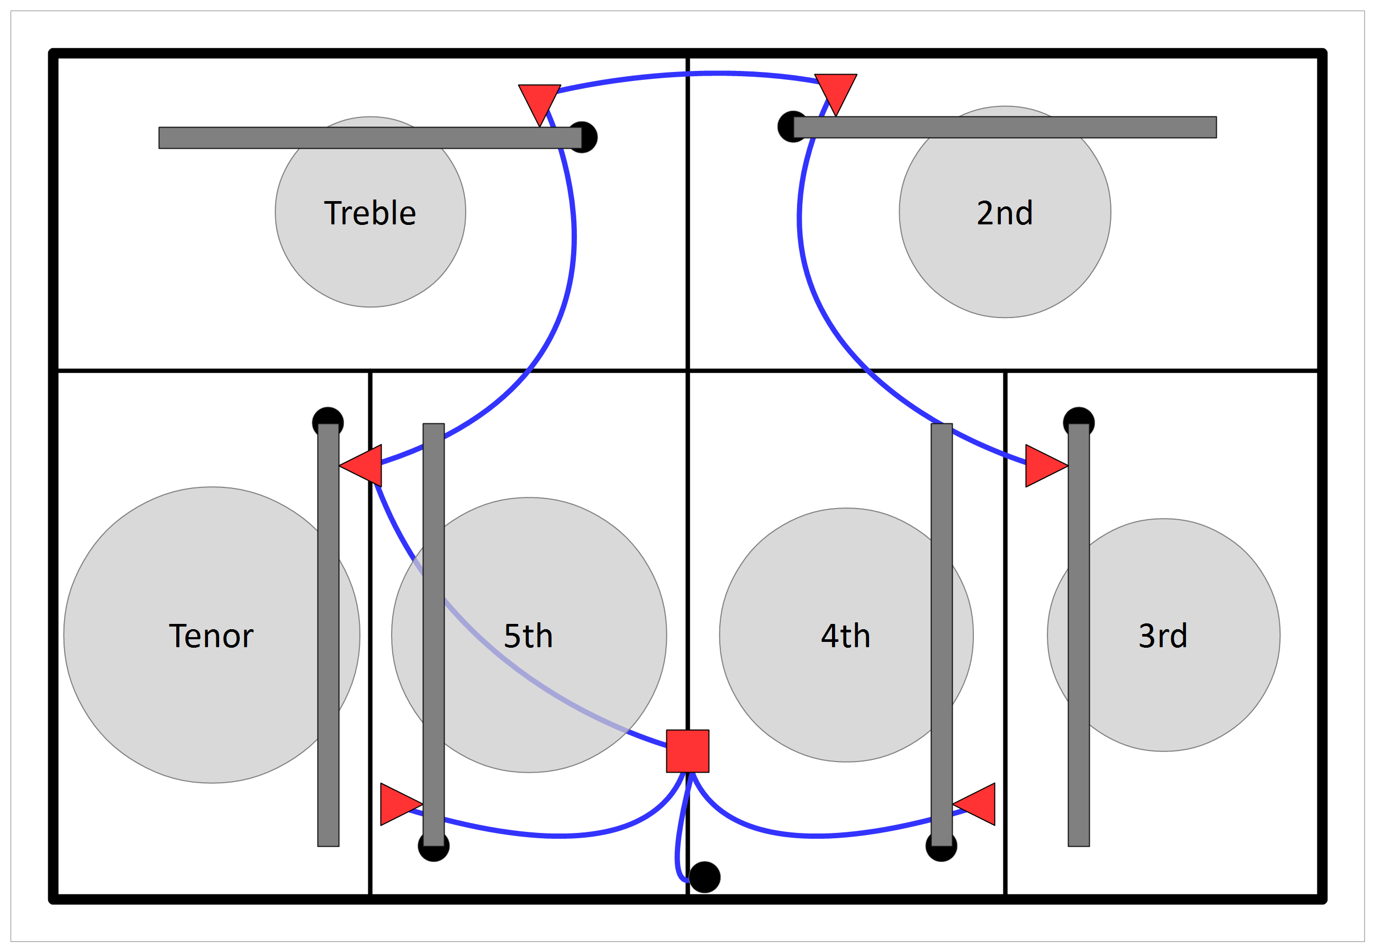
docs/source/Diagrams/PNG/02 Build Install/T2 Bell Frame Example.png
