Simulators/simulator-type2/docs/source/Diagrams/PNG/02 Build Install/T2 Channel Map Example.png

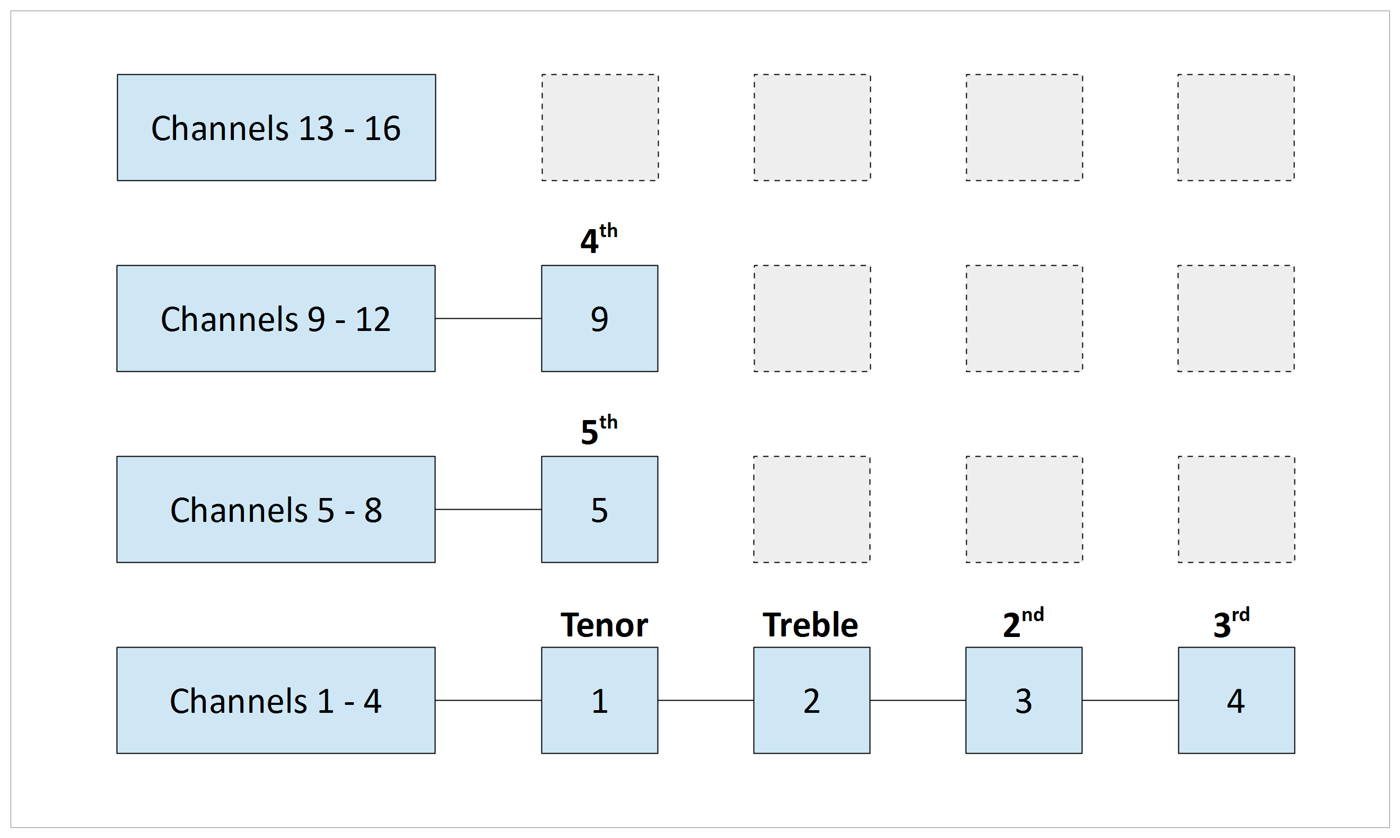
docs/source/Diagrams/PNG/02 Build Install/T2 Channel Map Example.png
