Simulators/simulator-type2/docs/source/Diagrams/PNG/02 Build Install/T2 Daisy Chain Detail Diagram.png

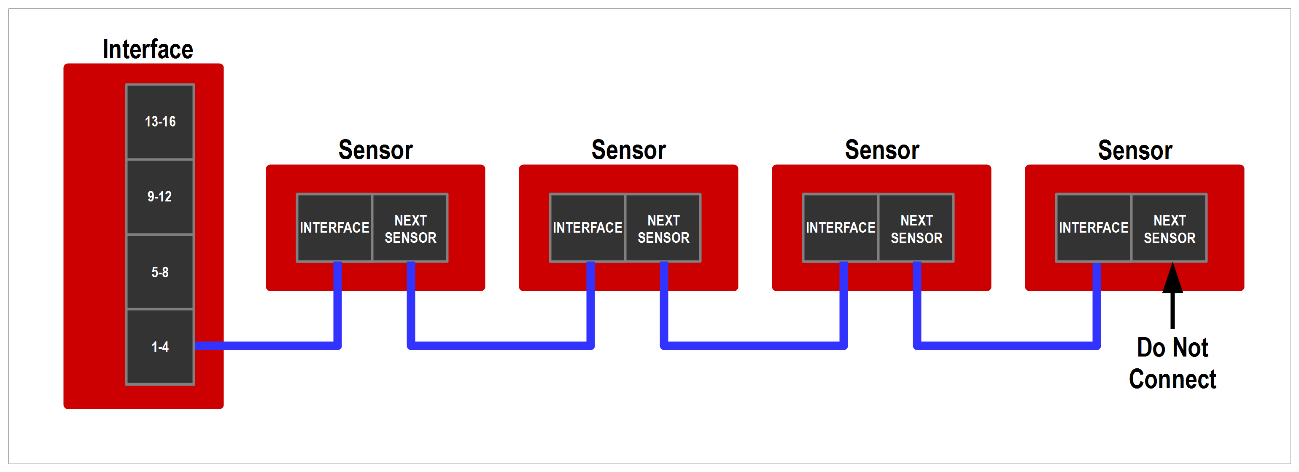
docs/source/Diagrams/PNG/02 Build Install/T2 Daisy Chain Detail Diagram.png
