Simulators/simulator-type2/docs/source/Diagrams/PNG/02 Build Install/T2 Interface Drill Guide.png

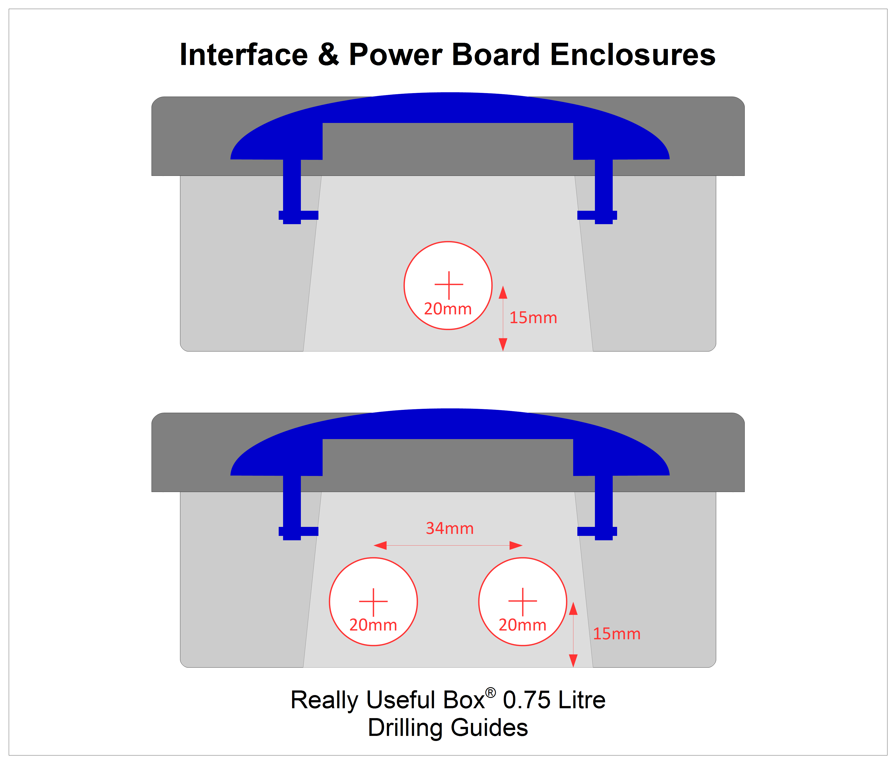
docs/source/Diagrams/PNG/02 Build Install/T2 Interface Drill Guide.png
