Simulators/simulator-type2/docs/source/Diagrams/PNG/02 Build Install/T2 IR Sensor Drill Guide v2.png

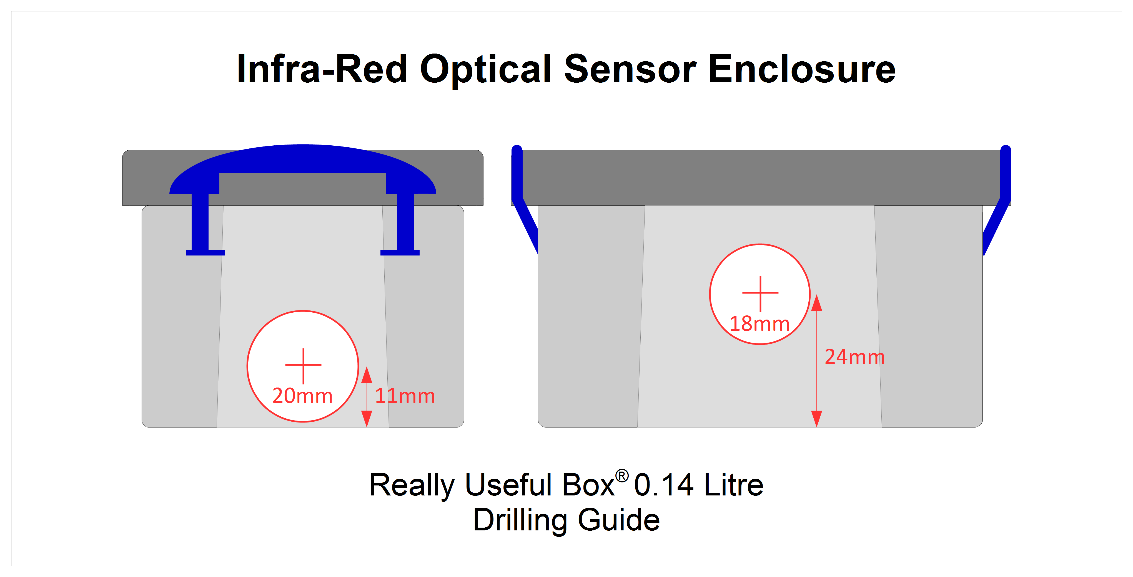
docs/source/Diagrams/PNG/02 Build Install/T2 IR Sensor Drill Guide v2.png
