Simulators/simulator-type2/docs/source/Diagrams/PNG/02 Build Install/T2 IR Sensor Wiring.png

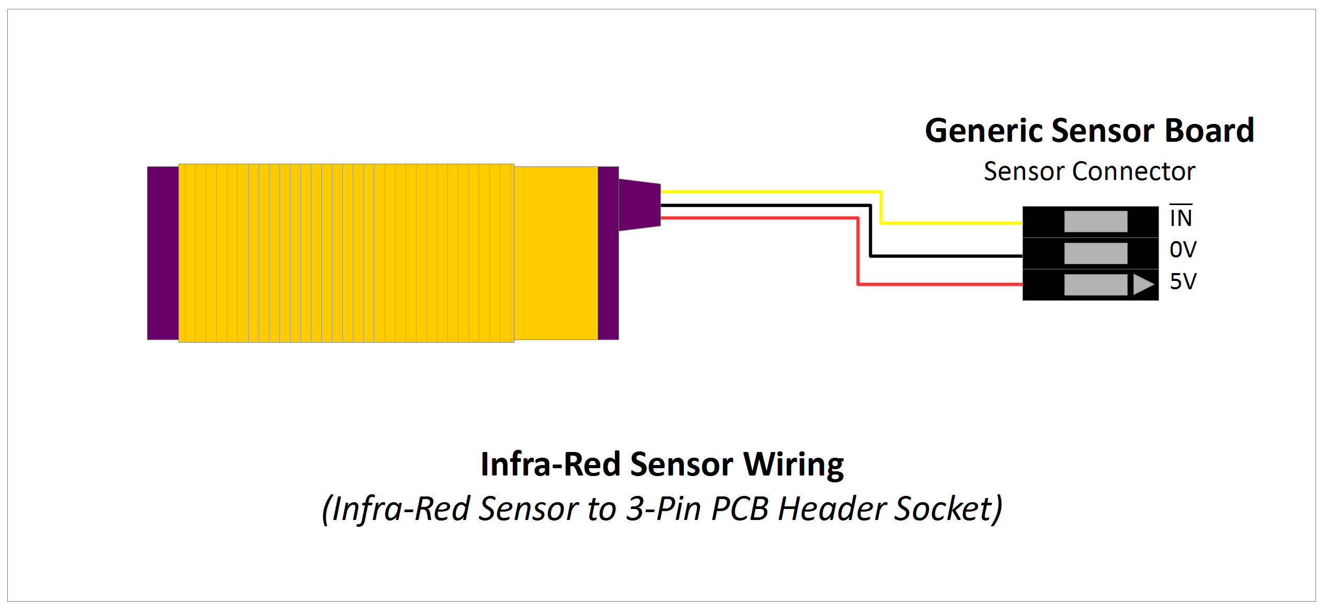
docs/source/Diagrams/PNG/02 Build Install/T2 IR Sensor Wiring.png
