Simulators/simulator-type2/docs/source/Diagrams/PNG/02 Build Install/T2 Magnet Holder Diagram v0.1.png

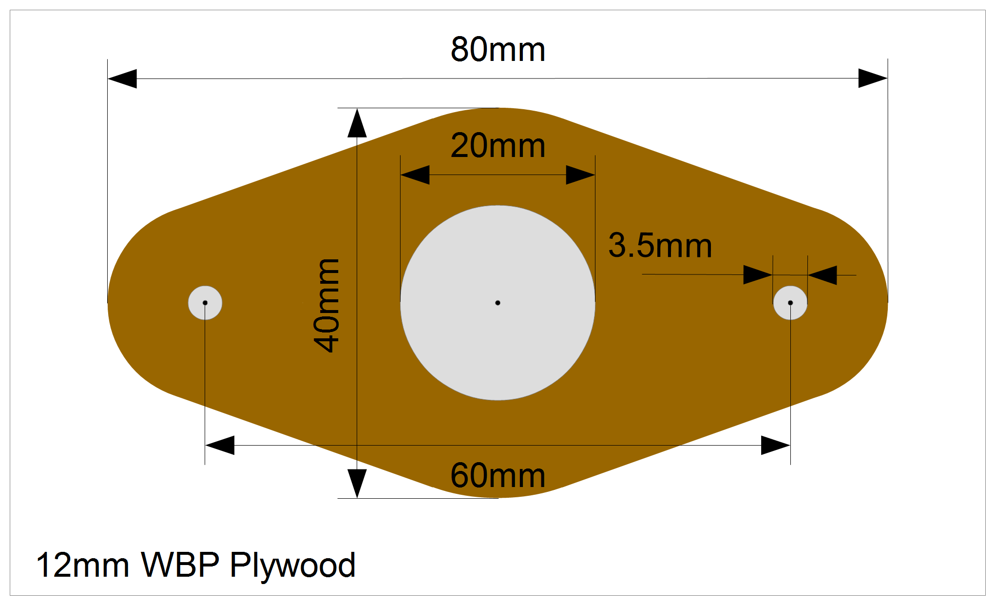
docs/source/Diagrams/PNG/02 Build Install/T2 Magnet Holder Diagram v0.1.png
