Simulators/simulator-type2/docs/source/Diagrams/PNG/02 Build Install/T2 MR Sensor Drill Guide v0.2.png

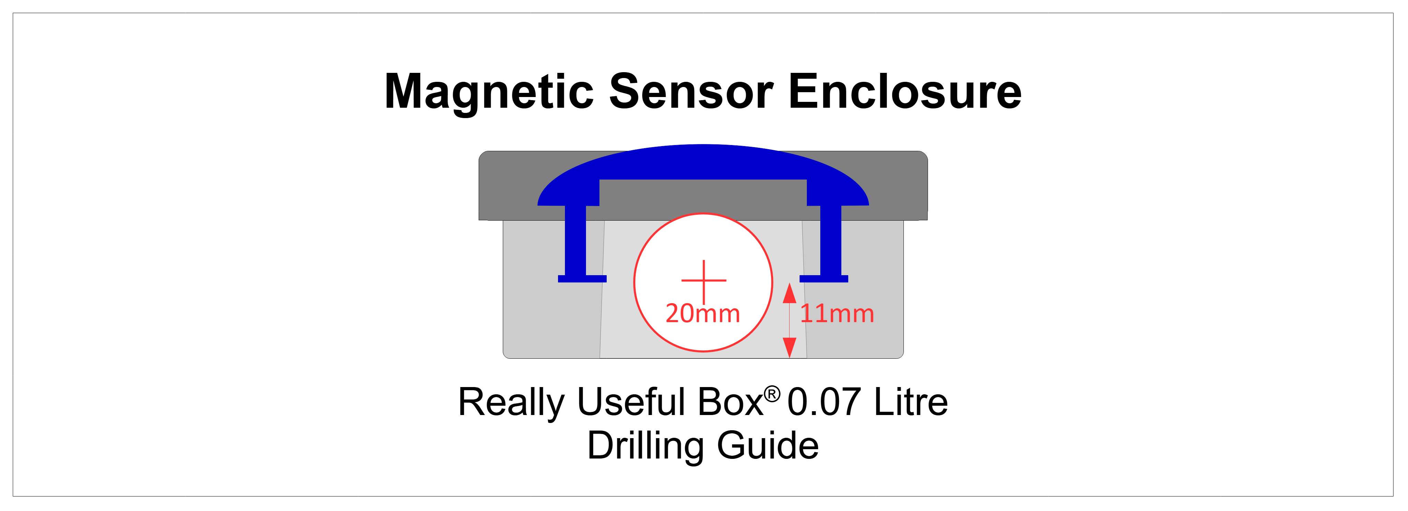
docs/source/Diagrams/PNG/02 Build Install/T2 MR Sensor Drill Guide v0.2.png
