Simulators/simulator-type2/docs/source/Diagrams/PNG/02 Build Install/T2 Voltages.png

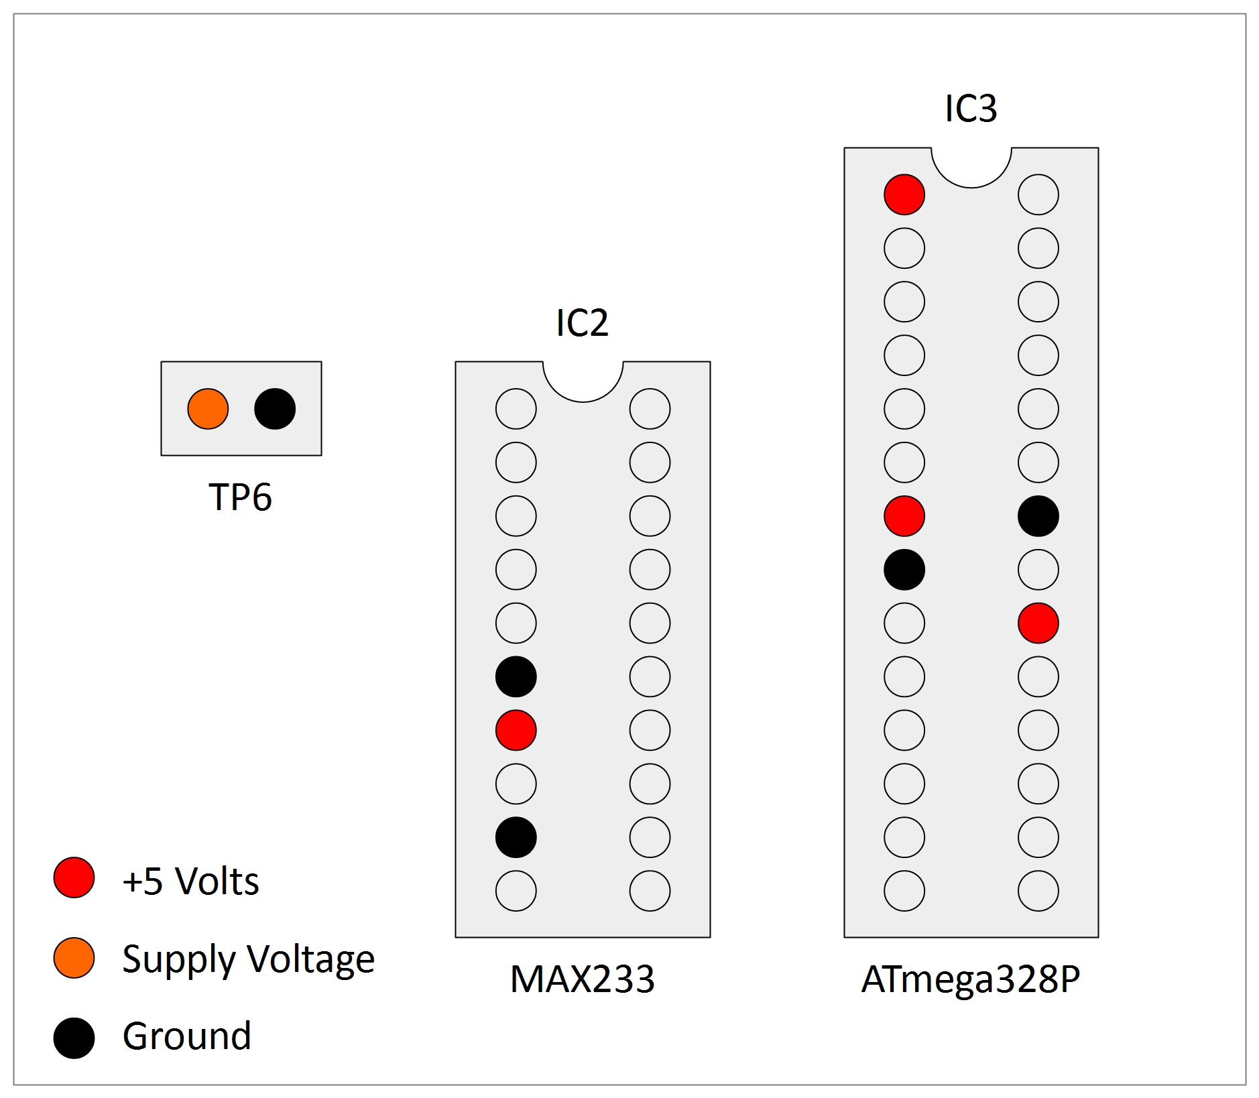
docs/source/Diagrams/PNG/02 Build Install/T2 Voltages.png
