Simulators/simulator-type2/docs/source/Images/Hardware/Interface/VR_leg_guide.png

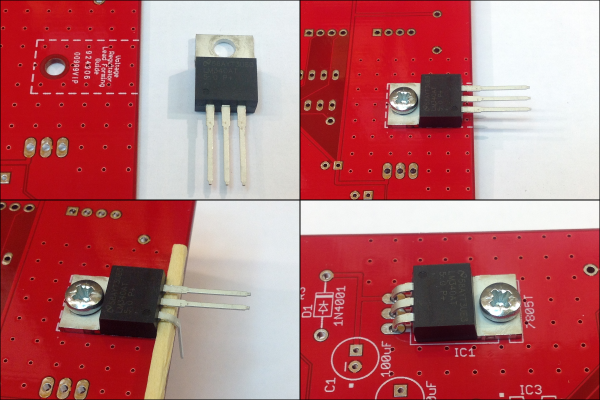
docs/source/Images/Hardware/Interface/VR_leg_guide.png
