Simulators/simulator-type2/docs/source/Diagrams/PNG/StrikingComp/Test E - Splittter Shared.png

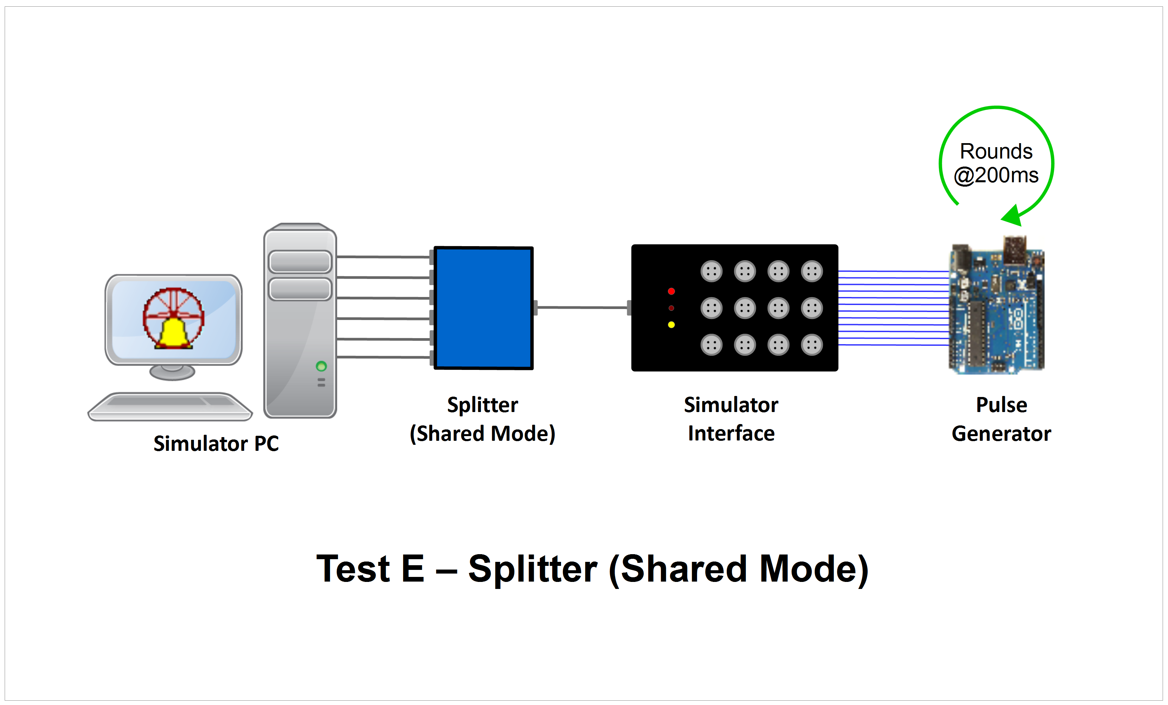
docs/source/Diagrams/PNG/StrikingComp/Test E - Splittter Shared.png
