Simulators/simulator-type2/docs/source/Screenshots/Firmware 3.3/7 - Debug Mode21.png

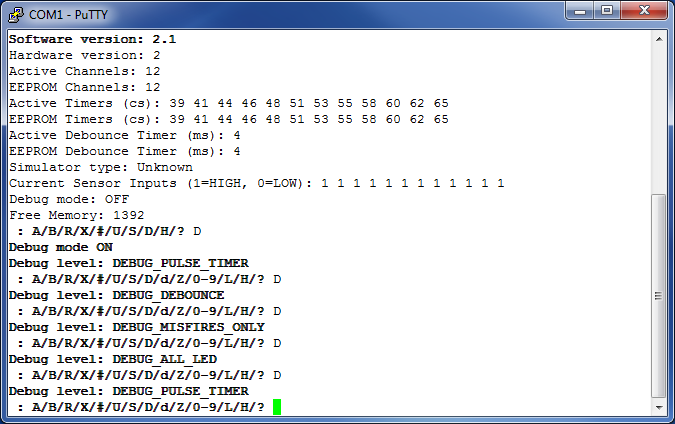
docs/source/Screenshots/Firmware 3.3/7 - Debug Mode21.png
