Simulators/simulator-type2/docs/source/Screenshots/Firmware 3.3/8 - Debug Data21.png

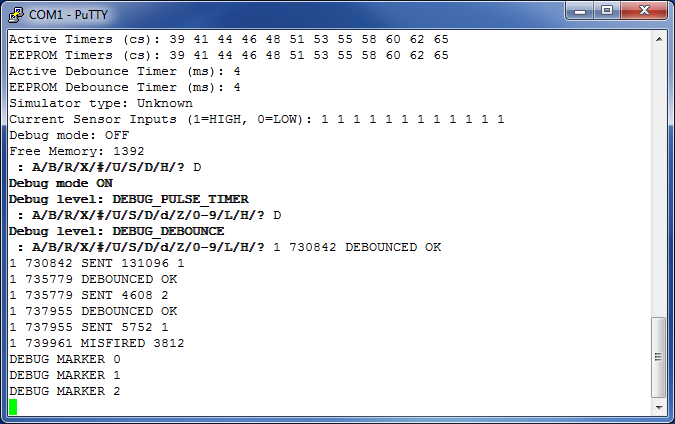
docs/source/Screenshots/Firmware 3.3/8 - Debug Data21.png
