Simulators/simulator-type2/docs/source/Images/PCBs/MR Sensor/SimulatorT2MRSensorRevE_Schematic.pdf

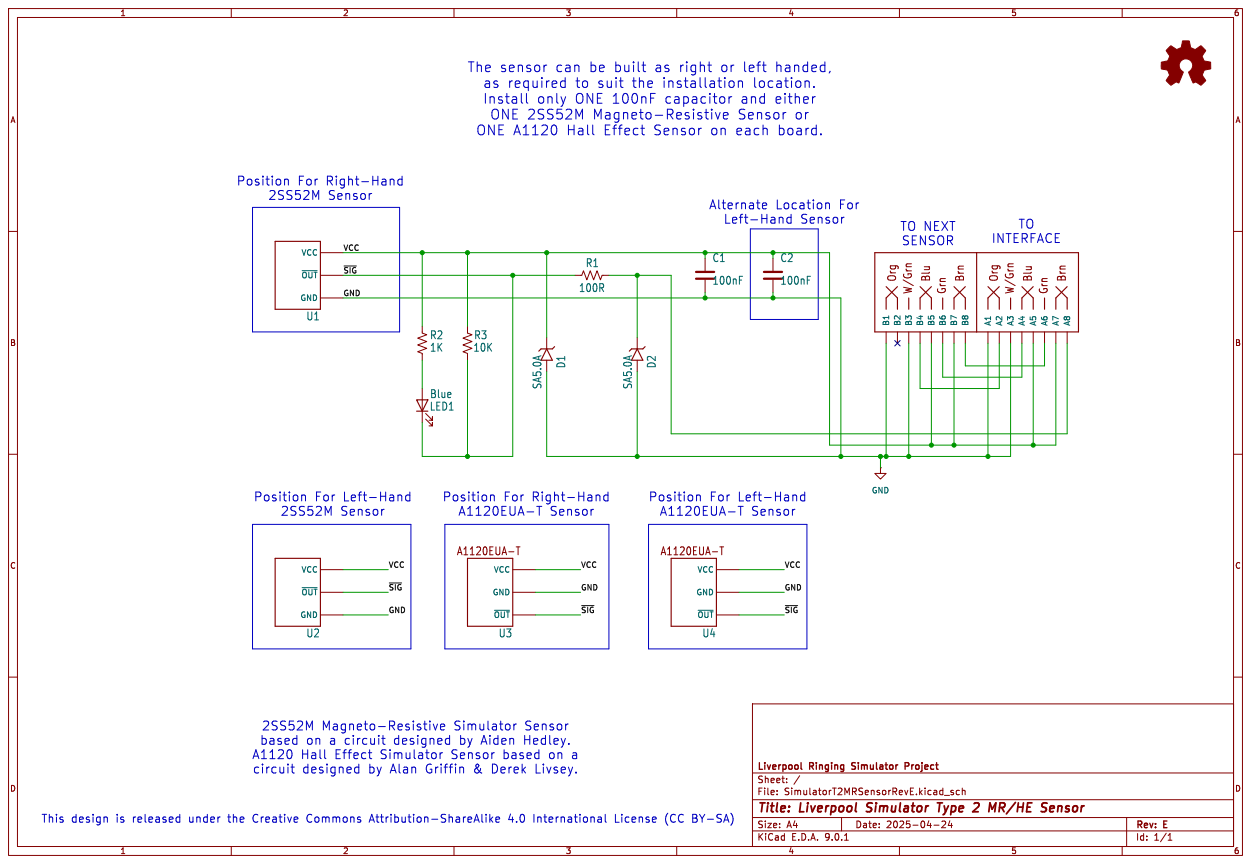
[picture p363: page 1]

The sensor can be built as right or left handed,
ONE A1120 Hall Effect Sensor on each board.

Position For Left-Hand
2SS52M Sensor

Position For Right-Hand

based on a circuit designed by Aiden Hedley.
circuit designed by Alan Griffin & Derek Livsey.
