Simulators/simulator-type2/docs/Enclosure Drilling Templates - Core v1.1.pdf

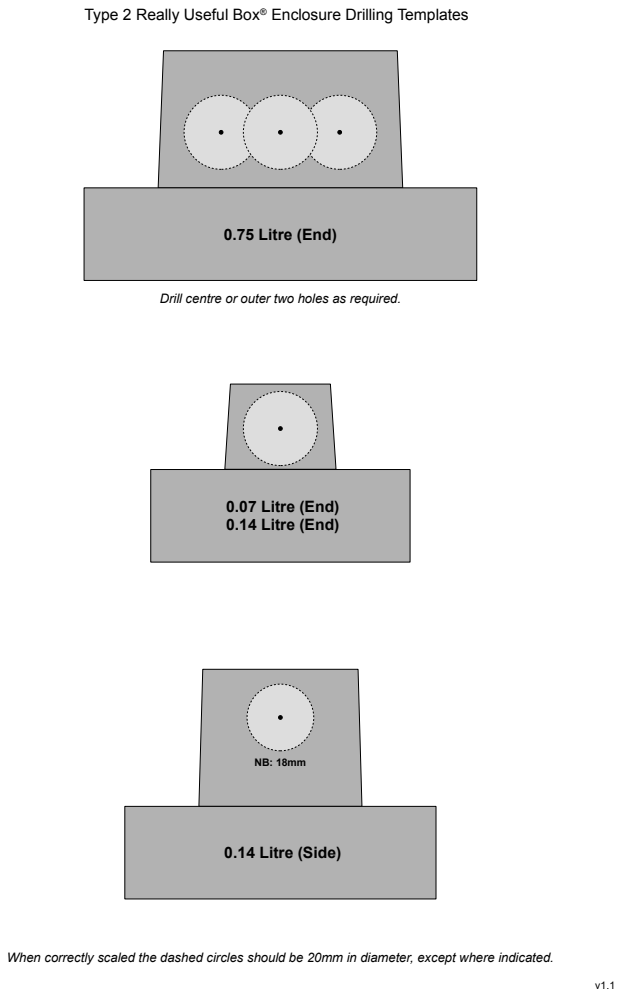
[picture p364: page 1]
0.75 Litre (End); 0.07 Litre (End) 0.14 Litre (End); 0.14 Litre (Side)

Type 2 Really Useful Box® Enclosure Drilling Templates

Drill centre or outer two holes as required.

When correctly scaled the dashed circles should be 20mm in diameter, except where indicated.

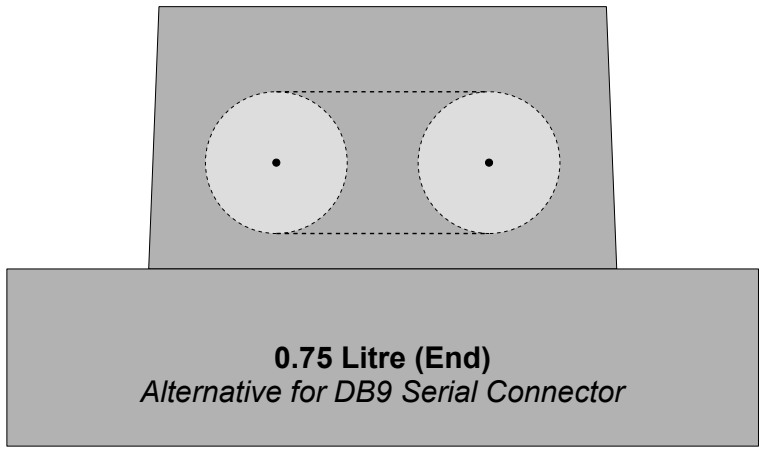
[picture p365: figure]
0.75 Litre (End) Alternative for DB9 Serial Connector

When correctly scaled the dashed circles should be 20mm in diameter, except where indicated.

### Type 2 Really Useful Box® Enclosure Drilling Templates

v1.1

Drill both holes and trim out area between dotted lines.
