Simulators/simulator-type2/docs/Enclosure Drilling Templates - Basic Serial Splitter v1.0.pdf

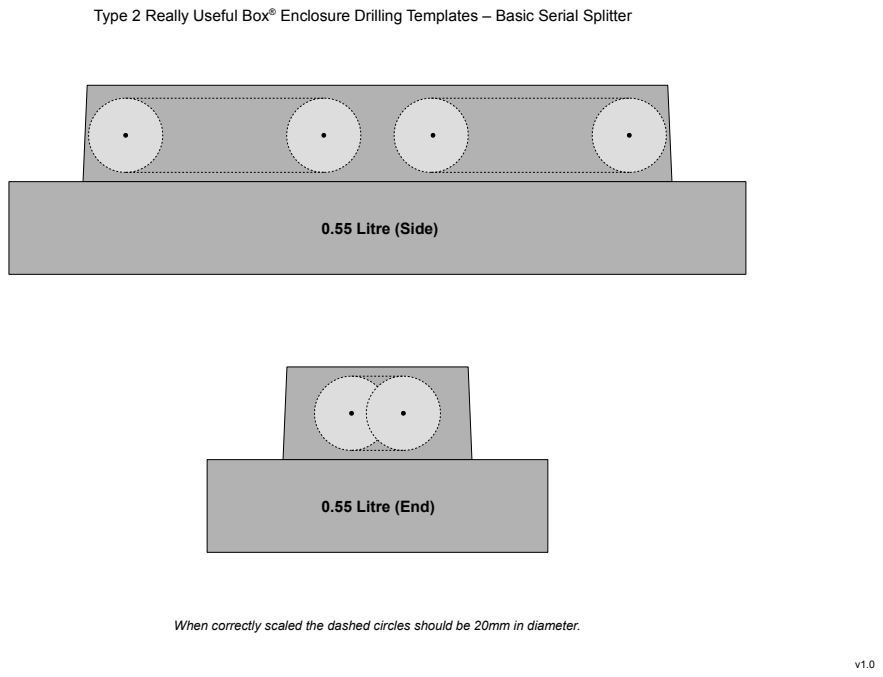
[picture p366: page 1]
0.55 Litre (End); 0.55 Litre (Side)

Type 2 Really Useful Box® Enclosure Drilling Templates – Basic Serial Splitter

When correctly scaled the dashed circles should be 20mm in diameter.
