Simulators/simulator-type2/docs/Magnet Mount Template v1.0.pdf

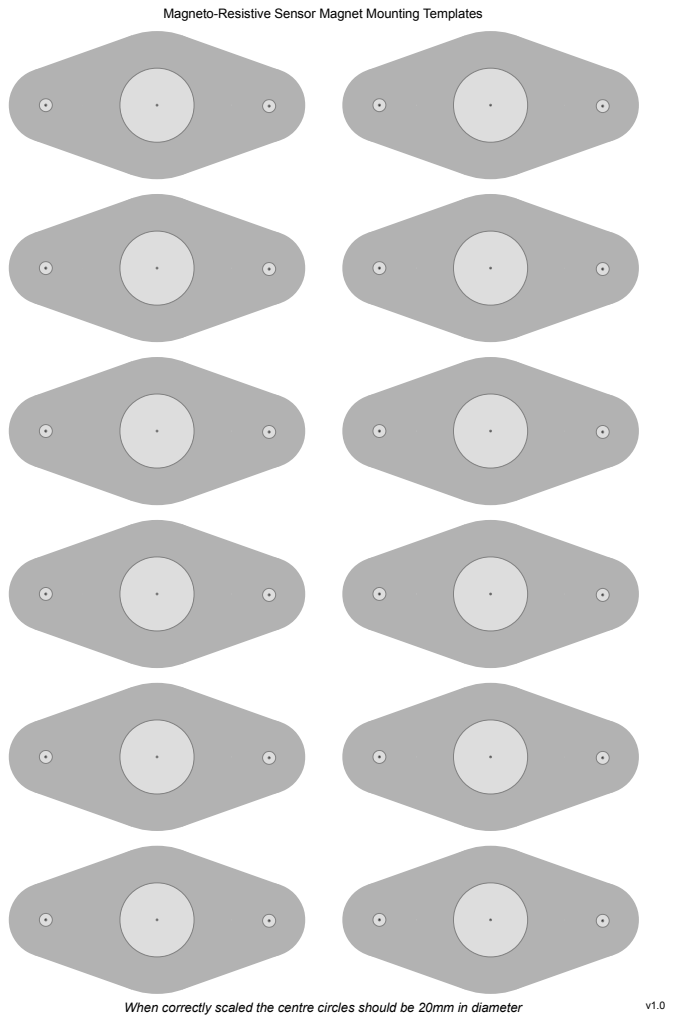
[picture p367: page 1]
When correctly scaled the centre circles should be 20mm in diameter

Magneto-Resistive Sensor Magnet Mounting Templates
