Simulators/simulator-type2/hardware/eagle/type2genericsensor/SimulatorT2GenericSensorRevC_brd.pdf

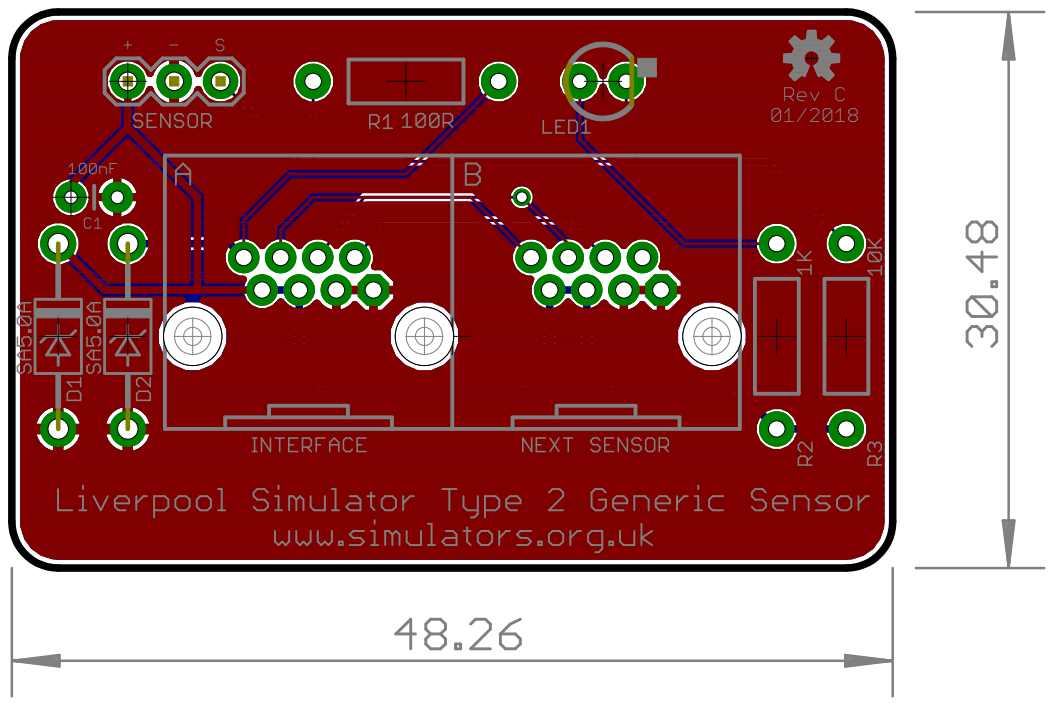
[picture p372: page 1]
