Simulators/simulator-type2/hardware/eagle/type2genericsensor/SimulatorT2GenericSensorRevC_panel6_brd.pdf

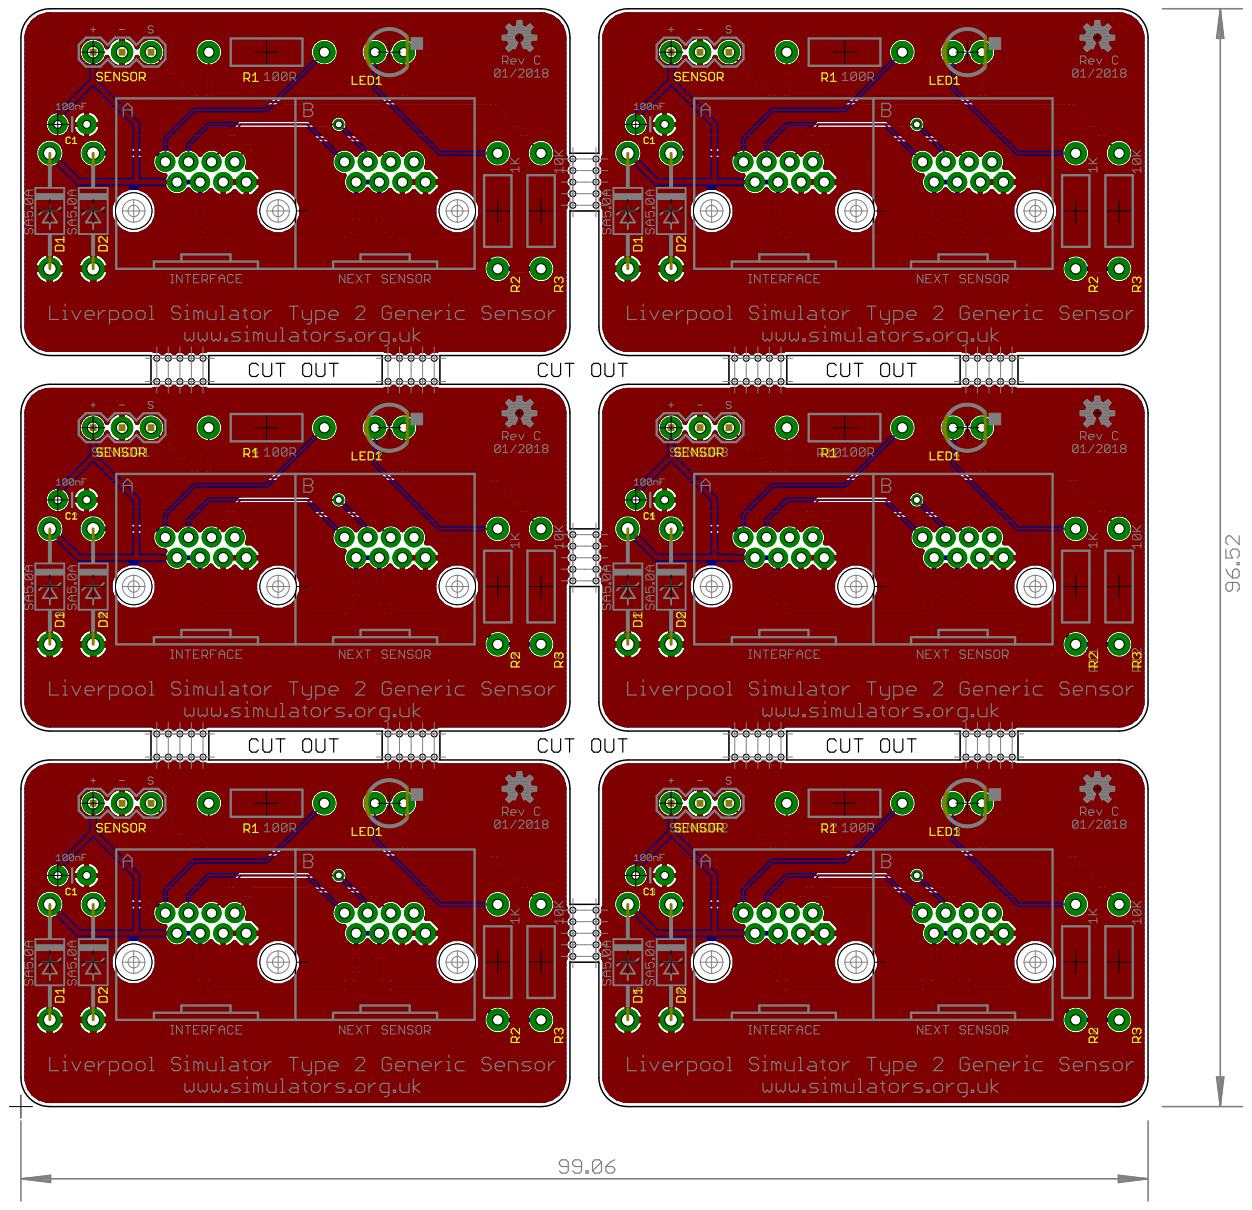
[picture p373: page 1]
