Simulators/simulator-type2/hardware/eagle/type2genericsensor/SimulatorT2GenericSensorRevC_sch.pdf

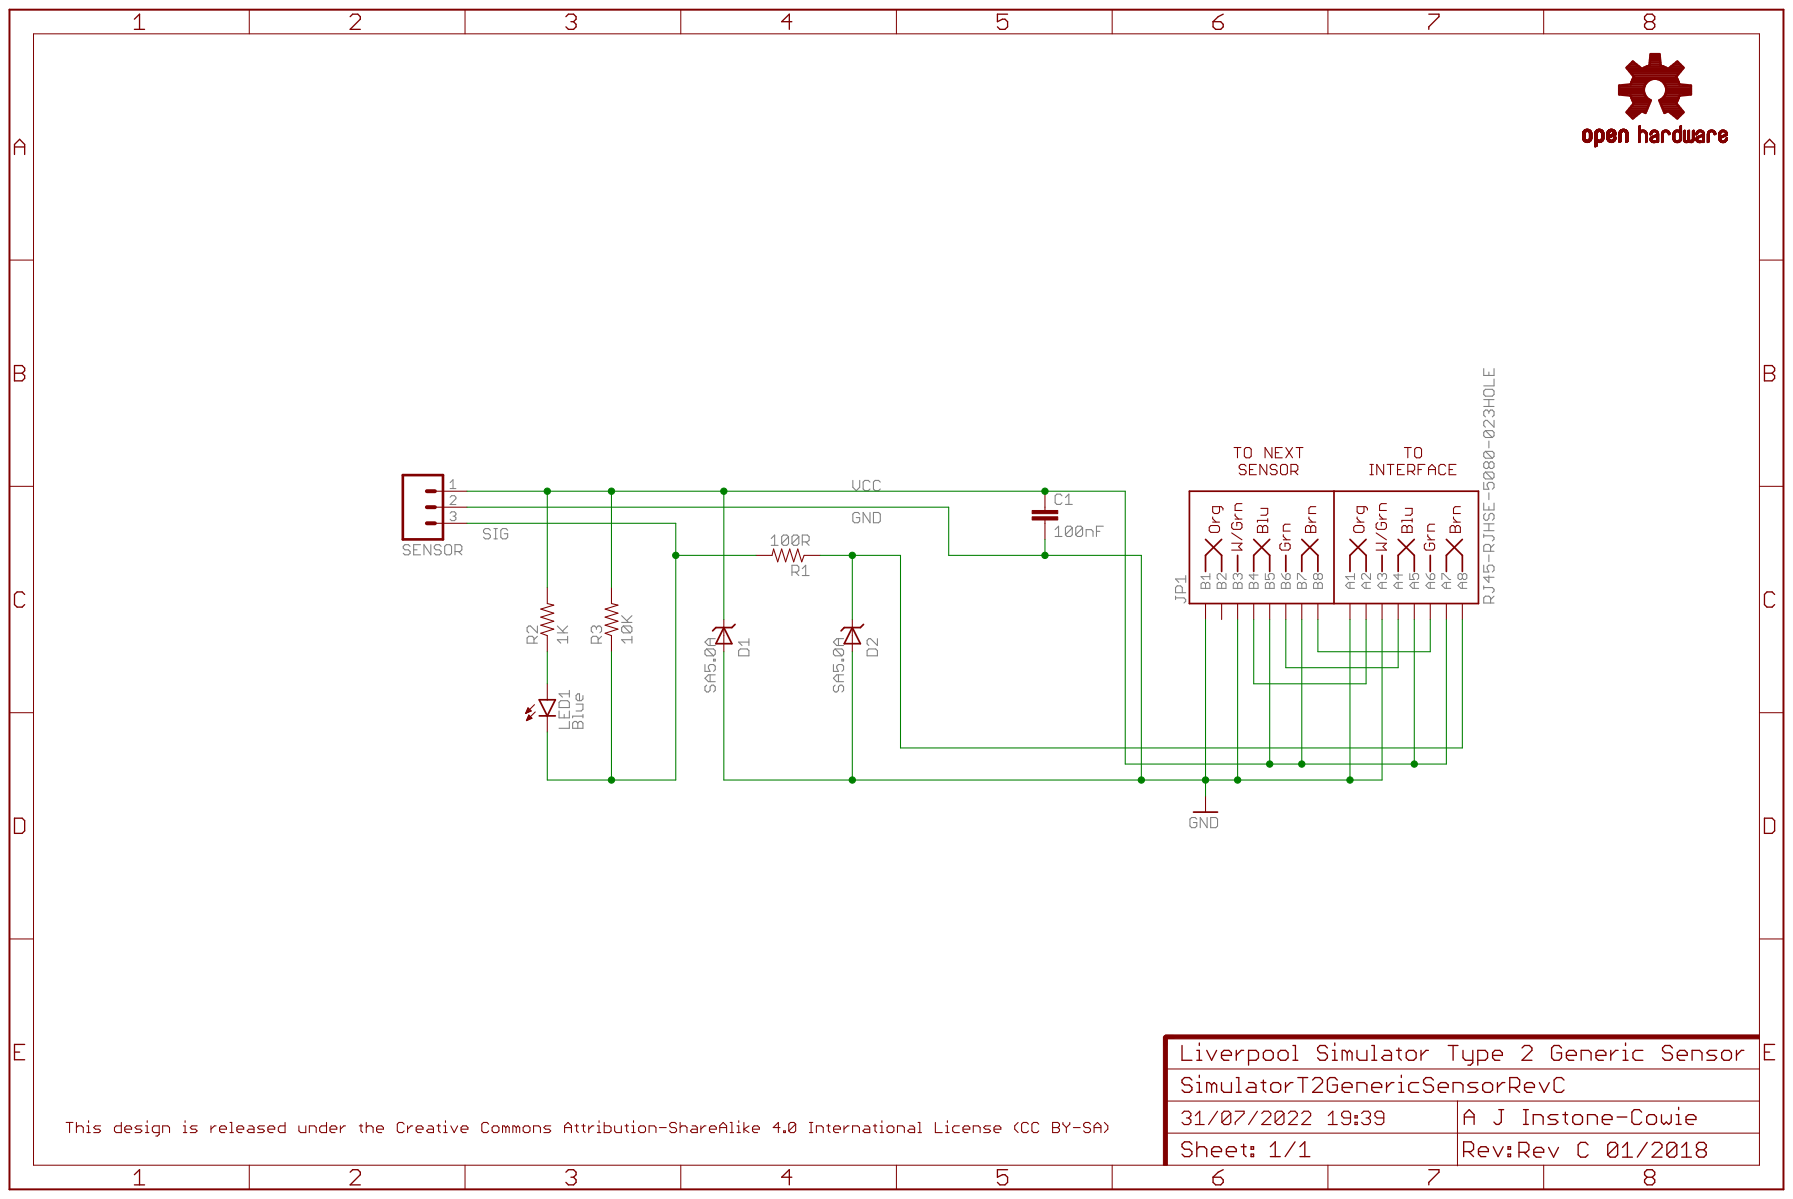
[picture p374: page 1]
