Simulators/simulator-type2/hardware/eagle/type2interface/SimulatorT2InterfaceRevE_brd.pdf

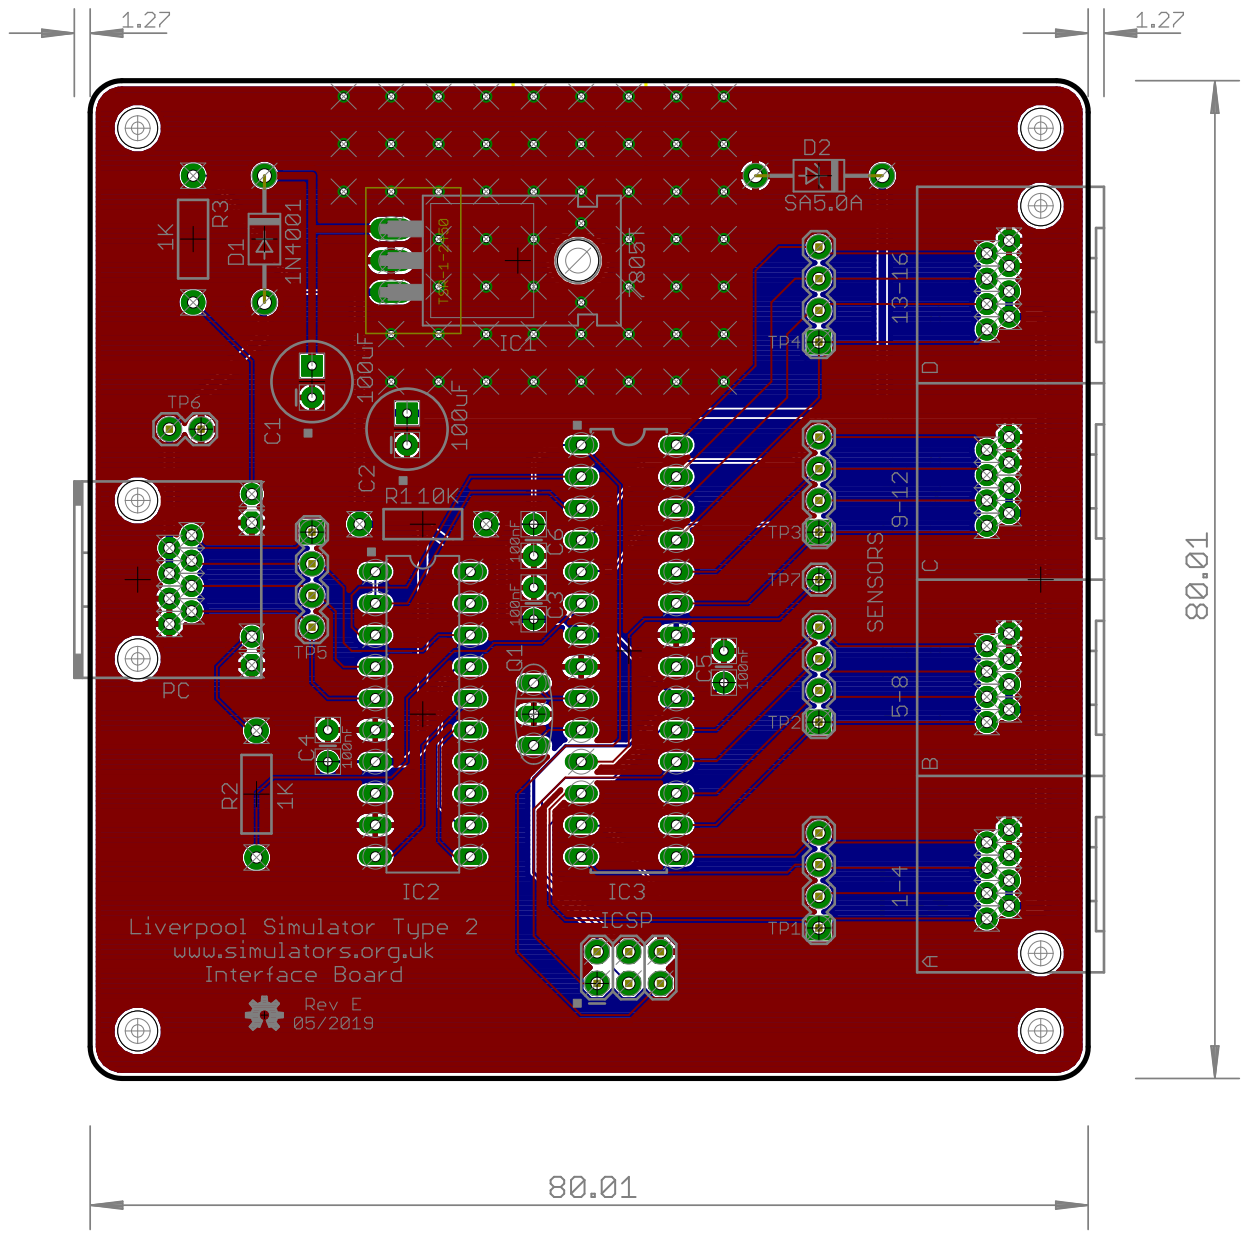
[picture p375: page 1]
