Simulators/simulator-type2/hardware/eagle/type2interface/SimulatorT2InterfaceRevE_sch.pdf

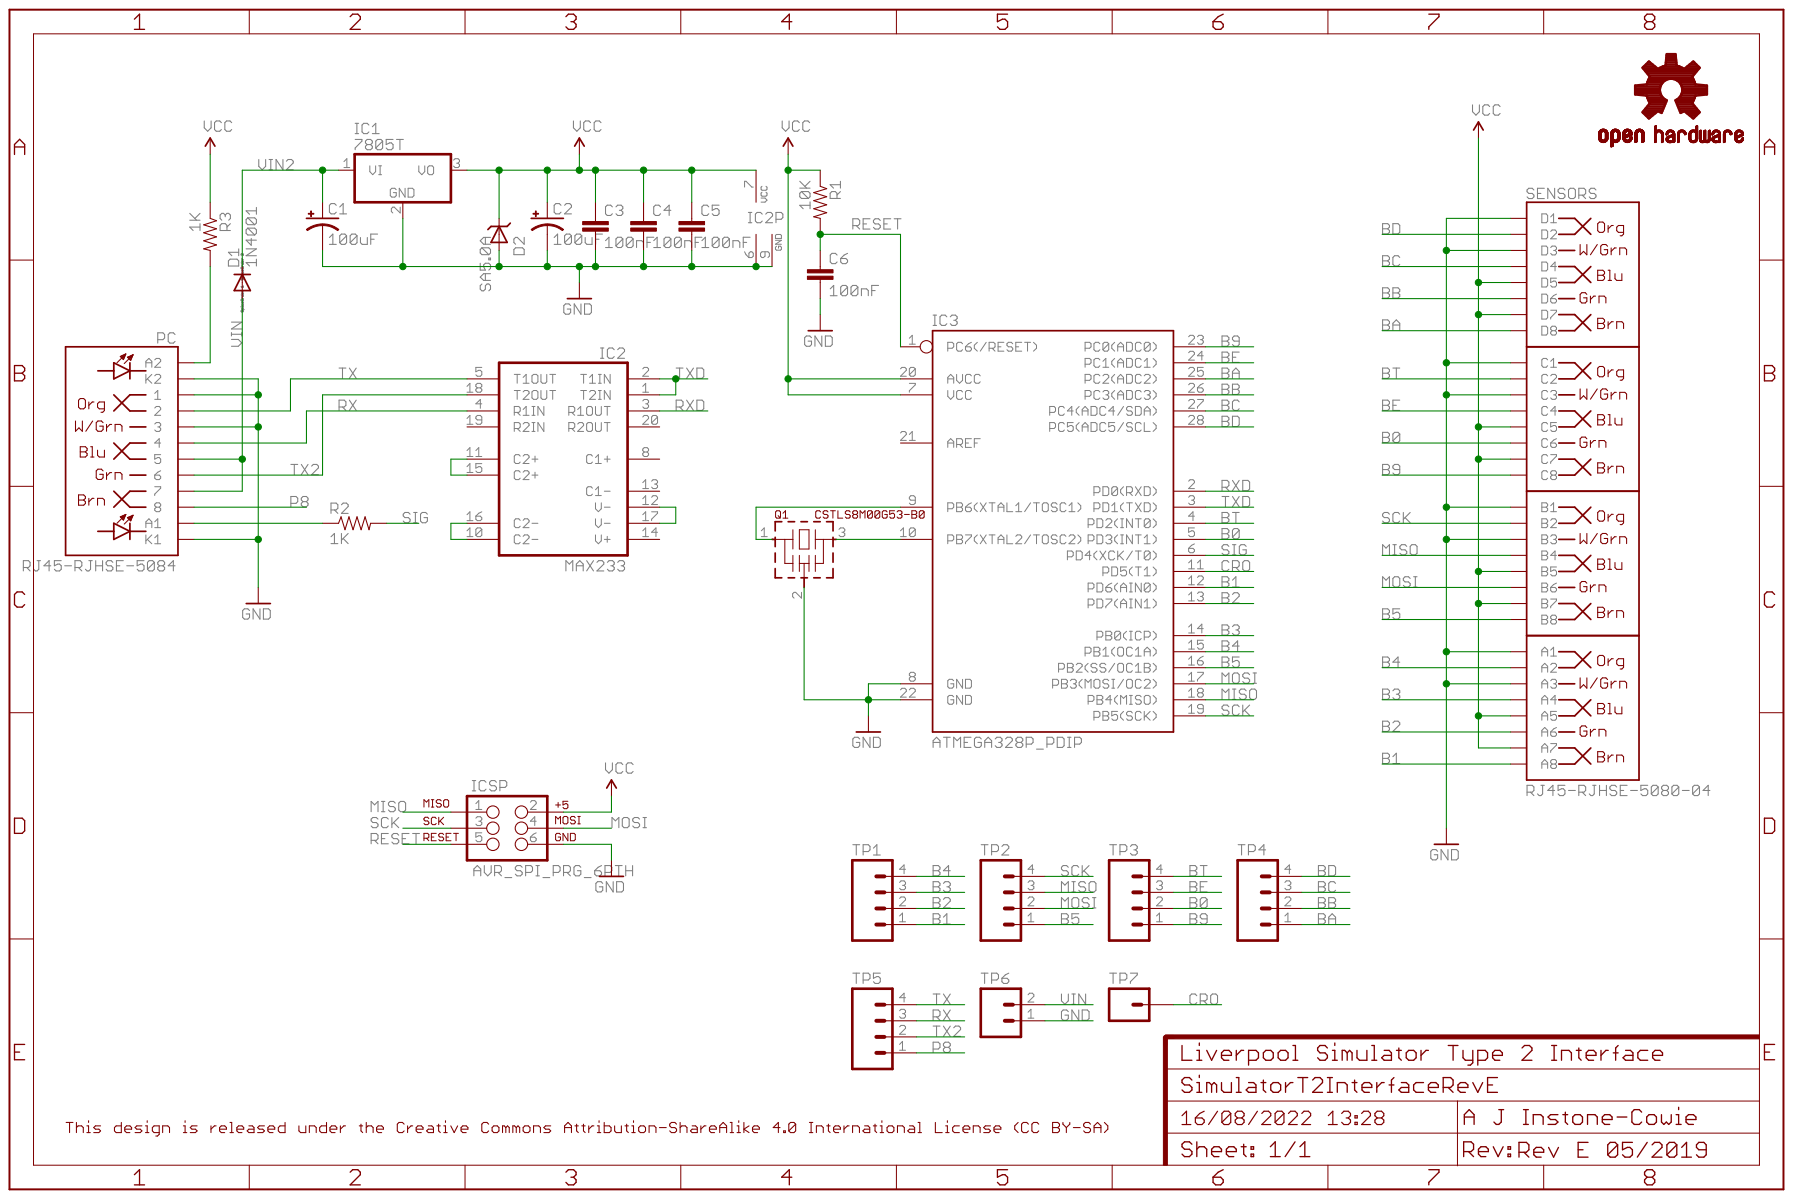
[picture p376: page 1]
