Simulators/simulator-type2/hardware/eagle/type2magneticsensor/SimulatorT2MRSensorRevD_brd.pdf

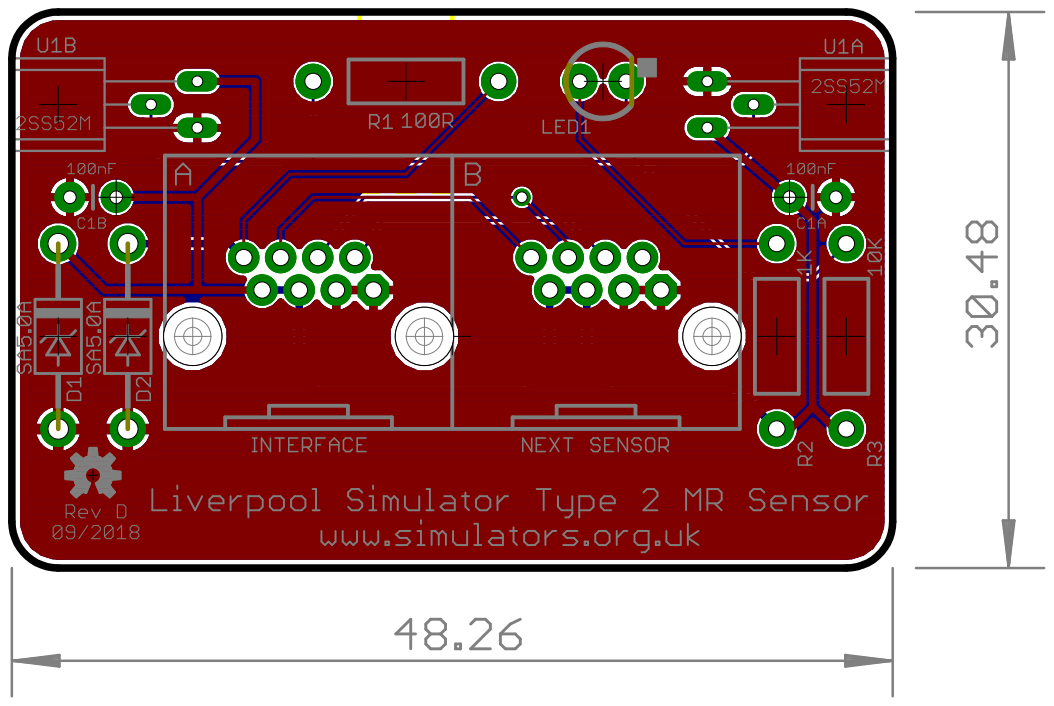
[picture p377: page 1]
