Simulators/simulator-type2/hardware/eagle/type2magneticsensor/SimulatorT2MRSensorRevD_panel6_brd.pdf

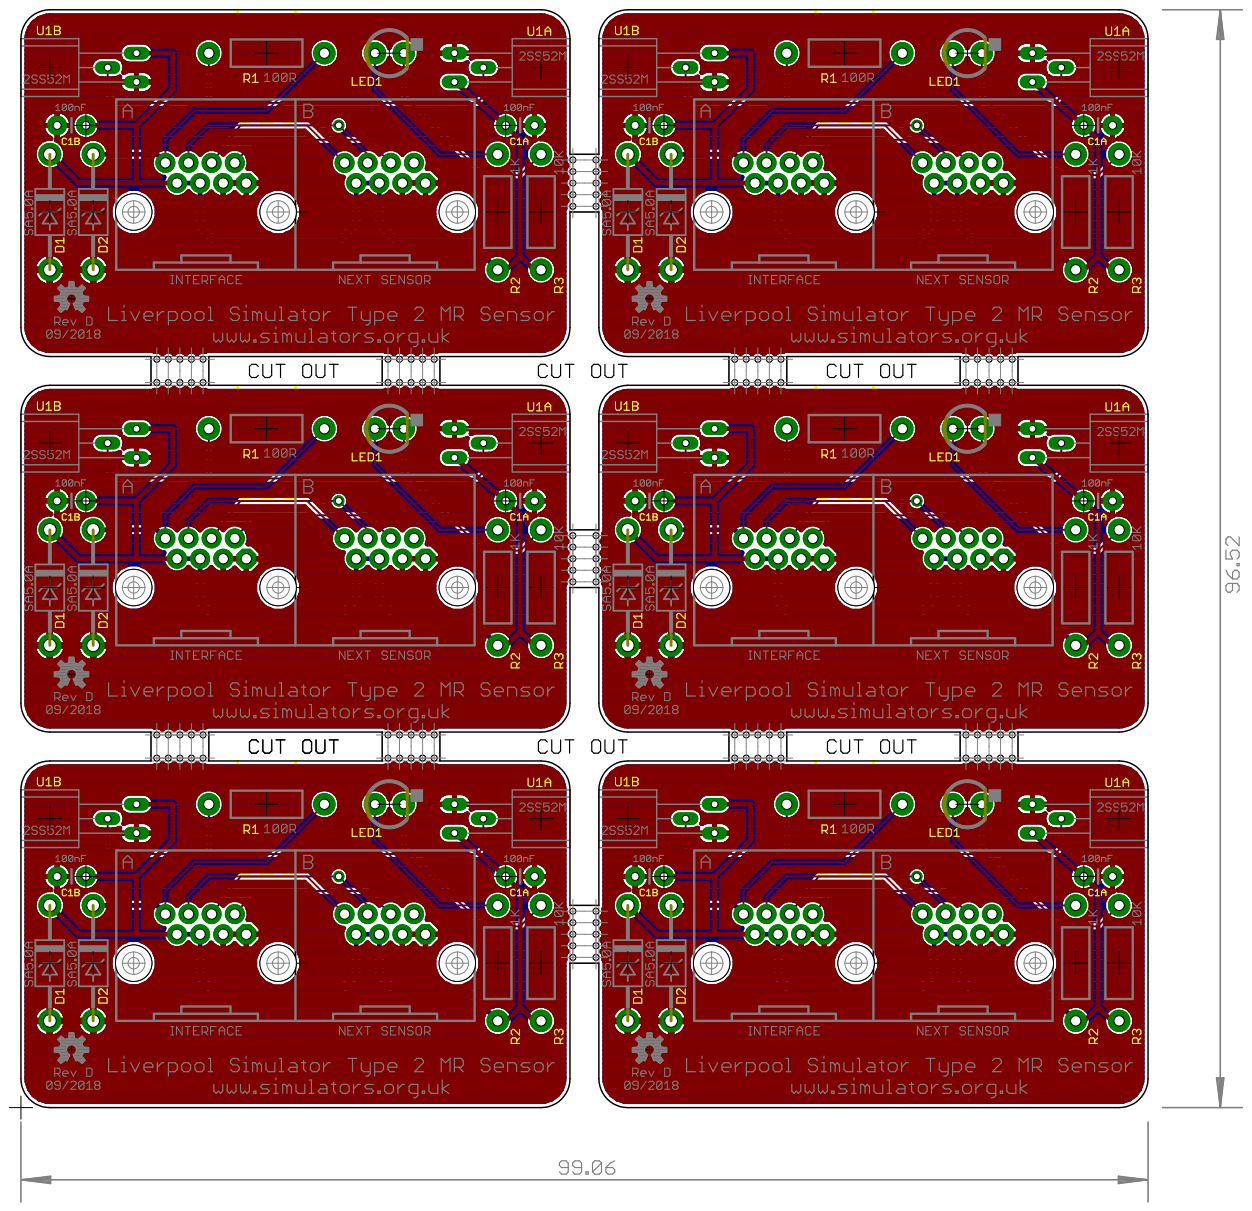
[picture p378: page 1]
