Simulators/simulator-type2/hardware/eagle/type2magneticsensor/SimulatorT2MRSensorRevD_sch.pdf

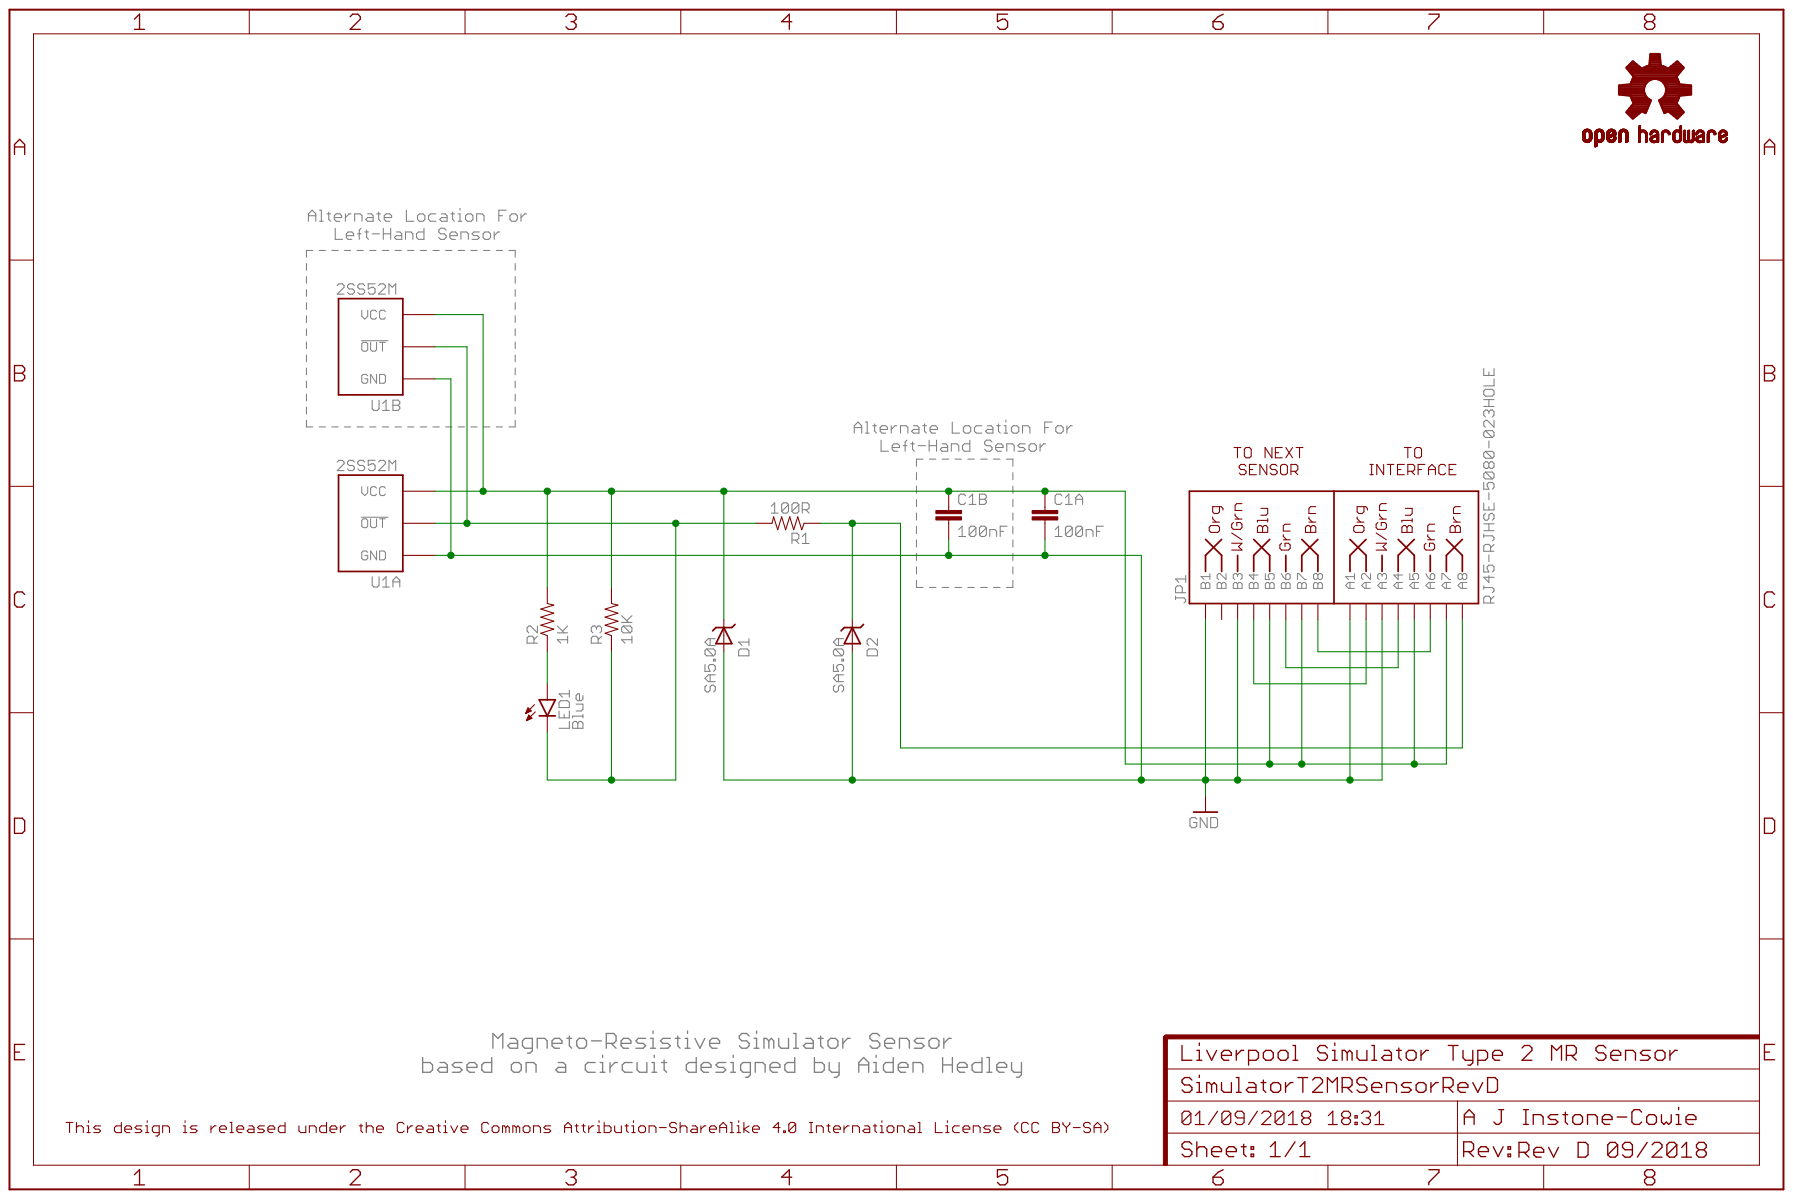
[picture p379: page 1]
