Simulators/simulator-type2/hardware/eagle/type2power/SimulatorT2PowerRevD_brd.pdf

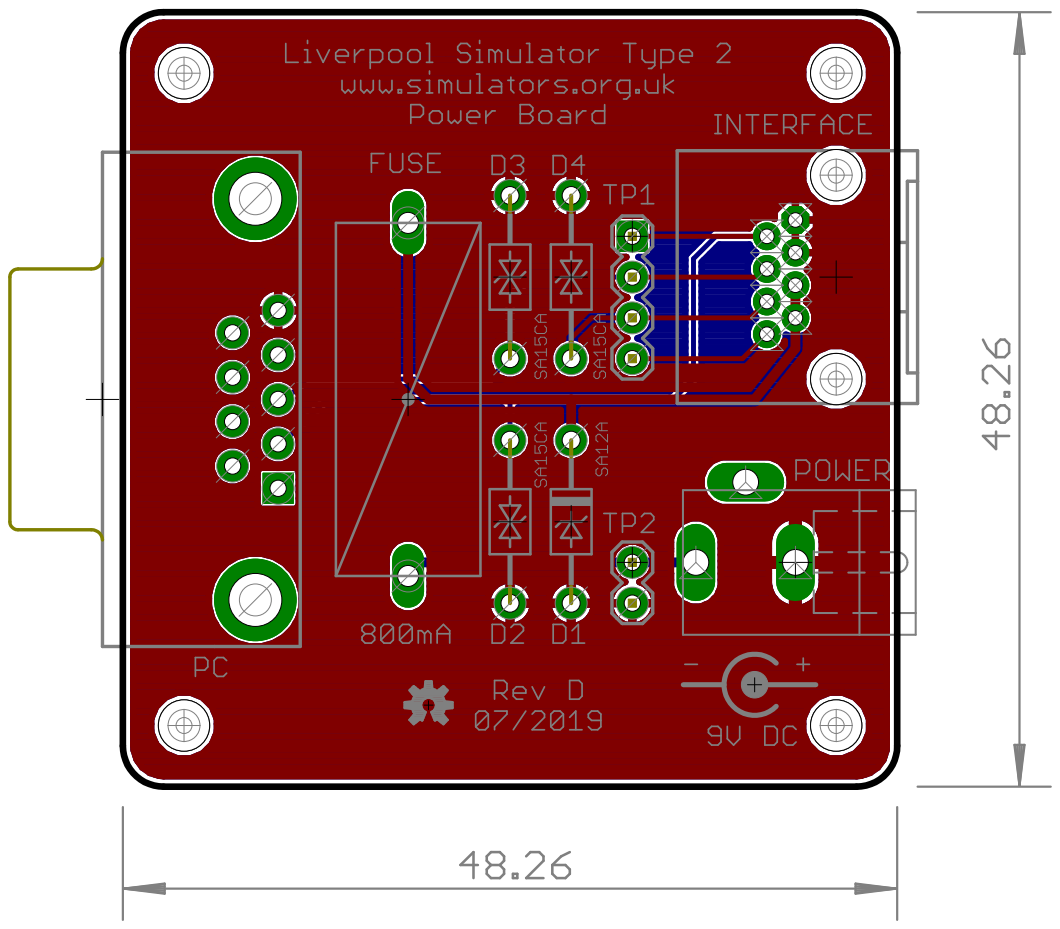
[picture p380: page 1]
