Simulators/simulator-type2/hardware/eagle/type2power/SimulatorT2PowerRevD_panel4_brd.pdf

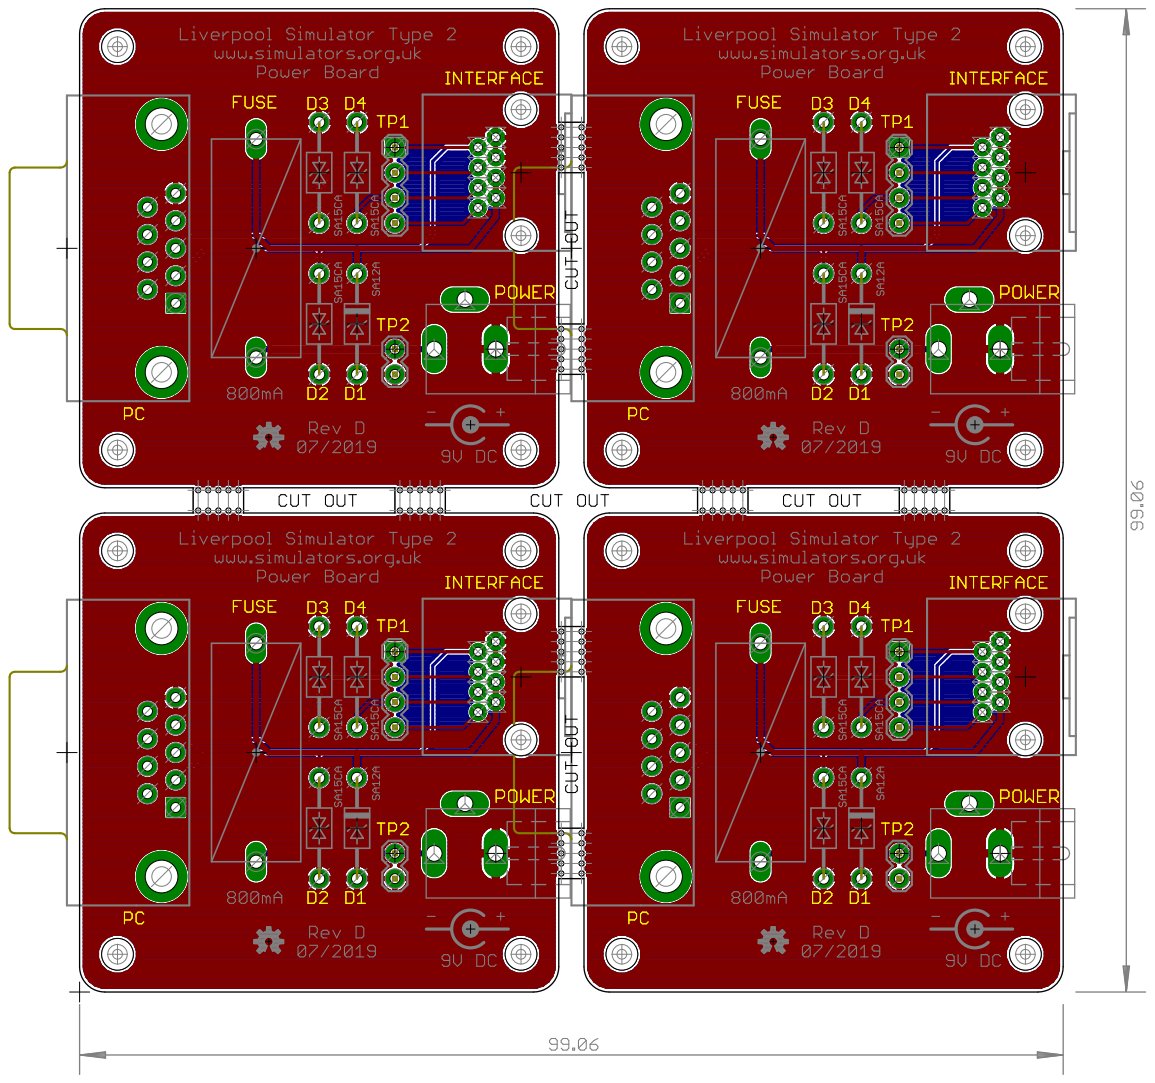
[picture p381: page 1]
