Simulators/simulator-type2/hardware/eagle/type2power/SimulatorT2PowerRevD_sch.pdf

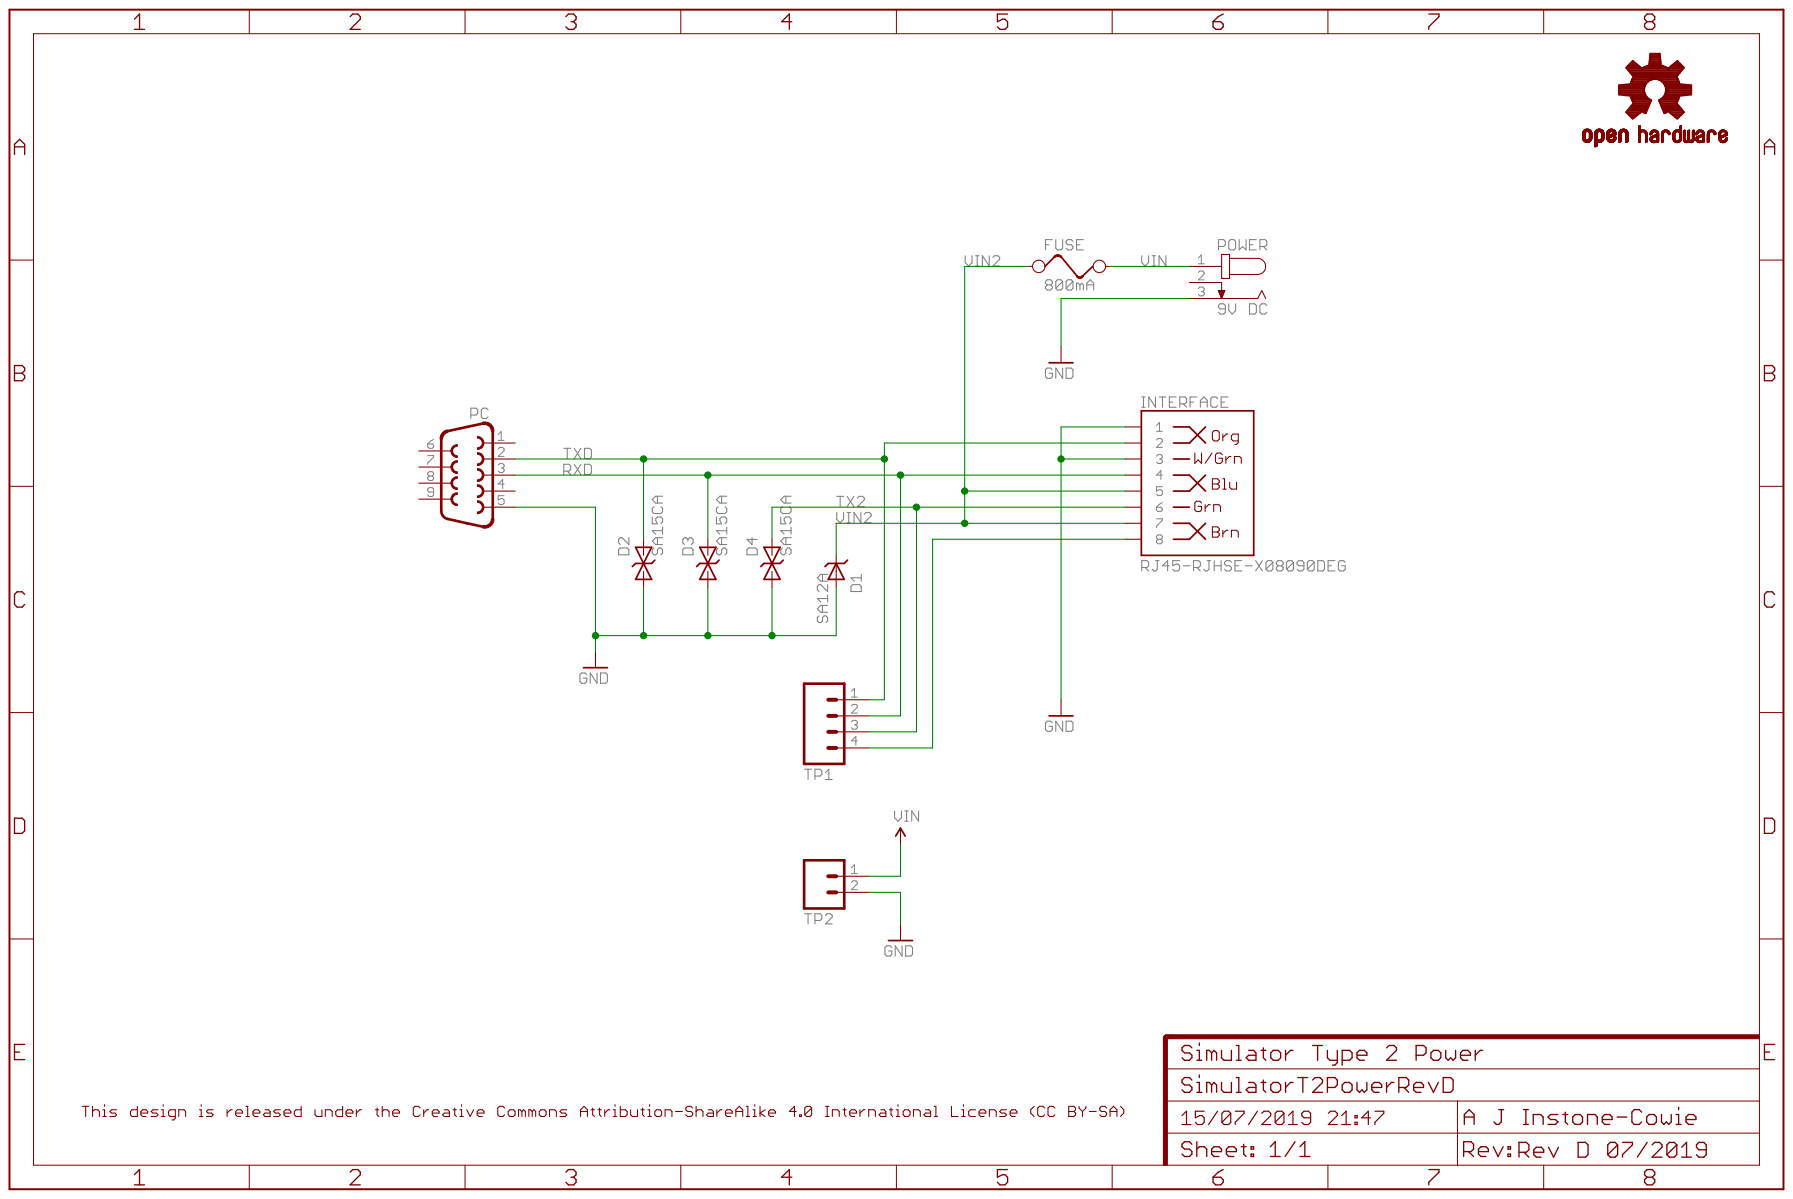
[picture p382: page 1]
