Simulators/simulator-type2/hardware/eagle/type2secondpc/SimulatorT2SecondPCRevB_brd.pdf

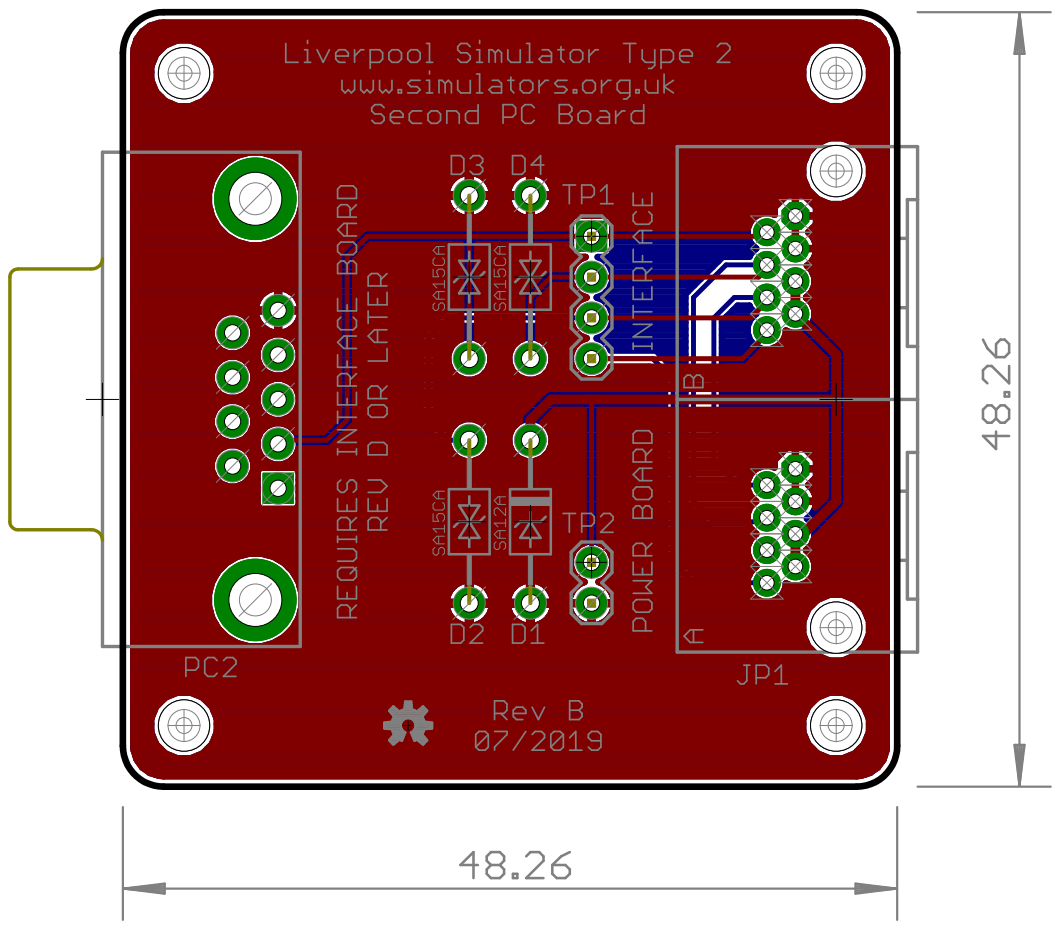
[picture p383: page 1]
