Simulators/simulator-type2/hardware/eagle/type2secondpc/SimulatorT2SecondPCRevB_panel4_brd.pdf

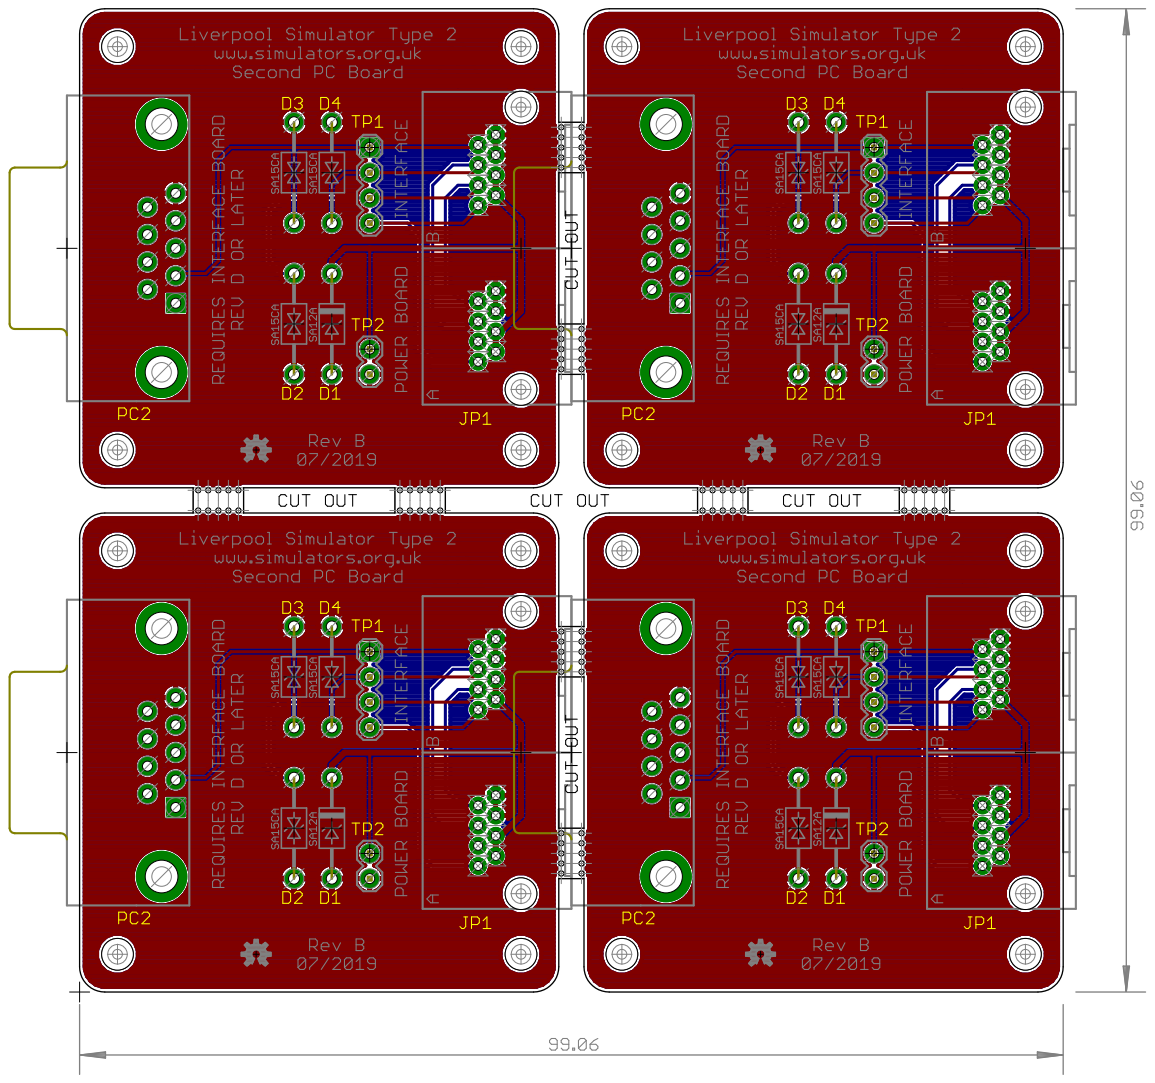
[picture p384: page 1]
