Simulators/simulator-type2/hardware/eagle/type2secondpc/SimulatorT2SecondPCRevB_sch.pdf

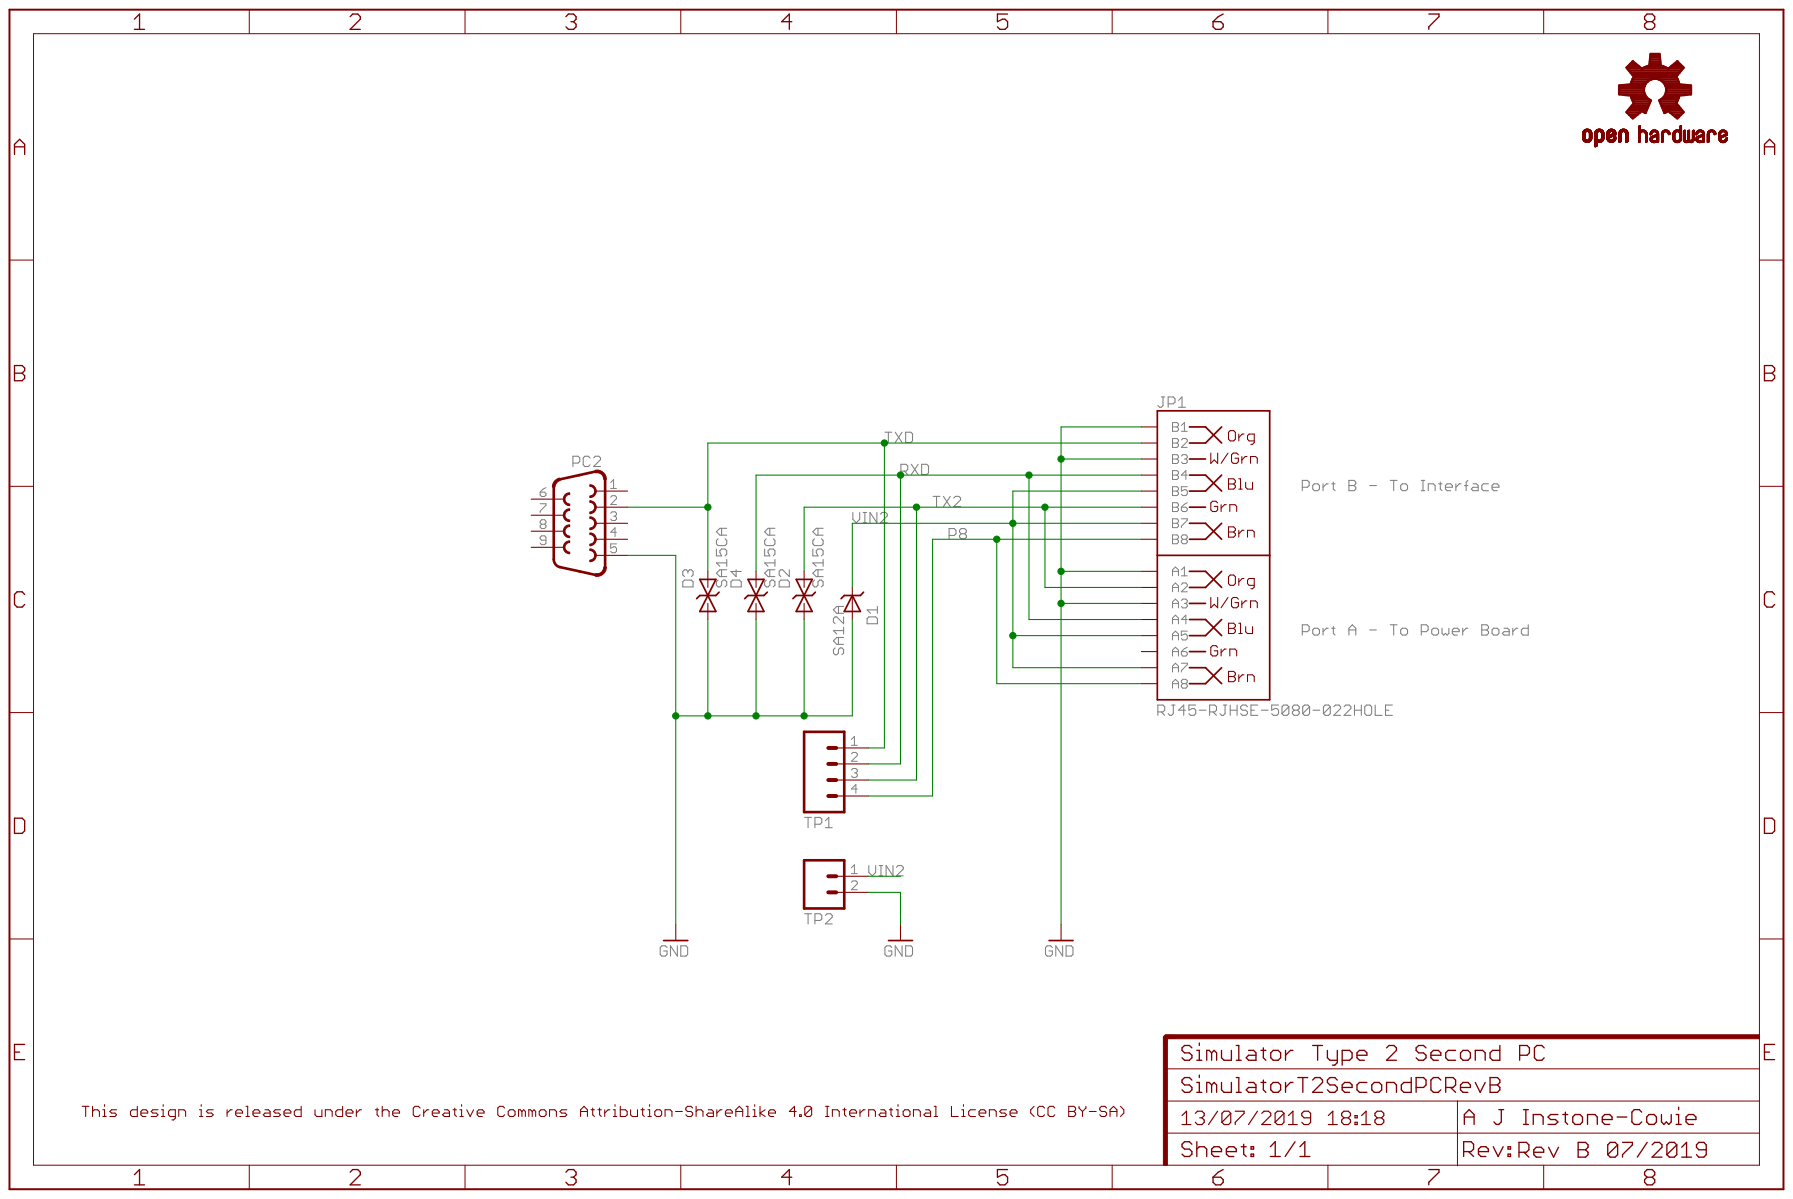
[picture p385: page 1]
