Simulators/simulator-type2/docs/source/Images/PCBs/MR Sensor/SimulatorT2MRSensorRevD_brd.pdf

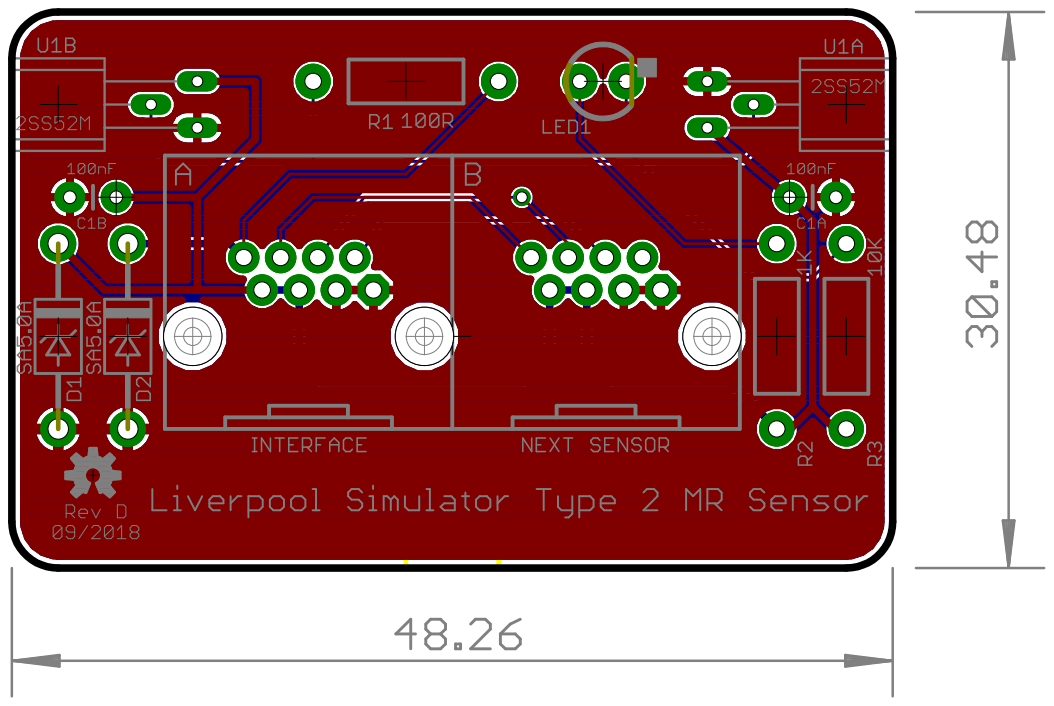
[picture p386: page 1]
