Simulators/simulator-type2/docs/source/Images/PCBs/MR Sensor/SimulatorT2MRSensorRevD_panel6_brd.pdf

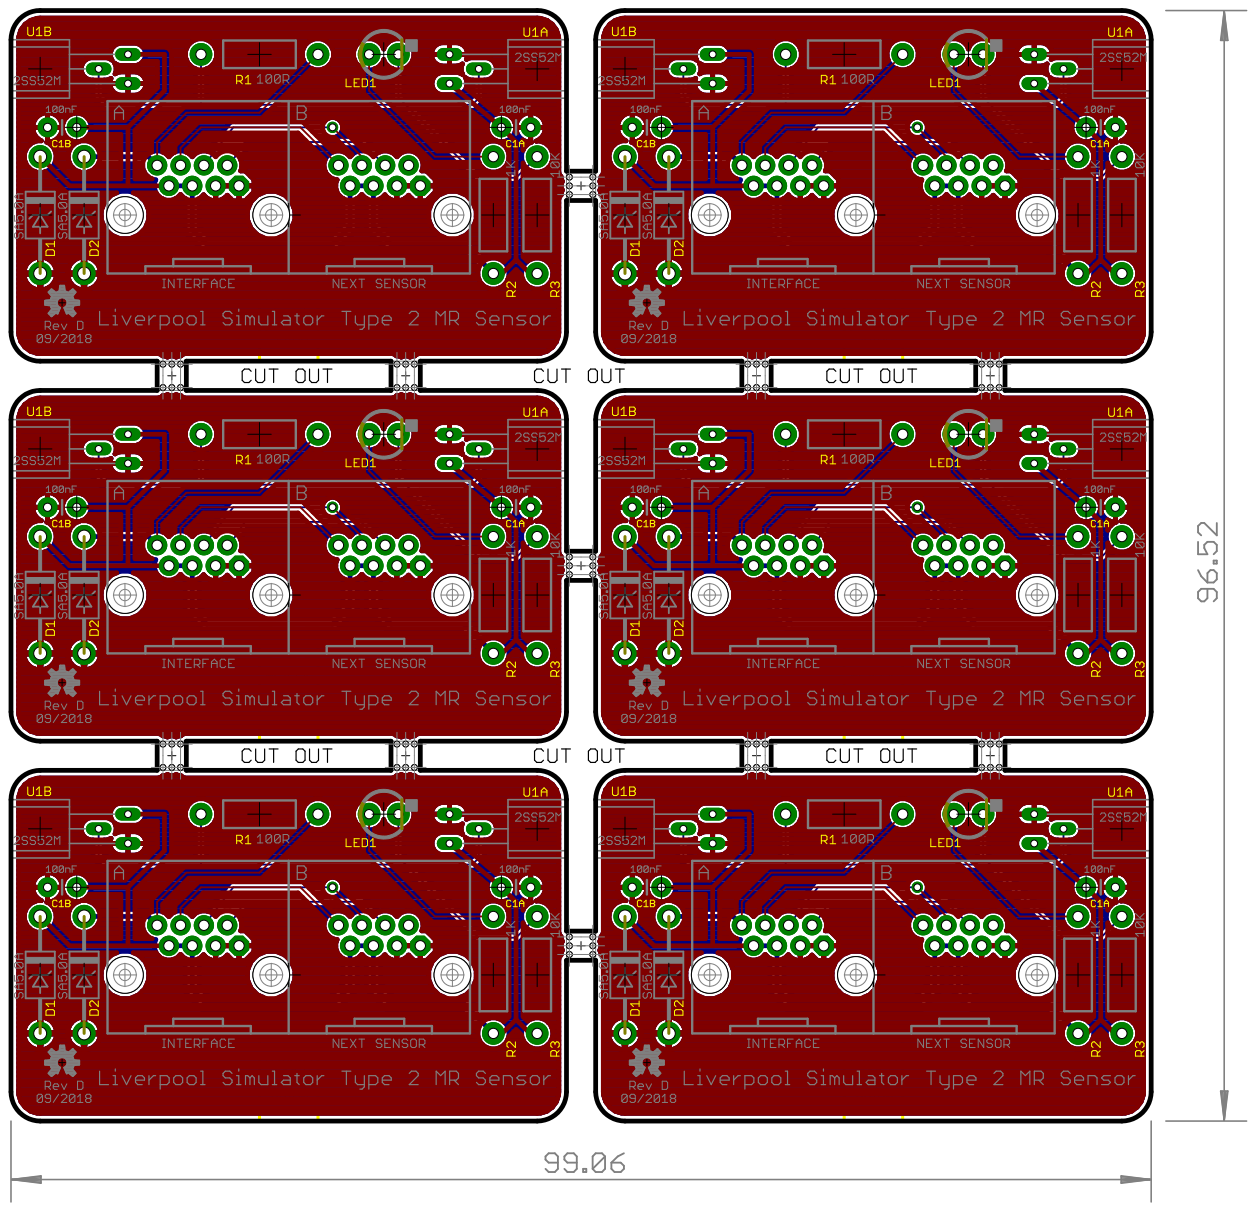
[picture p387: page 1]
