Simulators/simulator-type2/hardware/eagle/type2genericsensor/SimulatorT2GenericSensorRevC_panel6.brd

## EAGLE design hardware/eagle/type2genericsensor/SimulatorT2GenericSensorRevC_panel6.brd (2022-08-31)

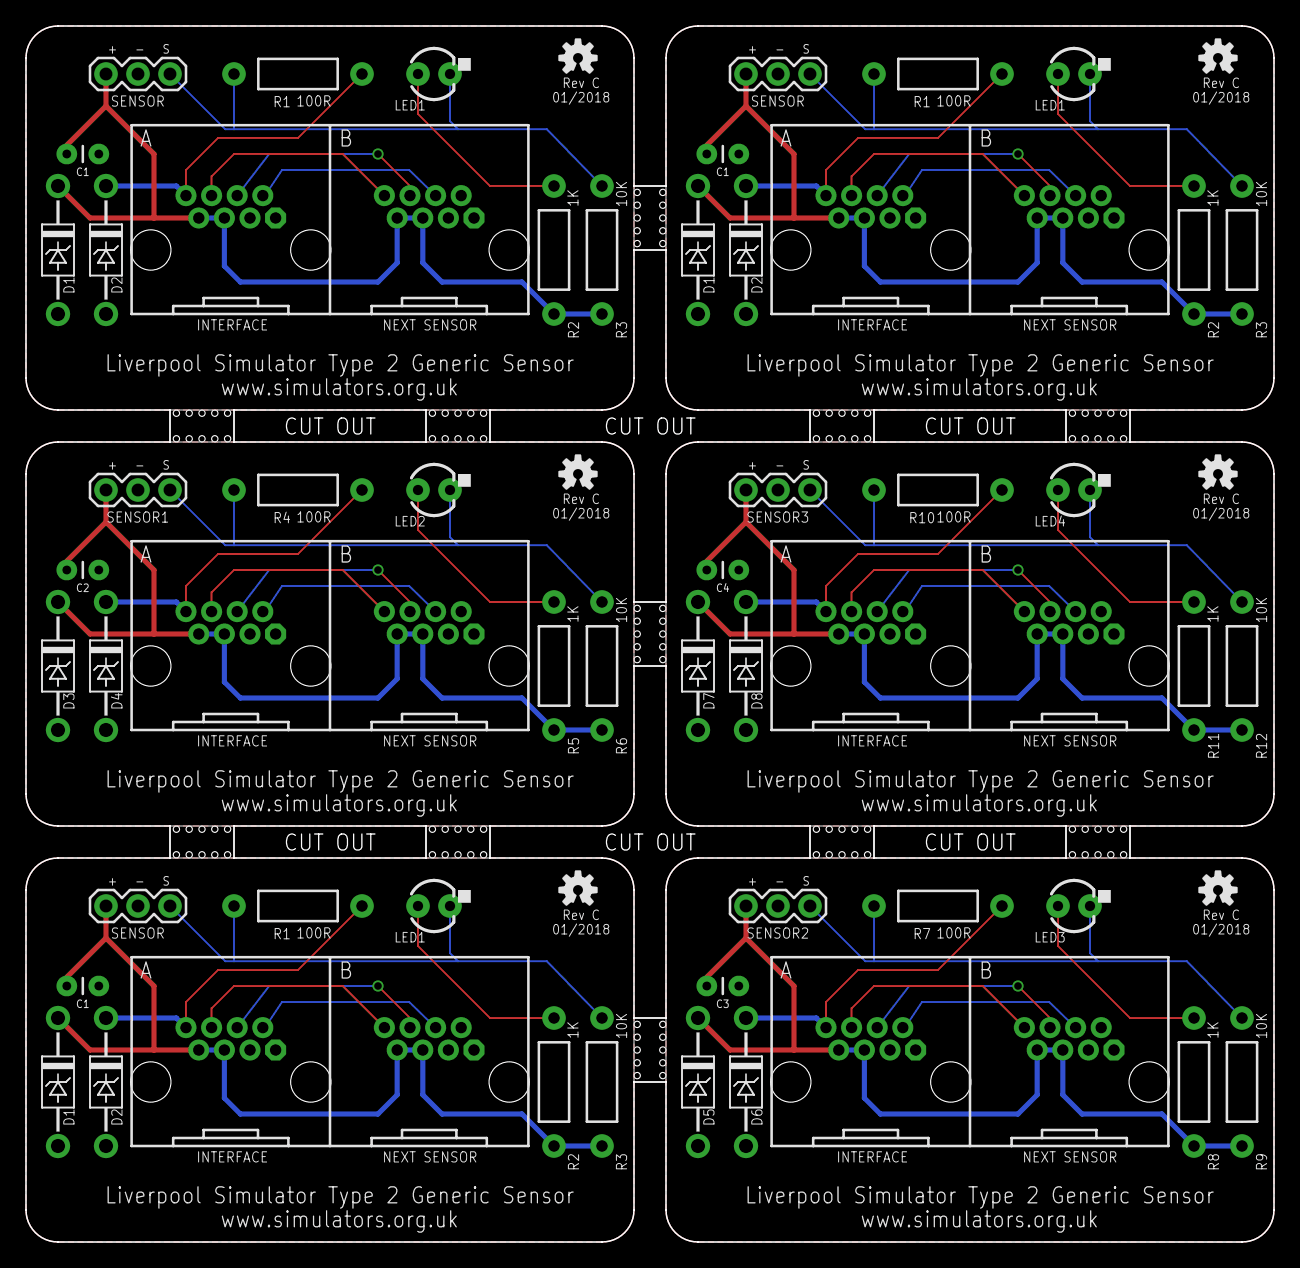
[picture p406: board SimulatorT2GenericSensorRevC_panel6.brd from above]

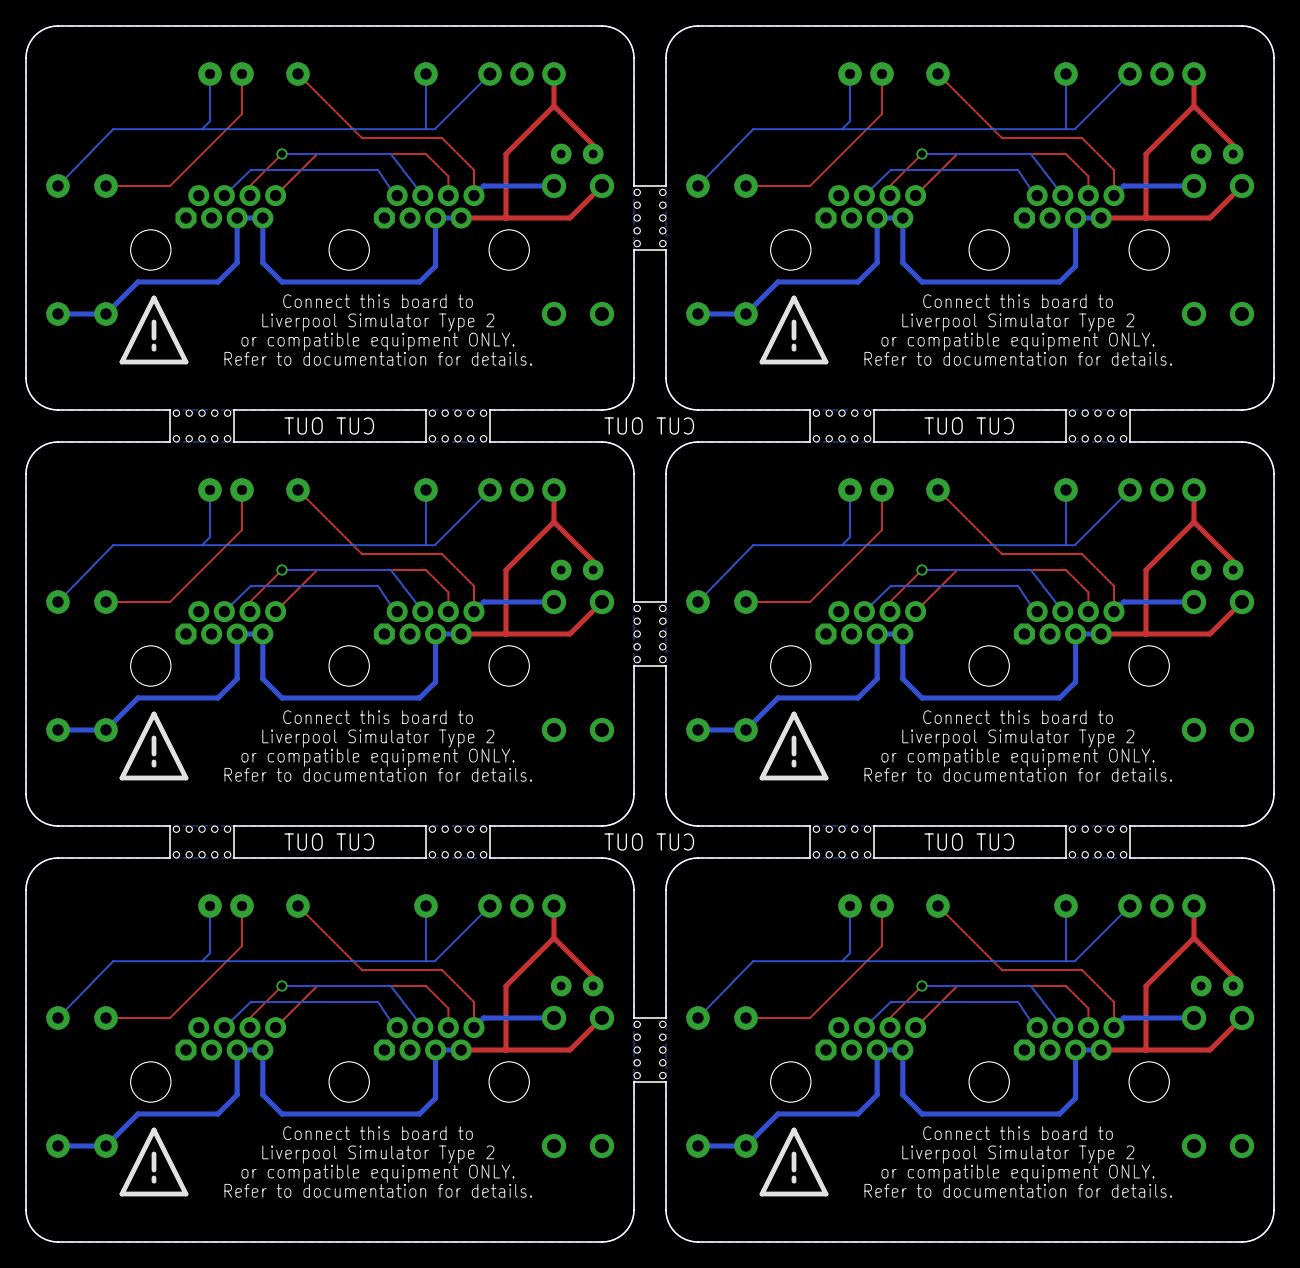
[picture p407: board SimulatorT2GenericSensorRevC_panel6.brd from below]

Board: 2 copper layers, 99.1 x 96.5 mm, 67 parts (6 on the bottom side), 48 nets.

Parts:
C1, C1_1, C1_2, C2, C3, C4: 100nF; CAP-PTH-SMALL
D1, D1_1, D1_2, D2, D2_1, D2_2, D3, D4, D5, D6, D7, D8: SA5.0A; DO41_TVS_UNI
E$1: OUTLINE_PANEL_6_5MM
E$2, E$3, E$4, E$5, E$6, E$7: WARNING_TRIANGLE_TPLACE
JP1, JP1_1, JP1_2, JP2, JP3, JP4: RJ45-RJHSE-5080-023HOLE; RJ45-RJHSE-5080-02-3HOLE
LED1, LED1_1, LED1_2, LED2, LED3, LED4: Blue; LED3MM
LOGO1, LOGO1_1, LOGO1_2, LOGO2, LOGO3, LOGO4: OSHW-LOGOS; OSHW-LOGO-S
R1, R1_1, R1_2, R4, R7, R10: 100R; AXIAL-0.4
R2, R2_1, R2_2, R5, R8, R11: 1K; AXIAL-0.4
R3, R3_1, R3_2, R6, R9, R12: 10K; AXIAL-0.4
SENSOR, SENSOR1, SENSOR2, SENSOR3: 1X03
SENSOR_1, SENSOR_2: 1X03

Connections:
!OUT!: D2.CATHODE, JP1.A8, R1.P$1
!OUT!1: D4.CATHODE, JP2.A8, R4.P$1
!OUT!2: D6.CATHODE, JP3.A8, R7.P$1
!OUT!3: D8.CATHODE, JP4.A8, R10.P$1
!OUT!4: D2_1.CATHODE, JP1_1.A8, R1_1.P$1
!OUT!5: D2_2.CATHODE, JP1_2.A8, R1_2.P$1
B1: JP2.A6, JP2.B8
B2: JP1.A6, JP1.B8
B3: JP1.A4, JP1.B6
B4: JP1.A2, JP1.B4
B5: JP2.A4, JP2.B6
B6: JP2.A2, JP2.B4
B7: JP3.A6, JP3.B8
B8: JP3.A4, JP3.B6
B9: JP3.A2, JP3.B4
B10: JP4.A6, JP4.B8
B11: JP4.A4, JP4.B6
B12: JP4.A2, JP4.B4
B21: JP1_1.A6, JP1_1.B8
B22: JP1_2.A6, JP1_2.B8
B31: JP1_1.A4, JP1_1.B6
B32: JP1_2.A4, JP1_2.B6
B41: JP1_1.A2, JP1_1.B4
B42: JP1_2.A2, JP1_2.B4
GND: C1.2, D1.ANODE, D2.ANODE, JP1.A1, JP1.A3, JP1.B1, JP1.B3, SENSOR.2
GND1: C2.2, D3.ANODE, D4.ANODE, JP2.A1, JP2.A3, JP2.B1, JP2.B3, SENSOR1.2
GND2: C3.2, D5.ANODE, D6.ANODE, JP3.A1, JP3.A3, JP3.B1, JP3.B3, SENSOR2.2
GND3: C4.2, D7.ANODE, D8.ANODE, JP4.A1, JP4.A3, JP4.B1, JP4.B3, SENSOR3.2
GND4: C1_1.2, D1_1.ANODE, D2_1.ANODE, JP1_1.A1, JP1_1.A3, JP1_1.B1, JP1_1.B3, SENSOR_1.2
GND5: C1_2.2, D1_2.ANODE, D2_2.ANODE, JP1_2.A1, JP1_2.A3, JP1_2.B1, JP1_2.B3, SENSOR_2.2
LED: LED1.A, R2.P$1
LED1: LED2.A, R5.P$1
LED2: LED3.A, R8.P$1
LED3: LED4.A, R11.P$1
LED4: LED1_1.A, R2_1.P$1
LED5: LED1_2.A, R2_2.P$1
SIG: LED1.K, R1.P$2, R3.P$1, SENSOR.3
SIG1: LED2.K, R4.P$2, R6.P$1, SENSOR1.3
SIG2: LED3.K, R7.P$2, R9.P$1, SENSOR2.3
SIG3: LED4.K, R10.P$2, R12.P$1, SENSOR3.3
SIG4: LED1_1.K, R1_1.P$2, R3_1.P$1, SENSOR_1.3
SIG5: LED1_2.K, R1_2.P$2, R3_2.P$1, SENSOR_2.3
VCC: C1.1, D1.CATHODE, JP1.A5, JP1.A7, JP1.B5, JP1.B7, R2.P$2, R3.P$2, SENSOR.1
VCC1: C2.1, D3.CATHODE, JP2.A5, JP2.A7, JP2.B5, JP2.B7, R5.P$2, R6.P$2, SENSOR1.1
VCC2: C3.1, D5.CATHODE, JP3.A5, JP3.A7, JP3.B5, JP3.B7, R8.P$2, R9.P$2, SENSOR2.1
VCC3: C4.1, D7.CATHODE, JP4.A5, JP4.A7, JP4.B5, JP4.B7, R11.P$2, R12.P$2, SENSOR3.1
VCC4: C1_1.1, D1_1.CATHODE, JP1_1.A5, JP1_1.A7, JP1_1.B5, JP1_1.B7, R2_1.P$2, R3_1.P$2, SENSOR_1.1
VCC5: C1_2.1, D1_2.CATHODE, JP1_2.A5, JP1_2.A7, JP1_2.B5, JP1_2.B7, R2_2.P$2, R3_2.P$2, SENSOR_2.1
