Simulators/simulator-type2/hardware/eagle/type2power/SimulatorT2PowerRevD_panel4.brd

## EAGLE design hardware/eagle/type2power/SimulatorT2PowerRevD_panel4.brd (2022-08-31)

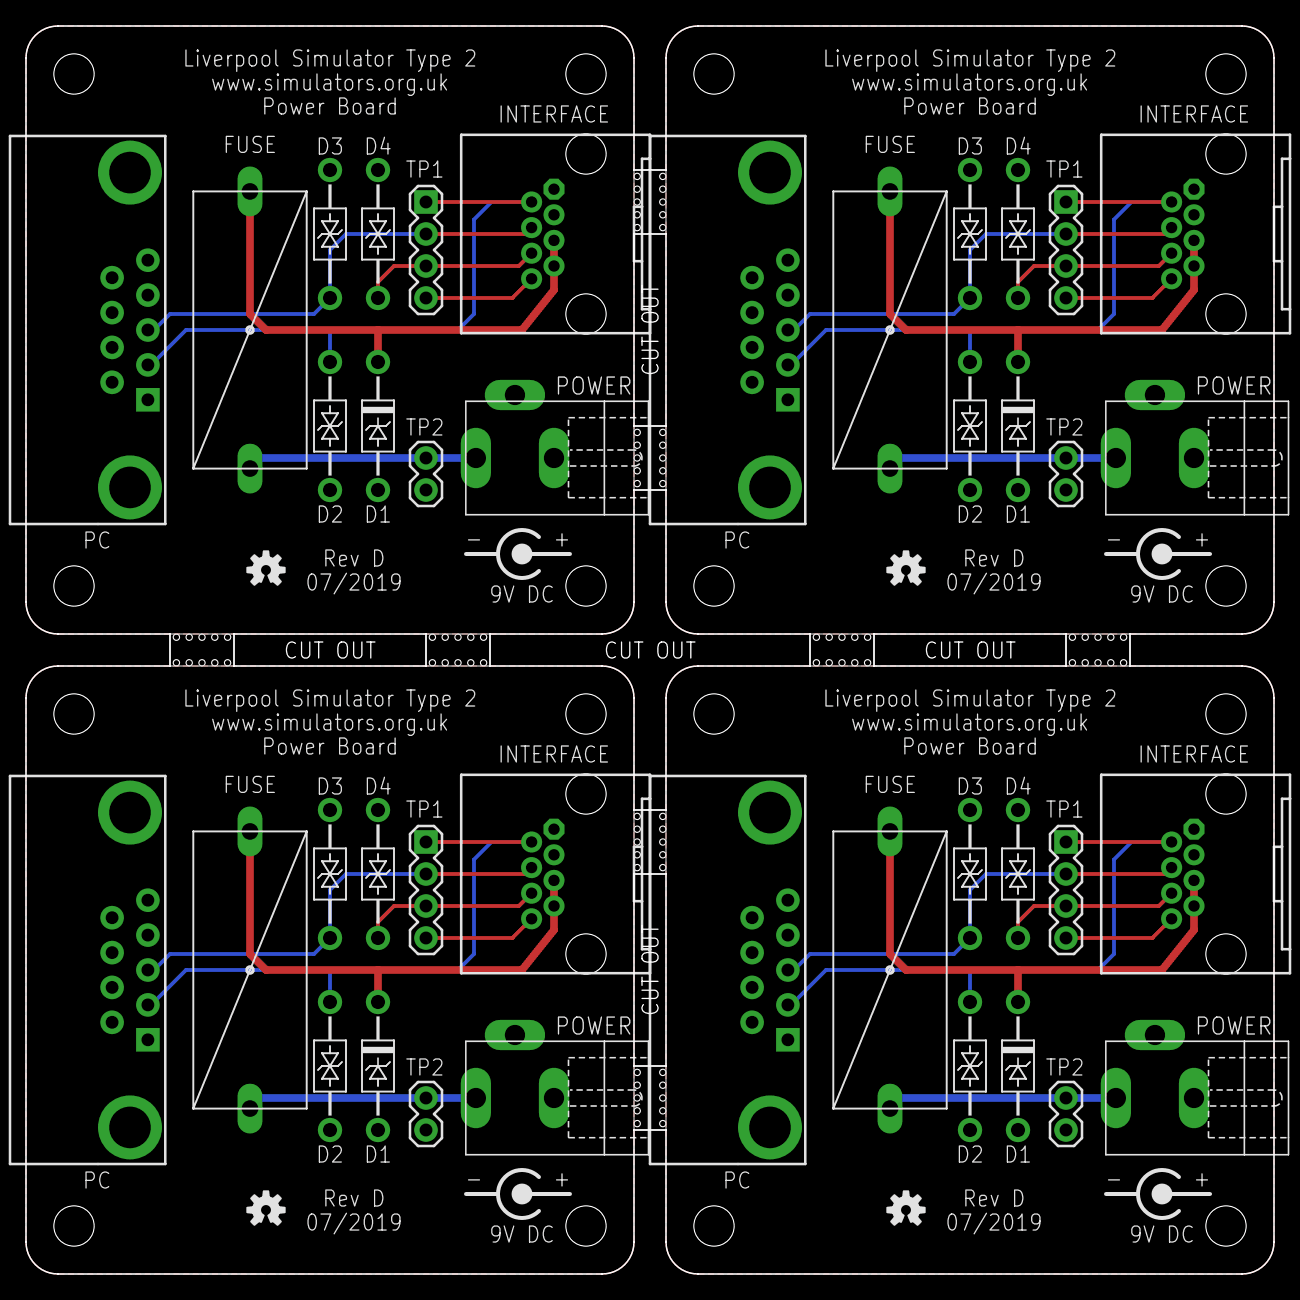
[picture p408: board SimulatorT2PowerRevD_panel4.brd from above]

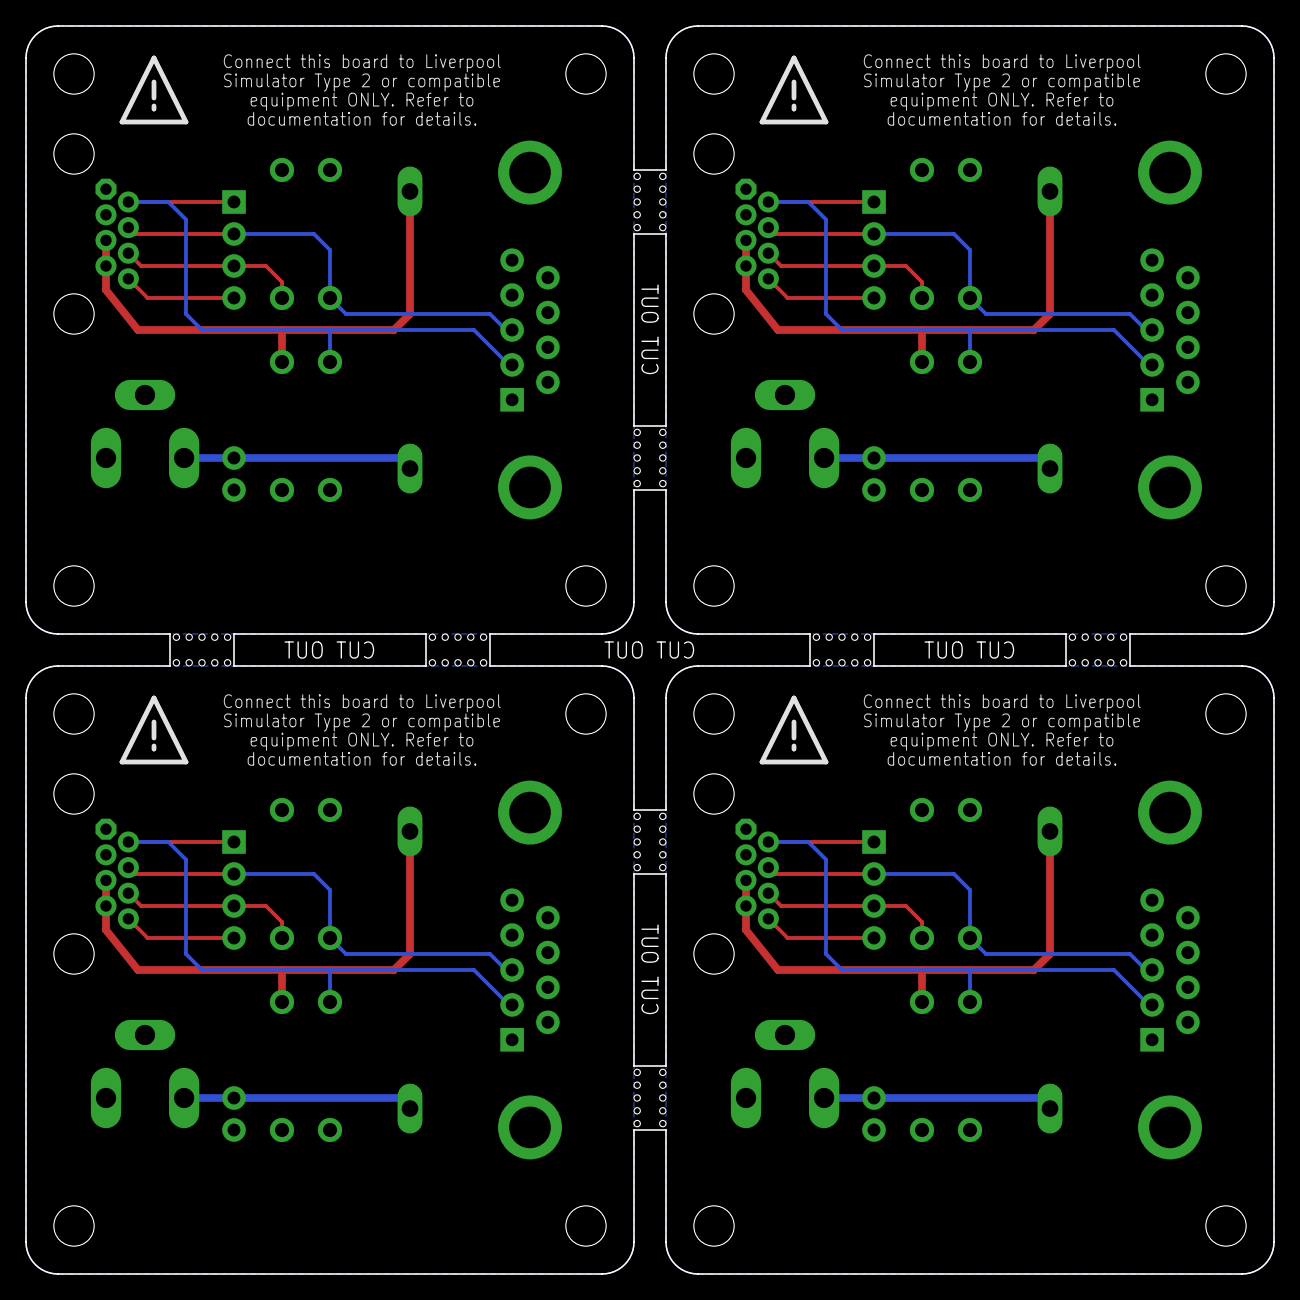
[picture p409: board SimulatorT2PowerRevD_panel4.brd from below]

Board: 2 copper layers, 99.1 x 99.1 mm, 53 parts (4 on the bottom side), 28 nets.

Parts:
D1, D1_1, D1_2, D1_3: SA12A; DO41_TVS_UNI
D2, D2_1, D2_2, D2_3, D3, D3_1, D3_2, D3_3, D4, D4_1, D4_2, D4_3: SA15CA; DO41_TVS_BI
E$1, E$3, E$4, E$5: WARNING_TRIANGLE_TPLACE
E$2: OUTLINE_PANEL_4_5MM
FUSE: 800mA; MCOMP-FUSE-HOLDER-PCB
FUSE_1, FUSE_2, FUSE_3: 800mA; MCOMP-FUSE-HOLDER-PCB
INTERFACE: RJ45-RJHSE-X08090DEG; RJ45-RJHSE-5080
INTERFACE_1, INTERFACE_2, INTERFACE_3: RJ45-RJHSE-X08090DEG; RJ45-RJHSE-5080
LOGO1, LOGO1_1, LOGO1_2, LOGO1_3: OSHW-LOGOS; OSHW-LOGO-S
PC: MULTICOMP-DB9-FEMALE-PCB-90DEG
PC_1, PC_2, PC_3: MULTICOMP-DB9-FEMALE-PCB-90DEG
POWER: 9V DC; CLIFF-FC681465P-DC-JACK
POWER_1, POWER_2, POWER_3: 9V DC; CLIFF-FC681465P-DC-JACK
TP1, TP1_1, TP1_2, TP1_3: 1X04
TP2, TP2_1, TP2_2, TP2_3: 1X02
U$1, U$1_1, U$1_2, U$1_3: CENTRE-POS-SILK

Connections:
GND: D1.ANODE, D2.A, D3.A, D4.A, INTERFACE.1, INTERFACE.3, PC.5, POWER.3, TP2.2
GND1: D1_1.ANODE, D2_1.A, D3_1.A, D4_1.A, INTERFACE_1.1, INTERFACE_1.3, PC_1.5, POWER_1.3, TP2_1.2
GND2: D1_2.ANODE, D2_2.A, D3_2.A, D4_2.A, INTERFACE_2.1, INTERFACE_2.3, PC_2.5, POWER_2.3, TP2_2.2
GND3: D1_3.ANODE, D2_3.A, D3_3.A, D4_3.A, INTERFACE_3.1, INTERFACE_3.3, PC_3.5, POWER_3.3, TP2_3.2
P8: INTERFACE.8, TP1.4
P81: INTERFACE_1.8, TP1_1.4
P82: INTERFACE_2.8, TP1_2.4
P83: INTERFACE_3.8, TP1_3.4
RXD: D3.C, INTERFACE.4, PC.3, TP1.2
RXD1: D3_1.C, INTERFACE_1.4, PC_1.3, TP1_1.2
RXD2: D3_2.C, INTERFACE_2.4, PC_2.3, TP1_2.2
RXD3: D3_3.C, INTERFACE_3.4, PC_3.3, TP1_3.2
TX2: D4.C, INTERFACE.6, TP1.3
TX21: D4_1.C, INTERFACE_1.6, TP1_1.3
TX22: D4_2.C, INTERFACE_2.6, TP1_2.3
TX23: D4_3.C, INTERFACE_3.6, TP1_3.3
TXD: D2.C, INTERFACE.2, PC.2, TP1.1
TXD1: D2_1.C, INTERFACE_1.2, PC_1.2, TP1_1.1
TXD2: D2_2.C, INTERFACE_2.2, PC_2.2, TP1_2.1
TXD3: D2_3.C, INTERFACE_3.2, PC_3.2, TP1_3.1
VIN: FUSE.2, POWER.1, TP2.1
VIN1: FUSE_1.2, POWER_1.1, TP2_1.1
VIN2: D1.CATHODE, FUSE.1, INTERFACE.5, INTERFACE.7
VIN3: FUSE_2.2, POWER_2.1, TP2_2.1
VIN4: FUSE_3.2, POWER_3.1, TP2_3.1
VIN21: D1_1.CATHODE, FUSE_1.1, INTERFACE_1.5, INTERFACE_1.7
VIN22: D1_2.CATHODE, FUSE_2.1, INTERFACE_2.5, INTERFACE_2.7
VIN23: D1_3.CATHODE, FUSE_3.1, INTERFACE_3.5, INTERFACE_3.7
