Simulators/simulator-type2/hardware/eagle/type2power/SimulatorT2PowerRevB_panelized.brd

## EAGLE design hardware/eagle/type2power/SimulatorT2PowerRevB_panelized.brd (2018-09-01)

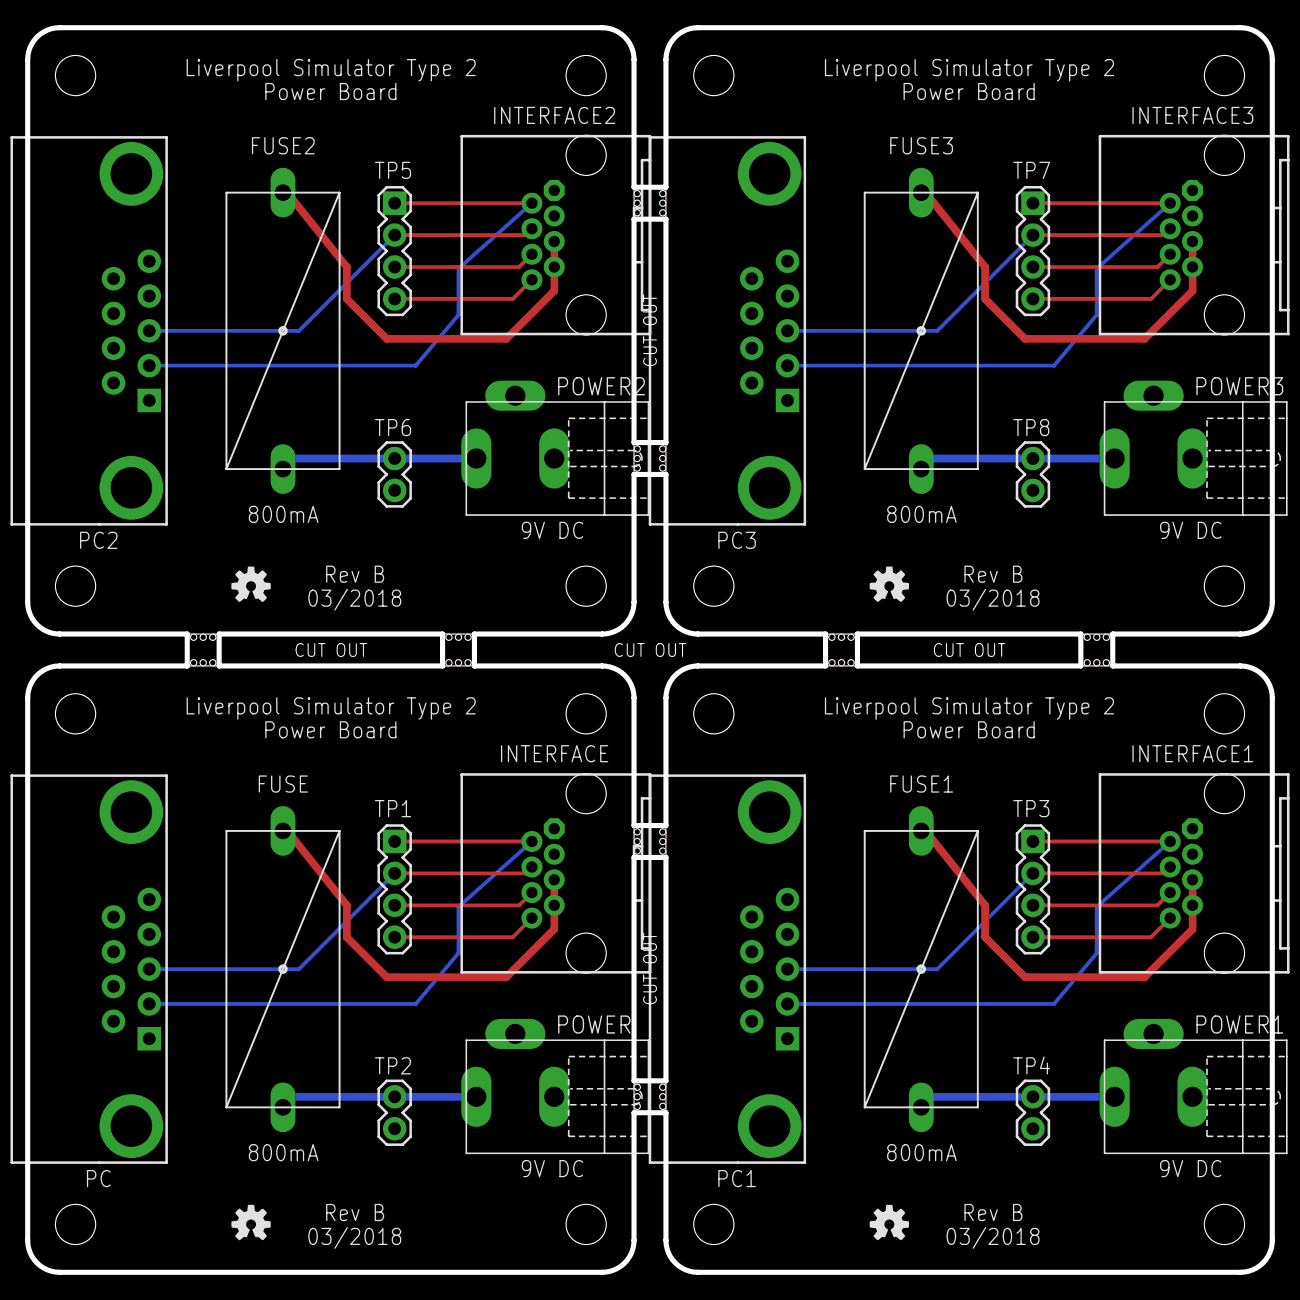
[picture p410: board SimulatorT2PowerRevB_panelized.brd from above]

Board: 2 copper layers, 99.1 x 99.1 mm, 36 parts (0 on the bottom side), 28 nets.

Parts:
E$1, E$2, E$3, E$4, E$5, E$6, E$7, E$8: STAMP_HOLES
FUSE, FUSE1, FUSE2, FUSE3: 800mA; MCOMP-FUSE-HOLDER-PCB
INTERFACE, INTERFACE1, INTERFACE2, INTERFACE3: RJ45-RJHSE-X08090DEG; RJ45-RJHSE-5080
LOGO1, LOGO2, LOGO3, LOGO4: OSHW-LOGOS; OSHW-LOGO-S
PC, PC1, PC2, PC3: MULTICOMP-DB9-FEMALE-PCB-90DEG
POWER, POWER1, POWER2, POWER3: 9V DC; CLIFF-FC681465P-DC-JACK
TP1, TP3, TP5, TP7: 1X04
TP2, TP4, TP6, TP8: 1X02

Connections:
GND: INTERFACE.1, INTERFACE.3, PC.5, POWER.3, TP2.2
GND1: INTERFACE1.1, INTERFACE1.3, PC1.5, POWER1.3, TP4.2
GND2: INTERFACE2.1, INTERFACE2.3, PC2.5, POWER2.3, TP6.2
GND3: INTERFACE3.1, INTERFACE3.3, PC3.5, POWER3.3, TP8.2
P1: INTERFACE1.6, TP3.3
P2: INTERFACE1.8, TP3.4
P3: INTERFACE2.6, TP5.3
P4: INTERFACE2.8, TP5.4
P5: INTERFACE3.6, TP7.3
P6: INTERFACE.6, TP1.3
P7: INTERFACE3.8, TP7.4
P8: INTERFACE.8, TP1.4
RXD: INTERFACE.4, PC.3, TP1.2
RXD1: INTERFACE1.4, PC1.3, TP3.2
RXD2: INTERFACE2.4, PC2.3, TP5.2
RXD3: INTERFACE3.4, PC3.3, TP7.2
TXD: INTERFACE.2, PC.2, TP1.1
TXD1: INTERFACE1.2, PC1.2, TP3.1
TXD2: INTERFACE2.2, PC2.2, TP5.1
TXD3: INTERFACE3.2, PC3.2, TP7.1
VIN: FUSE.2, POWER.1, TP2.1
VIN1: FUSE1.2, POWER1.1, TP4.1
VIN2: FUSE.1, INTERFACE.5, INTERFACE.7
VIN3: FUSE1.1, INTERFACE1.5, INTERFACE1.7
VIN4: FUSE2.2, POWER2.1, TP6.1
VIN5: FUSE2.1, INTERFACE2.5, INTERFACE2.7
VIN6: FUSE3.2, POWER3.1, TP8.1
VIN7: FUSE3.1, INTERFACE3.5, INTERFACE3.7
