Simulators/simulator-type2/firmware/Type2Interface_v3_8/Debug_Functions.ino

/*
Liverpool Ringing Simulator Project
Simulator Interface v3.8
Debug Functions

Copyright 2014-2025 Andrew J Instone-Cowie.

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
You should have received a copy of the GNU General Public License
along with this program.  If not, see <http://www.gnu.org/licenses/>.
*/

/*
*********************************************************************************************
*                                 Function debugThisChannel()                               *
*********************************************************************************************
*/

// If debugging is enabled, and debugging is turned on for this channel in the mask, return TRUE.
// Otherwise return FALSE. debugMode and debugChannelMask are global, so no need to pass them in
// via the function.

boolean	debugThisChannel( int channel ) {

	if ( debugMode && bitRead( debugChannelMask, channel ) ) {
		// Debugging is enabled and turned on for this channel.
		return true;
	}
	else
	{
		return false;
	}
	
}

/*
*********************************************************************************************
*                                Function isDebugFlagSet()                                  *
*********************************************************************************************
*/

// If debugging is enabled, if any of the specified bits are set in the debugFlagMask,
// return TRUE. Otherwise return FALSE. debugFlagsMask is global, so no need to pass them in
// via the function. We only call this if we are known to be in debug mode already.

// The flags parameter is either a single bit value (1/2/4/8/16/etc), or more than one value
// ORd together in the invocation of the function.

boolean	isDebugFlagSet( word flags ) {

	if ( debugFlagsMask & flags ) {
		// One or more of the specified flags are set.
		return true;
	}
	else
	{
		return false;
	}
	
}

/*
*********************************************************************************************
*                               Function printDebugFlagName()                               *
*********************************************************************************************
*/

// Passed the numeric debug flag bit number, prints a textual representation of that debug
// flag, followed by a newline.

void printDebugFlagName( int level ) {

	// So this is reasonably horrible, but as I can't do F() globally,
	// this will have to do to get the text version into flash...	
	switch ( level ) {
	case 0: // DEBUG_PULSE_TIMER
		Serial.print(F("DEBUG_PULSE_TIMER"));
		break;
	case 1: // DEBUG_SHOW_MISFIRES
		Serial.print(F("DEBUG_SHOW_MISFIRES"));
		break;
	case 2: // DEBUG_SHOW_DEBOUNCE
		Serial.print(F("DEBUG_SHOW_DEBOUNCE"));
		break;
	case 3: // DEBUG_SHOW_LED
		Serial.print(F("DEBUG_SHOW_LED"));
		break;
	case 4: // DEBUG_SWING_TIMER
		Serial.print(F("DEBUG_SWING_TIMER"));
		break;
	default: // Some other debugLevel value
		Serial.print(F("Invalid"));
		break;
	}
	
}

/*
*********************************************************************************************
*                             Function printDebugFlagsSet()                                 *
*********************************************************************************************
*/

// List the debug flags which are currently set in debugFlagsMask, as a space separated list
void printDebugFlagsSet( void ) {
	int i;
	for ( i = 0; i < maxDebugFlags; i++ ) {
		// Print the value of the bits.
		if ( bitRead( debugFlagsMask, i ) ) {
			// The bit is set
			Serial.print("\t");
			printDebugFlagName( i );
			Serial.println("");
		}
	}
}


/*
*********************************************************************************************
*                                  Function runTestMode()                                   *
*********************************************************************************************
*/

// Generate the selected test pattern, forever.
// This loop runs as tightly as possible, to generate the best possible test pattern, and
// therefore doesn't run around loop(). As a result the CLI cannot be used to cancel test mode.
// Test mode uses numChannels, which is calculated from the highest channel enabled in the
// enabledChannelMask, so by setting this (option E in the CLI), the number of test mode bells
// can be set.

void runTestMode( int mode ) {
	
	// This section runs only once when channel 1 enters TEST_MODE state.
	// After this, the test ringing runs in an infinite loop.
	
	termSetFor( TERM_CONFIRM );
	Serial.println("");
	Serial.print(F("Test Mode "));
	Serial.print(testMode);
	
	switch ( mode ) {
		
	case 1: // Rounds 
		Serial.print(F(" (Rounds on "));
		break;

	case 2: // Firing
		Serial.print(F(" (Firing on "));
		break;
	}
	
	Serial.print(numChannels);
	Serial.print(F(") in "));
	Serial.print(testStartDelay);
	Serial.print(F(" seconds..."));
	termSetFor( TERM_DEFAULT );
	digitalWrite( LED, HIGH);
	delay( testStartDelay * 1000 ); //testStartDelay is in seconds.
	
	// loop counters
	int j, k;
	
	switch ( mode ) {
		
	case 1: // Rounds 
		digitalWrite( LED, HIGH);
		//ring rounds forever
		while(true) {
			// twice - handstroke and backstroke
			for ( j = 0; j < 2; j++ ) {
				for ( k = 0; k < numChannels; k++ ) {
					Serial.print( defaultBellStrikeChar[k] );
					delay(testInterval);
				}
			}
			// open handstroke lead
			delay(testInterval);
			// flash LED slowly
			digitalWrite( LED, !digitalRead( LED ));
		} //while true
		break;

	case 2: // Firing
		digitalWrite( LED, HIGH);
		//ring the test pattern forever
		while(true) {
			for ( j = 0; j < numChannels; j++ ) {
				Serial.print( defaultBellStrikeChar[j] );
			}
			delay( testInterval * numChannels );
			// flash LED slowly
			digitalWrite( LED, !digitalRead( LED ));
		} //while true
		break;
	}
}
